tranquilWorks/gr86-cca-telemetry/docs/engineering/rvb22/current/EXECUTION_PLAN.md

# I32 procurement redline effectivity — 2026-09-15

The completed native procurement redline and affected numerical results are controlled by [../analyses/i32/procurement_redline/README.md](../analyses/i32/procurement_redline/README.md). Earlier source hashes, substitutions, power/thermal values and native-output pointers below are historical where superseded. Physical acceptance requirements remain in force; no historical criterion ledger is re-adjudicated by this update. The original text is preserved in `analyses/i32/procurement_redline/history/pre_redline/current/EXECUTION_PLAN.md`.

---

# I22 closure plan and current source

This iteration starts at I21 commit `550d87fea69147e131fd71603d02204a44c903f1` on PR #45. The user confirmed Adafruit 851 and 960 and requested another iteration. The complete I21 redline/criterion state was frozen before the checks. I22 corrects the accessory model, adds the omitted mechanical height allowance, completes independent package overlays and bounded via/RF reviews, and reevaluates all 290 original criteria. It closes six: LIB-02, LIB-08, VIA-06, SI-12, GPS-01 and MECH-03. Counts become 140 closed, 146 open and four not applicable. All 357 recorded redline identities remain visible; that history count is not the count of open criteria.

Confirmed inputs are Honeywell MIPAN2XX150PSAAX, the GR86 ASC harness per Timurrr, Adafruit 851/960, JLCPCB fabrication and dashboard use. Equivalent numerical power/RF/thermal models and circuit, firmware, mechanical and assembly corrections are authorized. The unchanged design case is 4.815 W, 65°C bulk air, 70°C landings and 70 kPa. No engine-bay environment or reduced dashboard requirement is introduced.

| Workstream | I22 result | Next closure action |
|---|---|---|
| Native CAD and target build | Verified I20 source remains current, with zero native findings and 153 resolved models. I22 does not change CAD or firmware. | Rerun the pinned native workflow after any CAD/firmware change and bind the resulting exports. |
| Package orientation and exposed pads | 12 manufacturer top/bottom overlays, 151 signal lands, all 20 GPS pad functions and 12 wrong-orientation negative controls pass. Exact exposed-pad net/mask/thermal construction reviewed. | Retain alternative-land and stencil conditions; obtain the original independent human drawing review under DRW-03. |
| Mechanical model and assembly | Full 1.71 mm height stack replaces 1.20 mm; 1,154 populated and 776 mated checks pass. Smallest separation is 0.120 mm at R408/T03. Cable uses 150 ±3 mm and a 2.0 mm OD receiving envelope. | Verify exact supplied plug dimensions, carrier/foil materials, retention and installed construction. Recheck every cooling revision against these bounds. |
| Via current and drilling | All 322 vias pass the conditional 2 A self-heating screen, maximum 5.103 K against 10 K. Nominal drills agree with native exports. | Resolve exact finished-hole/pin/hardware fit, drawing/DFM agreement and supplier minimum wall/fill/cap conditions. |
| Board RF and digital returns | Analysis-only SI-12 scope is justified by the existing 3,981,312-case board network, minimum 10.219 dB return loss and maximum 0.867 dB insertion loss. All 12 RF segments retain adjacent ground. | Keep actual stack/device allocations, antenna/bias and installed GPS criteria separate. Bound or reroute the 54 digital adjacent-plane interruptions; alternate ground presence alone is insufficient. |
| Accessory interface | User-confirmed 851/960 pair; typical 3.3 V current is 9.8 mA. Exact module detection and current-limit applicability reviewed. | Verify delivered bias voltage, hot/cold current, faults, miniature-plug dimensions and standard-SMA center contacts. |
| Thermal | Fine model remains 143.800°C maximum board region and mesh-sensitive. A 60°C-rated 851 cannot meet 65°C passive boundaries. | Resolve package/local-air data, mesh/topology bounds and a realizable cooling path. Settle accessory rating or verified installation environment; passive contact improvements cannot close that 5 K rating conflict. |
| Remaining original review | All criteria retain their original questions and evidence requirements. WCA-07 still lacks a guaranteed hot/low-current optical bound. | Advance the remaining design calculations, then supplier, independent-review and physical acceptance items according to their actual scope. |

For every subsequent iteration, freeze all open criteria and every newly observed redline. Record a disposition for each finding, including the correction, evidence or exact unmet condition. Select one coordinated revision only after reviewing its power, RF, thermal, populated clearance, materials and service effects together. Regenerate all affected native/model outputs, compare every original criterion with the exact candidate, preserve failed trials and repeat. A combined finding remains open when one of its constituent requirements remains unresolved.

The next board-changing iteration should address thermal paths and digital returns together. Preserve full load/environment bounds until an enforceable alternative is designed and verified. Evaluate candidate heat paths against the ESP32 antenna region, J401 cable, C206 tab, insulation and full 1.71 mm height stack before promoting the geometry. Reconcile current package boundaries before presenting board-region temperatures as device margins.

Physical unit, supplier-process, installed harness/ground, phone/vehicle, material lifetime and environmental requirements remain explicit in the register. PR #45 is the authorized forwarding destination. Fabrication, merge, flashing and live vehicle actions are outside this iteration.
