tranquilWorks/gr86-cca-telemetry/docs/engineering/rvb22/analyses/i32/QUALIFICATION_AND_SERVICE.md

# I32 procurement redline effectivity — 2026-09-15

The completed native procurement redline and affected numerical results are controlled by [procurement_redline/README.md](procurement_redline/README.md). Earlier source hashes, substitutions, power/thermal values and native-output pointers below are historical where superseded. Physical acceptance requirements remain in force; no historical criterion ledger is re-adjudicated by this update. The original text is preserved in `analyses/i32/procurement_redline/history/pre_redline/analyses/i32/QUALIFICATION_AND_SERVICE.md`.

---

# I32 qualification and service conditions

No hardware, vehicle connection, programming, supplier approval or physical test was performed. These are deterministic first-article acceptance instructions. Retained I26 oil, GPS, RF, CAN, installation and mechanical criteria continue to apply. The uncertainty rule is unchanged: a measured value plus its relevant uncertainty must stay inside an upper limit; subtract uncertainty for a lower limit. Model assumptions are not measurement tolerances.

| Gate | Setup and acceptance |
|---|---|
| Cold start and boot | At the defined normal input corners, including the retained4.75–5.25 V upstream interface, and component/temperature samples, record upstream5 V, isolated VIN, source3.3 V, main3.3 V at U201 ground, U152 PG, actual U151 EN, U153 CT/output, reset and both converter currents. Test no load,20 mA pre-reset,0.45 A boot/run and0.75 A from power-on. Exactly one reset release; no SNS retry or missing boot during normal startup. Confirm the pre-reset allocation independently; typical ESP32 EN-low current is not a hot maximum. |
| Load steps and release | Exercise0.45↔0.75 A and representative MCU/BLE loads with fast edges. After READY, main including ripple/uncertainty must remain above3.116050 V and at or below3.6 V, without unintended resets. Also record the source node separately. The derivative's16.51 mV lower and28.61 mV upper margins do not absorb unknown silicon dynamics automatically. |
| U151 reverse discharge | Test normal unplug, upstream UV/OV disconnect,10/100 ms reapplication, unequal auxiliary loads, and no externally imposed off-load. While source>0.3 V, isolated VIN minus source must remain≥−0.3 V, including differential-probe error. Correlate enabled bidirectional switch behavior, disabled reverse blocking, hot leakage and discharge transistor transfer behavior. Reset during an imposed supply fault is intentional; successful single recovery after a stable return is required. |
| Timing and startup dissipation | Verify C15933 nF at0.00876628–0.01461858 s/V and C16668 nF at0.01804688–0.03009768 s/V, the250 us allocated worst fault response, actual EN sequencing and reset delay180–420 ms. CT values extend TI's approximate formula beyond the10 nF table example; they are not guaranteed model constants. Confirm no U152/U153 thermal shutdown during worst storage charging or repeated recovery. |
| Input transient survival | Apply the exact source waveforms/R/L/repetition in `INPUT_PROTECTION.md`, including hot/cold clamp envelopes, on an isolated current-limited fixture. Simultaneously measure Q101 VDS/VGS/ID, controller VIN/UV/OV/SHDN/gate, D101 voltage/current, D102/D103/D105 clamp trajectories and downstream VIN5. Require Q101≤200 V and±20 V gate, D101≤600 V reverse, U101 per-pin limits, and the temperature-adjusted SOA/pulse bounds. No avalanche, latch-up, unintended fuse opening or permanent parameter drift is accepted. Functional UV/OV shutdown is expected; output-only measurements cannot prove component stress acceptance. |
| Short/fuse coordination | The LTC4367 voltage disconnect is not a current limiter. Confirm source fuse/wire protection, prospective fault current, ground-loss handling and clearing under the retained harness contract. Fuse nominal0.80 A²s is not a guaranteed clearing or pulse-survival limit. F101 local ambient≤105 C; apply its current-temperature/continuous derating. |
| Sustained power | Preserve160 MHz, BLE+3 dBm, Wi-Fi off,≤120 notifications/s, and sliding1 s/60 s main current≤0.45 A. Each converter must meet the retained≥80% condition or an approved partitioned measured-loss alternative. Additionally, actual total heat must remain within2.940859375 W. The worst leakage stack at exactly80% for both gives3.062582 W and is **not an accepted release state**. At U151 exactly80%, the same-budget calculation requires U121≥83.3396%; other efficiencies may be accepted only by a complete power-flow/heat calculation. Use simultaneous instantaneous V×I and avoid double-counting magnetic loss. |
| Hot soak and Rev A correlation | Use adopted C05/W02/T03, final enclosure/harness/orientation at65 C bulk cabin air. Immediate U201 air≤85 C; monitor shield, board hot region, U121/U151/U152/U153, both polymer capacitors, fuse, LED and cooling landings. Stabilize every monitored temperature at<0.1 C/min for30 consecutive minutes with zero unexpected resets/latch-ups. Continue the representative run long enough to cover the historical five-minute failure and final stabilization. A millisecond startup simulation does not prove that failure mechanism eliminated. |
| Thermal model correlation | The new actual-loss vector gives107.36427 C on0.25 mm mesh plus5.85646 C one-step allowance =113.22073 C board-region screen. The retained I25 heat vector on new copper gives113.39905 C similarly. Neither is mesh convergence, junction or immediate-air temperature. **The older112.88298 C physical correlation trigger remains in force**: exceeding it reopens correlation; I32 does not raise that acceptance trigger merely to pass. Actual loss/contact/air data must resolve the difference. C02 is not adopted. |
| Local component temperatures | TPS22953 conditional package calculations use51 K/W junction-to-board allocation (twice the typical metric), not a guaranteed maximum; confirm it or measure an adequate case/junction correlation. Both switches must remain below the130 C minimum thermal-shutdown onset during startup with margin. D102's allocated60 K/W junction-to-lead condition must be confirmed for the long dump. Keep polymer voltage≤60% rating at125 C, winding/package limits, the retained LED≤85 C local air /110 C junction limits, and all other source ratings. |
| Accessory and mechanics | Adafruit851 local environment≤60 C even during the65 C cabin test; relocation or an approved rated alternative is required if exceeded. Retain851+960 and PA1616D115200/10 Hz/PPS. Confirm C05/W02/T03 installed clearances,49 filled/capped vias and1.71 mm complete height stack. Native envelope minimum0.120 mm is not an installed fit measurement. |

The selected derivative can reasonably screen energy, tolerance and sequencing while its LM63615 equations remain approximate. The unmodified LM5164 isolated model ran; the older170-part closed vendor attempts aborted on both ngspice42 and47 before the requested end. They are retained failures, not177-part validation. The final first article must correlate these equations with silicon. Reopen component/copper/control choices on a failed gate; neither simulator convergence nor nominal parts justify waiving it.

## Power domains and safe service configuration

Normal source flow is R128→+5V→R151→U152→isolated3V3_VIN/C162→U151→3V3_SOURCE→R153→main+3V3. U153 connects the main to R158/C206 only when enabled. Q152/R165 drain the source on disable; R168 drains the isolated bulk capacitor. Selected TPS22953 has no QOD, so these discharge paths are intentional source components.

GPS has its own5 V-fed MIC5504 regulator. U402 is powered from main3V3 and buffers GPS TX/PPS toward the MCU; U404 is powered from GPS3V3 and buffers MCU TX/FIX toward GPS. Their SN74LVC2G125 Ioff behavior protects the opposite unpowered domain;220 ohm series parts and100 kohm pulls remain. The oil/excitation dividers use1 Mohm/4.02 kohm ahead of the main-powered OPA2333: ordinary5 V becomes about20 mV at the unpowered input, with limited current. Do not generalize this to arbitrary externally driven programmer or sensor fault voltages. [TI buffer power-off behavior](https://www.ti.com/lit/ds/symlink/sn74lvc2g125.pdf) supports the buffer-domain argument.

| Service configuration | Required isolation and verification |
|---|---|
| Normal12 V input | R128, R151 and R153 in the controlled fitted state. External programming voltage reference is sense-only; no second supply. |
| External5 V | Disconnect12 V and open R128 before applying the service5 V to the load side. R151 remains fitted and U152 sequences U151. Do not backfeed U121. |
| External3.3 V | Disconnect12 V/5 V and open R153 before applying service3.3 V to the main side. Do not power the U151 source from a programmer. U153/C206 may charge from this service supply. |
| UART/debug | Preserve EN, GPIO0, UART0 and all probe/Tag-Connect access. Do not drive UART pins into an unpowered module. Use an isolated, voltage-compatible adapter and source-defined references. No chassis-bonded programmer during vehicle operation. |

Never change isolation links while energized. Remove all sources, wait at least10 s, and measure upstream5 V, isolated VIN, source3V3, main3V3 and bulk capacitor below0.2 V before touching links. The delay covers more than five time constants of the maximum1.43208 mF reservoir with a1.06 kohm bleed; measurement remains controlling for faults or backpower. Probe ground clips must not short isolated sensor returns. Bottom probe access requires carrier removal as listed in the mechanical record.
