tranquilWorks/gr86-cca-telemetry/docs/engineering/rvb22/analyses/i32/WORKING_STATE.md

# Recovery addendum — 2026-09-14 UTC

**Digital closure update:** I32-RCV-FW-01 is closed by a genuine unchanged-source ESP32-S3 build at `CPUFreq=160`; the compiler log contains `-DF_CPU=160000000L` and all 28 preserved release checks pass. Evidence is under `recovery_20260914/firmware_160mhz/`. Historical 240 MHz images remain quarantined. Nothing was flashed or executed on hardware, and supplier, thermal-correlation, EMC, silicon, first-article, vehicle, and manufacturing-acceptance gates remain open.

---

# I32 delivery state

All four requested engineering areas have final source-bound digital dispositions. The 68 nF C166 repair resolves the real 4.75 V/cold 750 mA startup collapse under the declared bounded model, without changing controller gains, load limits or SNS thresholds. Final authored PCB45a2a679d9893d51fa641e539af45bc6ec1324169ea5f2226ecdea0ae2464da7; filled249d7b584af71605ee160c1ff425fda16a11b3ba93458bb243a722214c66ab30.

Completed: native KiCad9.0.9 zero ERC/DRC/unconnected/parity/exclusions,177STEP,135CADinputs,13postconditions; source audit preserves32firmwareinputs and49specialvias. Final34powercases and17inputcases are linked to exact full records in evidence/ACCEPTED_RECORDS.json. Power main3.13255965..3.57139192V; reverse−0.06700589V. Layout80paths/7views,23filled-groundpairs; ground11.28179/10.91904mohm within15/11mohm allocations. Mechanics1837checks/38probes,full1.71mm,nohits. Thermal finaltwo meshes/three vectors: same-budget board screen113.220731C; original112.8829809018675C physical trigger unchanged. Fixed2.940859375W; U12183.3396% required atU15180%/maxleakage. Physical/supplier gates are unperformed.

The 19 full-record ZIP containers retain622positive-size waveforms and one invalid zero-byte historical artifact from664experiment directories. All split parts and their original combined hashes were verified; the restore entry point reconstructed container16 and passed exact SHA/ZIP CRC. All42distribution files plus the distribution JSON have been saved. Exact compact records and source evidence are in Git. Older61-case I31 fullZIP and newer132-case summary-only remain distinct. Historical/narrow-voltage selected labels do not override current ACCEPTED_RECORDS.

Current product/manufacturing handoffs, findings, effectivity, replay commands and C166 bibliography are complete. The strict I32 package builder validates native_c166_68n_release and exact reuse of the prior firmware inputs/images. Its separate build report records the final package hash without self-reference. PR46 remains the existing draft branch; the Git commit containing this delivery and the final completion record identify the revision. No merge, order, hardware, firmware operation or messages are authorized. Intermediate execution details and rejected decisions are preserved in history/INTERMEDIATE_WORKING_STATE.md. Do not restart the completed analysis or promote historical selected labels to current evidence.
