tranquilWorks/gr86-cca-telemetry/docs/engineering/rvb22/analyses/i32/procurement_redline/CHANGED_PATHS.md

# Complete changed-path inventory

Compared with starting remote `1c934f9ddd7a1b823e5136484f525485472528f6`. Every changed path is enumerated below. SHA256, byte count and Git action are in [CHANGED_PATHS.json](CHANGED_PATHS.json). The index pair itself is also new. Raw waveform streams are preserved exactly as byte parts; see `spice/RAW_RECORD_MANIFEST.json` and `restore_waveforms.py`. Hosted verification follow-up changes are included; their scope is described in [CI_BINDINGS.md](CI_BINDINGS.md).

The catalog-only sourced successor is included; see [procurement completion](../procurement_completion/README.md). The qualified engineering baseline and its prior execution records are preserved.

## Authored native CAD, libraries and models (29)

- `docs/engineering/rvb22/candidate/cad/CANDIDATE_README.md`
- `docs/engineering/rvb22/candidate/cad/GR86_CCA_RevB.kicad_pcb`
- `docs/engineering/rvb22/candidate/cad/Input_Protection.kicad_sch`
- `docs/engineering/rvb22/candidate/cad/Power_3V3.kicad_sch`
- `docs/engineering/rvb22/candidate/cad/Power_5V.kicad_sch`
- `docs/engineering/rvb22/candidate/cad/libraries/RevB.kicad_sym`
- `docs/engineering/rvb22/candidate/cad/libraries/RevB.pretty/I32_FINISHED_R151.kicad_mod`
- `docs/engineering/rvb22/candidate/cad/libraries/RevB.pretty/I32_PROCUREMENT_C152.kicad_mod`
- `docs/engineering/rvb22/candidate/cad/libraries/RevB.pretty/I32_PROCUREMENT_C154.kicad_mod`
- `docs/engineering/rvb22/candidate/cad/libraries/RevB.pretty/I32_PROCUREMENT_C165.kicad_mod`
- `docs/engineering/rvb22/candidate/cad/libraries/RevB.pretty/I32_PROCUREMENT_L121.kicad_mod`
- `docs/engineering/rvb22/candidate/cad/libraries/RevB.pretty/I32_PROCUREMENT_R155.kicad_mod`
- `docs/engineering/rvb22/candidate/cad/libraries/RevB.pretty/I32_PROCUREMENT_R156.kicad_mod`
- `docs/engineering/rvb22/candidate/cad/libraries/RevB.pretty/I32_PROCUREMENT_R160.kicad_mod`
- `docs/engineering/rvb22/candidate/cad/libraries/RevB.pretty/I32_PROCUREMENT_R161.kicad_mod`
- `docs/engineering/rvb22/candidate/cad/libraries/RevB.pretty/I32_PROCUREMENT_R162.kicad_mod`
- `docs/engineering/rvb22/candidate/cad/libraries/RevB.pretty/I32_PROCUREMENT_R163.kicad_mod`
- `docs/engineering/rvb22/candidate/cad/libraries/RevB.pretty/I32_PROCUREMENT_R169.kicad_mod`
- `docs/engineering/rvb22/candidate/cad/libraries/RevB.pretty/I32_PROCUREMENT_R170.kicad_mod`
- `docs/engineering/rvb22/candidate/cad/libraries/RevB.pretty/I32_PROCUREMENT_U101.kicad_mod`
- `docs/engineering/rvb22/candidate/cad/models/ENVELOPE_I32_PROCUREMENT_L121.step`
- `docs/engineering/rvb22/candidate/cad/models/ENVELOPE_I32_PROCUREMENT_R155.step`
- `docs/engineering/rvb22/candidate/cad/models/ENVELOPE_I32_PROCUREMENT_R156.step`
- `docs/engineering/rvb22/candidate/cad/models/ENVELOPE_I32_PROCUREMENT_R160.step`
- `docs/engineering/rvb22/candidate/cad/models/ENVELOPE_I32_PROCUREMENT_R161.step`
- `docs/engineering/rvb22/candidate/cad/models/ENVELOPE_I32_PROCUREMENT_R162.step`
- `docs/engineering/rvb22/candidate/cad/models/ENVELOPE_I32_PROCUREMENT_R163.step`
- `docs/engineering/rvb22/candidate/cad/models/ENVELOPE_I32_PROCUREMENT_R169.step`
- `docs/engineering/rvb22/candidate/cad/models/ENVELOPE_I32_PROCUREMENT_R170.step`

## Current manufacturing and package (185)

- `docs/engineering/rvb22/current/i32_manufacturing/ASSEMBLY_AND_ACCEPTANCE.md`
- `docs/engineering/rvb22/current/i32_manufacturing/FIRMWARE_EFFECTIVITY.json`
- `docs/engineering/rvb22/current/i32_manufacturing/README.md`
- `docs/engineering/rvb22/current/i32_manufacturing/SOURCE_MANIFEST.json`
- `docs/engineering/rvb22/current/i32_manufacturing/assembly/COMPLETE_FITTED_BOM.csv`
- `docs/engineering/rvb22/current/i32_manufacturing/assembly/JLCPCB_BOM.csv`
- `docs/engineering/rvb22/current/i32_manufacturing/assembly/JLCPCB_CPL.csv`
- `docs/engineering/rvb22/current/i32_manufacturing/assembly/SOURCING_REQUIRED.csv`
- `docs/engineering/rvb22/current/i32_manufacturing/documentation/POPULATED_COMPONENTS.step`
- `docs/engineering/rvb22/current/i32_manufacturing/documentation/SCHEMATIC.pdf`
- `docs/engineering/rvb22/current/i32_manufacturing/documentation/SCHEMATIC_NETLIST.xml`
- `docs/engineering/rvb22/current/i32_manufacturing/editable_source/cad/CAN.kicad_sch`
- `docs/engineering/rvb22/current/i32_manufacturing/editable_source/cad/CANDIDATE_README.md`
- `docs/engineering/rvb22/current/i32_manufacturing/editable_source/cad/ESP32.kicad_sch`
- `docs/engineering/rvb22/current/i32_manufacturing/editable_source/cad/FITTED_REFERENCES.json`
- `docs/engineering/rvb22/current/i32_manufacturing/editable_source/cad/GPS.kicad_sch`
- `docs/engineering/rvb22/current/i32_manufacturing/editable_source/cad/GR86_CCA_RevB.kicad_dru`
- `docs/engineering/rvb22/current/i32_manufacturing/editable_source/cad/GR86_CCA_RevB.kicad_pcb`
- `docs/engineering/rvb22/current/i32_manufacturing/editable_source/cad/GR86_CCA_RevB.kicad_prl`
- `docs/engineering/rvb22/current/i32_manufacturing/editable_source/cad/GR86_CCA_RevB.kicad_pro`
- `docs/engineering/rvb22/current/i32_manufacturing/editable_source/cad/GR86_CCA_RevB.kicad_sch`
- `docs/engineering/rvb22/current/i32_manufacturing/editable_source/cad/Input_Protection.kicad_sch`
- `docs/engineering/rvb22/current/i32_manufacturing/editable_source/cad/LEDs_Status.kicad_sch`
- `docs/engineering/rvb22/current/i32_manufacturing/editable_source/cad/Oil_Pressure.kicad_sch`
- `docs/engineering/rvb22/current/i32_manufacturing/editable_source/cad/Power_3V3.kicad_sch`
- `docs/engineering/rvb22/current/i32_manufacturing/editable_source/cad/Power_5V.kicad_sch`
- `docs/engineering/rvb22/current/i32_manufacturing/editable_source/cad/Programming_Debug.kicad_sch`
- `docs/engineering/rvb22/current/i32_manufacturing/editable_source/cad/RVB22_POWER_CANDIDATE_ONLY.txt`
- `docs/engineering/rvb22/current/i32_manufacturing/editable_source/cad/Test_Points.kicad_sch`
- `docs/engineering/rvb22/current/i32_manufacturing/editable_source/cad/Vehicle_Interconnect.kicad_sch`
- `docs/engineering/rvb22/current/i32_manufacturing/editable_source/cad/fp-lib-table`
- `docs/engineering/rvb22/current/i32_manufacturing/editable_source/cad/libraries/RevB.kicad_sym`
- `docs/engineering/rvb22/current/i32_manufacturing/editable_source/cad/libraries/RevB.pretty/CDTop_PA1616D_20Pad_v06.kicad_mod`
- `docs/engineering/rvb22/current/i32_manufacturing/editable_source/cad/libraries/RevB.pretty/C_0402_1005Metric.kicad_mod`
- `docs/engineering/rvb22/current/i32_manufacturing/editable_source/cad/libraries/RevB.pretty/C_0603_1608Metric.kicad_mod`
- `docs/engineering/rvb22/current/i32_manufacturing/editable_source/cad/libraries/RevB.pretty/C_0603_1608Metric_RVB22_C154.kicad_mod`
- `docs/engineering/rvb22/current/i32_manufacturing/editable_source/cad/libraries/RevB.pretty/C_0603_1608Metric_RVB22_C205.kicad_mod`
- `docs/engineering/rvb22/current/i32_manufacturing/editable_source/cad/libraries/RevB.pretty/C_0805_2012Metric.kicad_mod`
- `docs/engineering/rvb22/current/i32_manufacturing/editable_source/cad/libraries/RevB.pretty/C_1210_3225Metric.kicad_mod`
- `docs/engineering/rvb22/current/i32_manufacturing/editable_source/cad/libraries/RevB.pretty/Coilcraft_MSS1246T_12x12.kicad_mod`
- `docs/engineering/rvb22/current/i32_manufacturing/editable_source/cad/libraries/RevB.pretty/Coilcraft_MSS1246T_12x12_RVB22_L121.kicad_mod`
- `docs/engineering/rvb22/current/i32_manufacturing/editable_source/cad/libraries/RevB.pretty/D_SMA.kicad_mod`
- `docs/engineering/rvb22/current/i32_manufacturing/editable_source/cad/libraries/RevB.pretty/D_SMB.kicad_mod`
- `docs/engineering/rvb22/current/i32_manufacturing/editable_source/cad/libraries/RevB.pretty/D_SMC.kicad_mod`
- `docs/engineering/rvb22/current/i32_manufacturing/editable_source/cad/libraries/RevB.pretty/D_SMC_RVB22_D103.kicad_mod`
- `docs/engineering/rvb22/current/i32_manufacturing/editable_source/cad/libraries/RevB.pretty/D_SOD-123F.kicad_mod`
- `docs/engineering/rvb22/current/i32_manufacturing/editable_source/cad/libraries/RevB.pretty/ESP32-S3-WROOM-1.kicad_mod`
- `docs/engineering/rvb22/current/i32_manufacturing/editable_source/cad/libraries/RevB.pretty/ESP32-S3-WROOM-1_RVB22_U201.kicad_mod`
- `docs/engineering/rvb22/current/i32_manufacturing/editable_source/cad/libraries/RevB.pretty/ESP32-S3-WROOM-1_RVB22_U201_TH48.kicad_mod`
- `docs/engineering/rvb22/current/i32_manufacturing/editable_source/cad/libraries/RevB.pretty/Fuse_Littelfuse-NANO2-885.kicad_mod`
- `docs/engineering/rvb22/current/i32_manufacturing/editable_source/cad/libraries/RevB.pretty/HTSSOP-16-1EP_4.4x5mm_P0.65mm_EP3.4x5mm_Mask2.46x2.31mm.kicad_mod`
- `docs/engineering/rvb22/current/i32_manufacturing/editable_source/cad/libraries/RevB.pretty/HTSSOP-16-1EP_4.4x5mm_P0.65mm_EP3.4x5mm_Mask2.46x2.31mm_RVB22_U151.kicad_mod`
- `docs/engineering/rvb22/current/i32_manufacturing/editable_source/cad/libraries/RevB.pretty/HTSSOP-16-1EP_4.4x5mm_P0.65mm_EP3x3mm.kicad_mod`
- `docs/engineering/rvb22/current/i32_manufacturing/editable_source/cad/libraries/RevB.pretty/Hirose_UFL_R_SMT_1_80_RevB.kicad_mod`
- `docs/engineering/rvb22/current/i32_manufacturing/editable_source/cad/libraries/RevB.pretty/I32_FINISHED_C159.kicad_mod`
- `docs/engineering/rvb22/current/i32_manufacturing/editable_source/cad/libraries/RevB.pretty/I32_FINISHED_C161.kicad_mod`
- `docs/engineering/rvb22/current/i32_manufacturing/editable_source/cad/libraries/RevB.pretty/I32_FINISHED_C162.kicad_mod`
- `docs/engineering/rvb22/current/i32_manufacturing/editable_source/cad/libraries/RevB.pretty/I32_FINISHED_C165.kicad_mod`
- `docs/engineering/rvb22/current/i32_manufacturing/editable_source/cad/libraries/RevB.pretty/I32_FINISHED_C166.kicad_mod`
- `docs/engineering/rvb22/current/i32_manufacturing/editable_source/cad/libraries/RevB.pretty/I32_FINISHED_C167.kicad_mod`
- `docs/engineering/rvb22/current/i32_manufacturing/editable_source/cad/libraries/RevB.pretty/I32_FINISHED_Q152.kicad_mod`
- `docs/engineering/rvb22/current/i32_manufacturing/editable_source/cad/libraries/RevB.pretty/I32_FINISHED_Q153.kicad_mod`
- `docs/engineering/rvb22/current/i32_manufacturing/editable_source/cad/libraries/RevB.pretty/I32_FINISHED_R151.kicad_mod`
- `docs/engineering/rvb22/current/i32_manufacturing/editable_source/cad/libraries/RevB.pretty/I32_FINISHED_R155.kicad_mod`
- `docs/engineering/rvb22/current/i32_manufacturing/editable_source/cad/libraries/RevB.pretty/I32_FINISHED_R156.kicad_mod`
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
- `docs/engineering/rvb22/current/i32_manufacturing/editable_source/cad/libraries/RevB.pretty/LED_0603_1608Metric.kicad_mod`
- `docs/engineering/rvb22/current/i32_manufacturing/editable_source/cad/libraries/RevB.pretty/L_Coilcraft_XAL5030-XXX.kicad_mod`
- `docs/engineering/rvb22/current/i32_manufacturing/editable_source/cad/libraries/RevB.pretty/MSOP-8_3x3mm_P0.65mm.kicad_mod`
- `docs/engineering/rvb22/current/i32_manufacturing/editable_source/cad/libraries/RevB.pretty/Molex_Micro-Fit_3.0_43045-1200_2x06_P3.00mm_Horizontal.kicad_mod`
- `docs/engineering/rvb22/current/i32_manufacturing/editable_source/cad/libraries/RevB.pretty/Molex_Micro-Fit_3.0_43045-1200_2x06_P3.00mm_Horizontal_RVB22_F1.kicad_mod`
- `docs/engineering/rvb22/current/i32_manufacturing/editable_source/cad/libraries/RevB.pretty/MountingHole_4.4mm_Outboard.kicad_mod`
- `docs/engineering/rvb22/current/i32_manufacturing/editable_source/cad/libraries/RevB.pretty/Murata_LQW18AS_1608.kicad_mod`
- `docs/engineering/rvb22/current/i32_manufacturing/editable_source/cad/libraries/RevB.pretty/Nexperia_SOD323_PMEG2010BEA.kicad_mod`
- `docs/engineering/rvb22/current/i32_manufacturing/editable_source/cad/libraries/RevB.pretty/PinHeader_1x02_P2.54mm_Vertical.kicad_mod`
- `docs/engineering/rvb22/current/i32_manufacturing/editable_source/cad/libraries/RevB.pretty/R_0603_1608Metric.kicad_mod`
- `docs/engineering/rvb22/current/i32_manufacturing/editable_source/cad/libraries/RevB.pretty/R_0603_1608Metric_RVB22_R155.kicad_mod`
- `docs/engineering/rvb22/current/i32_manufacturing/editable_source/cad/libraries/RevB.pretty/R_0603_1608Metric_RVB22_R156.kicad_mod`
- `docs/engineering/rvb22/current/i32_manufacturing/editable_source/cad/libraries/RevB.pretty/R_0603_1608Metric_RVB22_R157.kicad_mod`
- `docs/engineering/rvb22/current/i32_manufacturing/editable_source/cad/libraries/RevB.pretty/R_0603_1608Metric_RVB22_R203.kicad_mod`
- `docs/engineering/rvb22/current/i32_manufacturing/editable_source/cad/libraries/RevB.pretty/R_0805_2012Metric.kicad_mod`
- `docs/engineering/rvb22/current/i32_manufacturing/editable_source/cad/libraries/RevB.pretty/R_1206_3216Metric.kicad_mod`
- `docs/engineering/rvb22/current/i32_manufacturing/editable_source/cad/libraries/RevB.pretty/R_2512_6332Metric.kicad_mod`
- `docs/engineering/rvb22/current/i32_manufacturing/editable_source/cad/libraries/RevB.pretty/SOIC-8_3.9x4.9mm_P1.27mm.kicad_mod`
- `docs/engineering/rvb22/current/i32_manufacturing/editable_source/cad/libraries/RevB.pretty/SOT-23-5.kicad_mod`
- `docs/engineering/rvb22/current/i32_manufacturing/editable_source/cad/libraries/RevB.pretty/SOT-23.kicad_mod`
- `docs/engineering/rvb22/current/i32_manufacturing/editable_source/cad/libraries/RevB.pretty/SolderJumper-2_P1.3mm_Open_Pad1.0x1.5mm.kicad_mod`
- `docs/engineering/rvb22/current/i32_manufacturing/editable_source/cad/libraries/RevB.pretty/TDK_CGA4J1_33N_I32.kicad_mod`
- `docs/engineering/rvb22/current/i32_manufacturing/editable_source/cad/libraries/RevB.pretty/TI_DDA0008B_4214849B.kicad_mod`
- `docs/engineering/rvb22/current/i32_manufacturing/editable_source/cad/libraries/RevB.pretty/TI_DPY0002A_TPD1E05U06_SMDMask.kicad_mod`
- `docs/engineering/rvb22/current/i32_manufacturing/editable_source/cad/libraries/RevB.pretty/TI_DQC0010A_I32.kicad_mod`
- `docs/engineering/rvb22/current/i32_manufacturing/editable_source/cad/libraries/RevB.pretty/TI_DRB0008J_TCAN3403.kicad_mod`
- `docs/engineering/rvb22/current/i32_manufacturing/editable_source/cad/libraries/RevB.pretty/TI_PWP0016A_TPS2660.kicad_mod`
- `docs/engineering/rvb22/current/i32_manufacturing/editable_source/cad/libraries/RevB.pretty/TO-252-2.kicad_mod`
- `docs/engineering/rvb22/current/i32_manufacturing/editable_source/cad/libraries/RevB.pretty/TPS3808_DBV0006A.kicad_mod`
- `docs/engineering/rvb22/current/i32_manufacturing/editable_source/cad/libraries/RevB.pretty/Tag-Connect_TC2030-IDC-NL_2x03_P1.27mm_Vertical.kicad_mod`
- `docs/engineering/rvb22/current/i32_manufacturing/editable_source/cad/libraries/RevB.pretty/TestPoint_Pad_D1.5mm.kicad_mod`
- `docs/engineering/rvb22/current/i32_manufacturing/editable_source/cad/libraries/RevB.pretty/U.FL_Hirose_U.FL-R-SMT-1_Vertical.kicad_mod`
- `docs/engineering/rvb22/current/i32_manufacturing/editable_source/cad/libraries/RevB.pretty/VSSOP-8_2.3x2mm_P0.5mm.kicad_mod`
- `docs/engineering/rvb22/current/i32_manufacturing/editable_source/cad/libraries/RevB.pretty/WSLP0603_MANUFACTURER.kicad_mod`
- `docs/engineering/rvb22/current/i32_manufacturing/editable_source/cad/libraries/RevB.pretty/WSLP0603_MANUFACTURER_R153.kicad_mod`
- `docs/engineering/rvb22/current/i32_manufacturing/editable_source/cad/libraries/RevB.pretty/Wurth_61300211121_1x02.kicad_mod`
- `docs/engineering/rvb22/current/i32_manufacturing/editable_source/cad/models/ENVELOPE_CDTop_PA1616D_20Pad_v06.step`
- `docs/engineering/rvb22/current/i32_manufacturing/editable_source/cad/models/ENVELOPE_C_0603_1608Metric_RVB22_C205.step`
- `docs/engineering/rvb22/current/i32_manufacturing/editable_source/cad/models/ENVELOPE_Coilcraft_MSS1246T_12x12_RVB22_L121.step`
- `docs/engineering/rvb22/current/i32_manufacturing/editable_source/cad/models/ENVELOPE_Fuse_Littelfuse-NANO2-885.step`
- `docs/engineering/rvb22/current/i32_manufacturing/editable_source/cad/models/ENVELOPE_HTSSOP-16-1EP_4.4x5mm_P0.65mm_EP3.4x5mm_Mask2.46x2.31mm_RVB22_U151.step`
- `docs/engineering/rvb22/current/i32_manufacturing/editable_source/cad/models/ENVELOPE_I32_PROCUREMENT_L121.step`
- `docs/engineering/rvb22/current/i32_manufacturing/editable_source/cad/models/ENVELOPE_I32_PROCUREMENT_R155.step`
- `docs/engineering/rvb22/current/i32_manufacturing/editable_source/cad/models/ENVELOPE_I32_PROCUREMENT_R156.step`
- `docs/engineering/rvb22/current/i32_manufacturing/editable_source/cad/models/ENVELOPE_I32_PROCUREMENT_R160.step`
- `docs/engineering/rvb22/current/i32_manufacturing/editable_source/cad/models/ENVELOPE_I32_PROCUREMENT_R161.step`
- `docs/engineering/rvb22/current/i32_manufacturing/editable_source/cad/models/ENVELOPE_I32_PROCUREMENT_R162.step`
- `docs/engineering/rvb22/current/i32_manufacturing/editable_source/cad/models/ENVELOPE_I32_PROCUREMENT_R163.step`
- `docs/engineering/rvb22/current/i32_manufacturing/editable_source/cad/models/ENVELOPE_I32_PROCUREMENT_R169.step`
- `docs/engineering/rvb22/current/i32_manufacturing/editable_source/cad/models/ENVELOPE_I32_PROCUREMENT_R170.step`
- `docs/engineering/rvb22/current/i32_manufacturing/editable_source/cad/models/ENVELOPE_KEMET_C1210_10u50V.step`
- `docs/engineering/rvb22/current/i32_manufacturing/editable_source/cad/models/ENVELOPE_KEMET_T598_X_7343_Median_RVB22_C206.step`
- `docs/engineering/rvb22/current/i32_manufacturing/editable_source/cad/models/ENVELOPE_Molex_Micro-Fit_3.0_43045-1200_2x06_P3.00mm_Horizontal_RVB22_F1.step`
- `docs/engineering/rvb22/current/i32_manufacturing/editable_source/cad/models/ENVELOPE_Murata_LQW18AS_1608.step`
- `docs/engineering/rvb22/current/i32_manufacturing/editable_source/cad/models/ENVELOPE_R_0603_1608Metric_RVB22_R155.step`
- `docs/engineering/rvb22/current/i32_manufacturing/editable_source/cad/models/ENVELOPE_R_0603_1608Metric_RVB22_R156.step`
- `docs/engineering/rvb22/current/i32_manufacturing/editable_source/cad/models/ENVELOPE_R_0603_1608Metric_RVB22_R157.step`
- `docs/engineering/rvb22/current/i32_manufacturing/editable_source/cad/models/ENVELOPE_R_0603_1608Metric_RVB22_R203.step`
- `docs/engineering/rvb22/current/i32_manufacturing/editable_source/cad/models/ENVELOPE_TDK_CGA4J1_33N_I32.step`
- `docs/engineering/rvb22/current/i32_manufacturing/editable_source/cad/models/ENVELOPE_TDK_CGA5L1_68N_I32.step`
- `docs/engineering/rvb22/current/i32_manufacturing/editable_source/cad/models/ENVELOPE_TI_DDA0008B_4214849B.step`
- `docs/engineering/rvb22/current/i32_manufacturing/editable_source/cad/models/ENVELOPE_TI_DPY0002A_TPD1E05U06_SMDMask.step`
- `docs/engineering/rvb22/current/i32_manufacturing/editable_source/cad/models/ENVELOPE_TI_DQC0010A_I32.step`
- `docs/engineering/rvb22/current/i32_manufacturing/editable_source/cad/models/ENVELOPE_TI_DRB0008J_TCAN3403.step`
- `docs/engineering/rvb22/current/i32_manufacturing/editable_source/cad/models/ENVELOPE_TI_PWP0016A_TPS2660.step`
- `docs/engineering/rvb22/current/i32_manufacturing/editable_source/cad/models/ENVELOPE_TPS3808_DBV0006A.step`
- `docs/engineering/rvb22/current/i32_manufacturing/editable_source/cad/models/ENVELOPE_WSL2512_I32_R158.step`
- `docs/engineering/rvb22/current/i32_manufacturing/editable_source/cad/models/ENVELOPE_WSLP0603_MANUFACTURER.step`
- `docs/engineering/rvb22/current/i32_manufacturing/editable_source/cad/models/ENVELOPE_WSLP0603_MANUFACTURER_R153.step`
- `docs/engineering/rvb22/current/i32_manufacturing/editable_source/cad/sym-lib-table`
- `docs/engineering/rvb22/current/i32_manufacturing/fabrication/JLCPCB_GERBERS.zip`
- `docs/engineering/rvb22/current/i32_manufacturing/fabrication/PCB_NETLIST.d356`
- `docs/engineering/rvb22/current/i32_manufacturing/fabrication/gerbers/GR86_CCA_RevB-B_Cu.gbl`
- `docs/engineering/rvb22/current/i32_manufacturing/fabrication/gerbers/GR86_CCA_RevB-B_Mask.gbs`
- `docs/engineering/rvb22/current/i32_manufacturing/fabrication/gerbers/GR86_CCA_RevB-B_Paste.gbp`
- `docs/engineering/rvb22/current/i32_manufacturing/fabrication/gerbers/GR86_CCA_RevB-B_Silkscreen.gbo`
- `docs/engineering/rvb22/current/i32_manufacturing/fabrication/gerbers/GR86_CCA_RevB-Edge_Cuts.gm1`
- `docs/engineering/rvb22/current/i32_manufacturing/fabrication/gerbers/GR86_CCA_RevB-F_Cu.gtl`
- `docs/engineering/rvb22/current/i32_manufacturing/fabrication/gerbers/GR86_CCA_RevB-F_Mask.gts`
- `docs/engineering/rvb22/current/i32_manufacturing/fabrication/gerbers/GR86_CCA_RevB-F_Paste.gtp`
- `docs/engineering/rvb22/current/i32_manufacturing/fabrication/gerbers/GR86_CCA_RevB-F_Silkscreen.gto`
- `docs/engineering/rvb22/current/i32_manufacturing/fabrication/gerbers/GR86_CCA_RevB-In1_Cu.g1`
- `docs/engineering/rvb22/current/i32_manufacturing/fabrication/gerbers/GR86_CCA_RevB-In2_Cu.g2`
- `docs/engineering/rvb22/current/i32_manufacturing/fabrication/gerbers/GR86_CCA_RevB-NPTH.drl`
- `docs/engineering/rvb22/current/i32_manufacturing/fabrication/gerbers/GR86_CCA_RevB-PTH.drl`
- `docs/engineering/rvb22/current/i32_manufacturing/fabrication/gerbers/GR86_CCA_RevB-job.gbrjob`
- `docs/engineering/rvb22/product/GR86_I32_PROCUREMENT_REDLINE.zip`

## Final regenerated native evidence (210)

- `docs/engineering/rvb22/analyses/i32/procurement_redline/native_final/COPIED_SOURCE_INVENTORY.json`
- `docs/engineering/rvb22/analyses/i32/procurement_redline/native_final/DRC.json`
- `docs/engineering/rvb22/analyses/i32/procurement_redline/native_final/ERC.json`
- `docs/engineering/rvb22/analyses/i32/procurement_redline/native_final/MODEL_RESOLUTION.json`
- `docs/engineering/rvb22/analyses/i32/procurement_redline/native_final/OUTPUT_MANIFEST.json`
- `docs/engineering/rvb22/analyses/i32/procurement_redline/native_final/PCB_NETLIST.d356`
- `docs/engineering/rvb22/analyses/i32/procurement_redline/native_final/RESULT.json`
- `docs/engineering/rvb22/analyses/i32/procurement_redline/native_final/REVIEW_BOM.csv`
- `docs/engineering/rvb22/analyses/i32/procurement_redline/native_final/REVIEW_COMPONENTS.step`
- `docs/engineering/rvb22/analyses/i32/procurement_redline/native_final/REVIEW_POSITIONS.csv`
- `docs/engineering/rvb22/analyses/i32/procurement_redline/native_final/REVIEW_SCHEMATIC.pdf`
- `docs/engineering/rvb22/analyses/i32/procurement_redline/native_final/SCHEMATIC_NETLIST.xml`
- `docs/engineering/rvb22/analyses/i32/procurement_redline/native_final/candidate_kicad/CAN.kicad_sch`
- `docs/engineering/rvb22/analyses/i32/procurement_redline/native_final/candidate_kicad/CANDIDATE_README.md`
- `docs/engineering/rvb22/analyses/i32/procurement_redline/native_final/candidate_kicad/ESP32.kicad_sch`
- `docs/engineering/rvb22/analyses/i32/procurement_redline/native_final/candidate_kicad/FITTED_REFERENCES.json`
- `docs/engineering/rvb22/analyses/i32/procurement_redline/native_final/candidate_kicad/GPS.kicad_sch`
- `docs/engineering/rvb22/analyses/i32/procurement_redline/native_final/candidate_kicad/GR86_CCA_RevB.kicad_dru`
- `docs/engineering/rvb22/analyses/i32/procurement_redline/native_final/candidate_kicad/GR86_CCA_RevB.kicad_pcb`
- `docs/engineering/rvb22/analyses/i32/procurement_redline/native_final/candidate_kicad/GR86_CCA_RevB.kicad_prl`
- `docs/engineering/rvb22/analyses/i32/procurement_redline/native_final/candidate_kicad/GR86_CCA_RevB.kicad_pro`
- `docs/engineering/rvb22/analyses/i32/procurement_redline/native_final/candidate_kicad/GR86_CCA_RevB.kicad_sch`
- `docs/engineering/rvb22/analyses/i32/procurement_redline/native_final/candidate_kicad/Input_Protection.kicad_sch`
- `docs/engineering/rvb22/analyses/i32/procurement_redline/native_final/candidate_kicad/LEDs_Status.kicad_sch`
- `docs/engineering/rvb22/analyses/i32/procurement_redline/native_final/candidate_kicad/Oil_Pressure.kicad_sch`
- `docs/engineering/rvb22/analyses/i32/procurement_redline/native_final/candidate_kicad/Power_3V3.kicad_sch`
- `docs/engineering/rvb22/analyses/i32/procurement_redline/native_final/candidate_kicad/Power_5V.kicad_sch`
- `docs/engineering/rvb22/analyses/i32/procurement_redline/native_final/candidate_kicad/Programming_Debug.kicad_sch`
- `docs/engineering/rvb22/analyses/i32/procurement_redline/native_final/candidate_kicad/RVB22_POWER_CANDIDATE_ONLY.txt`
- `docs/engineering/rvb22/analyses/i32/procurement_redline/native_final/candidate_kicad/Test_Points.kicad_sch`
- `docs/engineering/rvb22/analyses/i32/procurement_redline/native_final/candidate_kicad/Vehicle_Interconnect.kicad_sch`
- `docs/engineering/rvb22/analyses/i32/procurement_redline/native_final/candidate_kicad/fp-lib-table`
- `docs/engineering/rvb22/analyses/i32/procurement_redline/native_final/candidate_kicad/libraries/RevB.kicad_sym`
- `docs/engineering/rvb22/analyses/i32/procurement_redline/native_final/candidate_kicad/libraries/RevB.pretty/CDTop_PA1616D_20Pad_v06.kicad_mod`
- `docs/engineering/rvb22/analyses/i32/procurement_redline/native_final/candidate_kicad/libraries/RevB.pretty/C_0402_1005Metric.kicad_mod`
- `docs/engineering/rvb22/analyses/i32/procurement_redline/native_final/candidate_kicad/libraries/RevB.pretty/C_0603_1608Metric.kicad_mod`
- `docs/engineering/rvb22/analyses/i32/procurement_redline/native_final/candidate_kicad/libraries/RevB.pretty/C_0603_1608Metric_RVB22_C154.kicad_mod`
- `docs/engineering/rvb22/analyses/i32/procurement_redline/native_final/candidate_kicad/libraries/RevB.pretty/C_0603_1608Metric_RVB22_C205.kicad_mod`
- `docs/engineering/rvb22/analyses/i32/procurement_redline/native_final/candidate_kicad/libraries/RevB.pretty/C_0805_2012Metric.kicad_mod`
- `docs/engineering/rvb22/analyses/i32/procurement_redline/native_final/candidate_kicad/libraries/RevB.pretty/C_1210_3225Metric.kicad_mod`
- `docs/engineering/rvb22/analyses/i32/procurement_redline/native_final/candidate_kicad/libraries/RevB.pretty/Coilcraft_MSS1246T_12x12.kicad_mod`
- `docs/engineering/rvb22/analyses/i32/procurement_redline/native_final/candidate_kicad/libraries/RevB.pretty/Coilcraft_MSS1246T_12x12_RVB22_L121.kicad_mod`
- `docs/engineering/rvb22/analyses/i32/procurement_redline/native_final/candidate_kicad/libraries/RevB.pretty/D_SMA.kicad_mod`
- `docs/engineering/rvb22/analyses/i32/procurement_redline/native_final/candidate_kicad/libraries/RevB.pretty/D_SMB.kicad_mod`
- `docs/engineering/rvb22/analyses/i32/procurement_redline/native_final/candidate_kicad/libraries/RevB.pretty/D_SMC.kicad_mod`
- `docs/engineering/rvb22/analyses/i32/procurement_redline/native_final/candidate_kicad/libraries/RevB.pretty/D_SMC_RVB22_D103.kicad_mod`
- `docs/engineering/rvb22/analyses/i32/procurement_redline/native_final/candidate_kicad/libraries/RevB.pretty/D_SOD-123F.kicad_mod`
- `docs/engineering/rvb22/analyses/i32/procurement_redline/native_final/candidate_kicad/libraries/RevB.pretty/ESP32-S3-WROOM-1.kicad_mod`
- `docs/engineering/rvb22/analyses/i32/procurement_redline/native_final/candidate_kicad/libraries/RevB.pretty/ESP32-S3-WROOM-1_RVB22_U201.kicad_mod`
- `docs/engineering/rvb22/analyses/i32/procurement_redline/native_final/candidate_kicad/libraries/RevB.pretty/ESP32-S3-WROOM-1_RVB22_U201_TH48.kicad_mod`
- `docs/engineering/rvb22/analyses/i32/procurement_redline/native_final/candidate_kicad/libraries/RevB.pretty/Fuse_Littelfuse-NANO2-885.kicad_mod`
- `docs/engineering/rvb22/analyses/i32/procurement_redline/native_final/candidate_kicad/libraries/RevB.pretty/HTSSOP-16-1EP_4.4x5mm_P0.65mm_EP3.4x5mm_Mask2.46x2.31mm.kicad_mod`
- `docs/engineering/rvb22/analyses/i32/procurement_redline/native_final/candidate_kicad/libraries/RevB.pretty/HTSSOP-16-1EP_4.4x5mm_P0.65mm_EP3.4x5mm_Mask2.46x2.31mm_RVB22_U151.kicad_mod`
- `docs/engineering/rvb22/analyses/i32/procurement_redline/native_final/candidate_kicad/libraries/RevB.pretty/HTSSOP-16-1EP_4.4x5mm_P0.65mm_EP3x3mm.kicad_mod`
- `docs/engineering/rvb22/analyses/i32/procurement_redline/native_final/candidate_kicad/libraries/RevB.pretty/Hirose_UFL_R_SMT_1_80_RevB.kicad_mod`
- `docs/engineering/rvb22/analyses/i32/procurement_redline/native_final/candidate_kicad/libraries/RevB.pretty/I32_FINISHED_C159.kicad_mod`
- `docs/engineering/rvb22/analyses/i32/procurement_redline/native_final/candidate_kicad/libraries/RevB.pretty/I32_FINISHED_C161.kicad_mod`
- `docs/engineering/rvb22/analyses/i32/procurement_redline/native_final/candidate_kicad/libraries/RevB.pretty/I32_FINISHED_C162.kicad_mod`
- `docs/engineering/rvb22/analyses/i32/procurement_redline/native_final/candidate_kicad/libraries/RevB.pretty/I32_FINISHED_C165.kicad_mod`
- `docs/engineering/rvb22/analyses/i32/procurement_redline/native_final/candidate_kicad/libraries/RevB.pretty/I32_FINISHED_C166.kicad_mod`
- `docs/engineering/rvb22/analyses/i32/procurement_redline/native_final/candidate_kicad/libraries/RevB.pretty/I32_FINISHED_C167.kicad_mod`
- `docs/engineering/rvb22/analyses/i32/procurement_redline/native_final/candidate_kicad/libraries/RevB.pretty/I32_FINISHED_Q152.kicad_mod`
- `docs/engineering/rvb22/analyses/i32/procurement_redline/native_final/candidate_kicad/libraries/RevB.pretty/I32_FINISHED_Q153.kicad_mod`
- `docs/engineering/rvb22/analyses/i32/procurement_redline/native_final/candidate_kicad/libraries/RevB.pretty/I32_FINISHED_R151.kicad_mod`
- `docs/engineering/rvb22/analyses/i32/procurement_redline/native_final/candidate_kicad/libraries/RevB.pretty/I32_FINISHED_R155.kicad_mod`
- `docs/engineering/rvb22/analyses/i32/procurement_redline/native_final/candidate_kicad/libraries/RevB.pretty/I32_FINISHED_R156.kicad_mod`
- `docs/engineering/rvb22/analyses/i32/procurement_redline/native_final/candidate_kicad/libraries/RevB.pretty/I32_FINISHED_R158.kicad_mod`
- `docs/engineering/rvb22/analyses/i32/procurement_redline/native_final/candidate_kicad/libraries/RevB.pretty/I32_FINISHED_R159.kicad_mod`
- `docs/engineering/rvb22/analyses/i32/procurement_redline/native_final/candidate_kicad/libraries/RevB.pretty/I32_FINISHED_R160.kicad_mod`
- `docs/engineering/rvb22/analyses/i32/procurement_redline/native_final/candidate_kicad/libraries/RevB.pretty/I32_FINISHED_R161.kicad_mod`
- `docs/engineering/rvb22/analyses/i32/procurement_redline/native_final/candidate_kicad/libraries/RevB.pretty/I32_FINISHED_R162.kicad_mod`
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
- `docs/engineering/rvb22/analyses/i32/procurement_redline/native_final/candidate_kicad/libraries/RevB.pretty/L_Coilcraft_XAL5030-XXX.kicad_mod`
- `docs/engineering/rvb22/analyses/i32/procurement_redline/native_final/candidate_kicad/libraries/RevB.pretty/MSOP-8_3x3mm_P0.65mm.kicad_mod`
- `docs/engineering/rvb22/analyses/i32/procurement_redline/native_final/candidate_kicad/libraries/RevB.pretty/Molex_Micro-Fit_3.0_43045-1200_2x06_P3.00mm_Horizontal.kicad_mod`
- `docs/engineering/rvb22/analyses/i32/procurement_redline/native_final/candidate_kicad/libraries/RevB.pretty/Molex_Micro-Fit_3.0_43045-1200_2x06_P3.00mm_Horizontal_RVB22_F1.kicad_mod`
- `docs/engineering/rvb22/analyses/i32/procurement_redline/native_final/candidate_kicad/libraries/RevB.pretty/MountingHole_4.4mm_Outboard.kicad_mod`
- `docs/engineering/rvb22/analyses/i32/procurement_redline/native_final/candidate_kicad/libraries/RevB.pretty/Murata_LQW18AS_1608.kicad_mod`
- `docs/engineering/rvb22/analyses/i32/procurement_redline/native_final/candidate_kicad/libraries/RevB.pretty/Nexperia_SOD323_PMEG2010BEA.kicad_mod`
- `docs/engineering/rvb22/analyses/i32/procurement_redline/native_final/candidate_kicad/libraries/RevB.pretty/PinHeader_1x02_P2.54mm_Vertical.kicad_mod`
- `docs/engineering/rvb22/analyses/i32/procurement_redline/native_final/candidate_kicad/libraries/RevB.pretty/R_0603_1608Metric.kicad_mod`
- `docs/engineering/rvb22/analyses/i32/procurement_redline/native_final/candidate_kicad/libraries/RevB.pretty/R_0603_1608Metric_RVB22_R155.kicad_mod`
- `docs/engineering/rvb22/analyses/i32/procurement_redline/native_final/candidate_kicad/libraries/RevB.pretty/R_0603_1608Metric_RVB22_R156.kicad_mod`
- `docs/engineering/rvb22/analyses/i32/procurement_redline/native_final/candidate_kicad/libraries/RevB.pretty/R_0603_1608Metric_RVB22_R157.kicad_mod`
- `docs/engineering/rvb22/analyses/i32/procurement_redline/native_final/candidate_kicad/libraries/RevB.pretty/R_0603_1608Metric_RVB22_R203.kicad_mod`
- `docs/engineering/rvb22/analyses/i32/procurement_redline/native_final/candidate_kicad/libraries/RevB.pretty/R_0805_2012Metric.kicad_mod`
- `docs/engineering/rvb22/analyses/i32/procurement_redline/native_final/candidate_kicad/libraries/RevB.pretty/R_1206_3216Metric.kicad_mod`
- `docs/engineering/rvb22/analyses/i32/procurement_redline/native_final/candidate_kicad/libraries/RevB.pretty/R_2512_6332Metric.kicad_mod`
- `docs/engineering/rvb22/analyses/i32/procurement_redline/native_final/candidate_kicad/libraries/RevB.pretty/SOIC-8_3.9x4.9mm_P1.27mm.kicad_mod`
- `docs/engineering/rvb22/analyses/i32/procurement_redline/native_final/candidate_kicad/libraries/RevB.pretty/SOT-23-5.kicad_mod`
- `docs/engineering/rvb22/analyses/i32/procurement_redline/native_final/candidate_kicad/libraries/RevB.pretty/SOT-23.kicad_mod`
- `docs/engineering/rvb22/analyses/i32/procurement_redline/native_final/candidate_kicad/libraries/RevB.pretty/SolderJumper-2_P1.3mm_Open_Pad1.0x1.5mm.kicad_mod`
- `docs/engineering/rvb22/analyses/i32/procurement_redline/native_final/candidate_kicad/libraries/RevB.pretty/TDK_CGA4J1_33N_I32.kicad_mod`
- `docs/engineering/rvb22/analyses/i32/procurement_redline/native_final/candidate_kicad/libraries/RevB.pretty/TI_DDA0008B_4214849B.kicad_mod`
- `docs/engineering/rvb22/analyses/i32/procurement_redline/native_final/candidate_kicad/libraries/RevB.pretty/TI_DPY0002A_TPD1E05U06_SMDMask.kicad_mod`
- `docs/engineering/rvb22/analyses/i32/procurement_redline/native_final/candidate_kicad/libraries/RevB.pretty/TI_DQC0010A_I32.kicad_mod`
- `docs/engineering/rvb22/analyses/i32/procurement_redline/native_final/candidate_kicad/libraries/RevB.pretty/TI_DRB0008J_TCAN3403.kicad_mod`
- `docs/engineering/rvb22/analyses/i32/procurement_redline/native_final/candidate_kicad/libraries/RevB.pretty/TI_PWP0016A_TPS2660.kicad_mod`
- `docs/engineering/rvb22/analyses/i32/procurement_redline/native_final/candidate_kicad/libraries/RevB.pretty/TO-252-2.kicad_mod`
- `docs/engineering/rvb22/analyses/i32/procurement_redline/native_final/candidate_kicad/libraries/RevB.pretty/TPS3808_DBV0006A.kicad_mod`
- `docs/engineering/rvb22/analyses/i32/procurement_redline/native_final/candidate_kicad/libraries/RevB.pretty/Tag-Connect_TC2030-IDC-NL_2x03_P1.27mm_Vertical.kicad_mod`
- `docs/engineering/rvb22/analyses/i32/procurement_redline/native_final/candidate_kicad/libraries/RevB.pretty/TestPoint_Pad_D1.5mm.kicad_mod`
- `docs/engineering/rvb22/analyses/i32/procurement_redline/native_final/candidate_kicad/libraries/RevB.pretty/U.FL_Hirose_U.FL-R-SMT-1_Vertical.kicad_mod`
- `docs/engineering/rvb22/analyses/i32/procurement_redline/native_final/candidate_kicad/libraries/RevB.pretty/VSSOP-8_2.3x2mm_P0.5mm.kicad_mod`
- `docs/engineering/rvb22/analyses/i32/procurement_redline/native_final/candidate_kicad/libraries/RevB.pretty/WSLP0603_MANUFACTURER.kicad_mod`
- `docs/engineering/rvb22/analyses/i32/procurement_redline/native_final/candidate_kicad/libraries/RevB.pretty/WSLP0603_MANUFACTURER_R153.kicad_mod`
- `docs/engineering/rvb22/analyses/i32/procurement_redline/native_final/candidate_kicad/libraries/RevB.pretty/Wurth_61300211121_1x02.kicad_mod`
- `docs/engineering/rvb22/analyses/i32/procurement_redline/native_final/candidate_kicad/models/ENVELOPE_CDTop_PA1616D_20Pad_v06.step`
- `docs/engineering/rvb22/analyses/i32/procurement_redline/native_final/candidate_kicad/models/ENVELOPE_C_0603_1608Metric_RVB22_C205.step`
- `docs/engineering/rvb22/analyses/i32/procurement_redline/native_final/candidate_kicad/models/ENVELOPE_Coilcraft_MSS1246T_12x12_RVB22_L121.step`
- `docs/engineering/rvb22/analyses/i32/procurement_redline/native_final/candidate_kicad/models/ENVELOPE_Fuse_Littelfuse-NANO2-885.step`
- `docs/engineering/rvb22/analyses/i32/procurement_redline/native_final/candidate_kicad/models/ENVELOPE_HTSSOP-16-1EP_4.4x5mm_P0.65mm_EP3.4x5mm_Mask2.46x2.31mm_RVB22_U151.step`
- `docs/engineering/rvb22/analyses/i32/procurement_redline/native_final/candidate_kicad/models/ENVELOPE_I32_PROCUREMENT_L121.step`
- `docs/engineering/rvb22/analyses/i32/procurement_redline/native_final/candidate_kicad/models/ENVELOPE_I32_PROCUREMENT_R155.step`
- `docs/engineering/rvb22/analyses/i32/procurement_redline/native_final/candidate_kicad/models/ENVELOPE_I32_PROCUREMENT_R156.step`
- `docs/engineering/rvb22/analyses/i32/procurement_redline/native_final/candidate_kicad/models/ENVELOPE_I32_PROCUREMENT_R160.step`
- `docs/engineering/rvb22/analyses/i32/procurement_redline/native_final/candidate_kicad/models/ENVELOPE_I32_PROCUREMENT_R161.step`
- `docs/engineering/rvb22/analyses/i32/procurement_redline/native_final/candidate_kicad/models/ENVELOPE_I32_PROCUREMENT_R162.step`
- `docs/engineering/rvb22/analyses/i32/procurement_redline/native_final/candidate_kicad/models/ENVELOPE_I32_PROCUREMENT_R163.step`
- `docs/engineering/rvb22/analyses/i32/procurement_redline/native_final/candidate_kicad/models/ENVELOPE_I32_PROCUREMENT_R169.step`
- `docs/engineering/rvb22/analyses/i32/procurement_redline/native_final/candidate_kicad/models/ENVELOPE_I32_PROCUREMENT_R170.step`
- `docs/engineering/rvb22/analyses/i32/procurement_redline/native_final/candidate_kicad/models/ENVELOPE_KEMET_C1210_10u50V.step`
- `docs/engineering/rvb22/analyses/i32/procurement_redline/native_final/candidate_kicad/models/ENVELOPE_KEMET_T598_X_7343_Median_RVB22_C206.step`
- `docs/engineering/rvb22/analyses/i32/procurement_redline/native_final/candidate_kicad/models/ENVELOPE_Molex_Micro-Fit_3.0_43045-1200_2x06_P3.00mm_Horizontal_RVB22_F1.step`
- `docs/engineering/rvb22/analyses/i32/procurement_redline/native_final/candidate_kicad/models/ENVELOPE_Murata_LQW18AS_1608.step`
- `docs/engineering/rvb22/analyses/i32/procurement_redline/native_final/candidate_kicad/models/ENVELOPE_R_0603_1608Metric_RVB22_R155.step`
- `docs/engineering/rvb22/analyses/i32/procurement_redline/native_final/candidate_kicad/models/ENVELOPE_R_0603_1608Metric_RVB22_R156.step`
- `docs/engineering/rvb22/analyses/i32/procurement_redline/native_final/candidate_kicad/models/ENVELOPE_R_0603_1608Metric_RVB22_R157.step`
- `docs/engineering/rvb22/analyses/i32/procurement_redline/native_final/candidate_kicad/models/ENVELOPE_R_0603_1608Metric_RVB22_R203.step`
- `docs/engineering/rvb22/analyses/i32/procurement_redline/native_final/candidate_kicad/models/ENVELOPE_TDK_CGA4J1_33N_I32.step`
- `docs/engineering/rvb22/analyses/i32/procurement_redline/native_final/candidate_kicad/models/ENVELOPE_TDK_CGA5L1_68N_I32.step`
- `docs/engineering/rvb22/analyses/i32/procurement_redline/native_final/candidate_kicad/models/ENVELOPE_TI_DDA0008B_4214849B.step`
- `docs/engineering/rvb22/analyses/i32/procurement_redline/native_final/candidate_kicad/models/ENVELOPE_TI_DPY0002A_TPD1E05U06_SMDMask.step`
- `docs/engineering/rvb22/analyses/i32/procurement_redline/native_final/candidate_kicad/models/ENVELOPE_TI_DQC0010A_I32.step`
- `docs/engineering/rvb22/analyses/i32/procurement_redline/native_final/candidate_kicad/models/ENVELOPE_TI_DRB0008J_TCAN3403.step`
- `docs/engineering/rvb22/analyses/i32/procurement_redline/native_final/candidate_kicad/models/ENVELOPE_TI_PWP0016A_TPS2660.step`
- `docs/engineering/rvb22/analyses/i32/procurement_redline/native_final/candidate_kicad/models/ENVELOPE_TPS3808_DBV0006A.step`
- `docs/engineering/rvb22/analyses/i32/procurement_redline/native_final/candidate_kicad/models/ENVELOPE_WSL2512_I32_R158.step`
- `docs/engineering/rvb22/analyses/i32/procurement_redline/native_final/candidate_kicad/models/ENVELOPE_WSLP0603_MANUFACTURER.step`
- `docs/engineering/rvb22/analyses/i32/procurement_redline/native_final/candidate_kicad/models/ENVELOPE_WSLP0603_MANUFACTURER_R153.step`
- `docs/engineering/rvb22/analyses/i32/procurement_redline/native_final/candidate_kicad/sym-lib-table`
- `docs/engineering/rvb22/analyses/i32/procurement_redline/native_final/logs/component_positions.stderr`
- `docs/engineering/rvb22/analyses/i32/procurement_redline/native_final/logs/component_positions.stdout`
- `docs/engineering/rvb22/analyses/i32/procurement_redline/native_final/logs/component_step.stderr`
- `docs/engineering/rvb22/analyses/i32/procurement_redline/native_final/logs/component_step.stdout`
- `docs/engineering/rvb22/analyses/i32/procurement_redline/native_final/logs/drc.stderr`
- `docs/engineering/rvb22/analyses/i32/procurement_redline/native_final/logs/drc.stdout`
- `docs/engineering/rvb22/analyses/i32/procurement_redline/native_final/logs/drills.stderr`
- `docs/engineering/rvb22/analyses/i32/procurement_redline/native_final/logs/drills.stdout`
- `docs/engineering/rvb22/analyses/i32/procurement_redline/native_final/logs/erc.stderr`
- `docs/engineering/rvb22/analyses/i32/procurement_redline/native_final/logs/erc.stdout`
- `docs/engineering/rvb22/analyses/i32/procurement_redline/native_final/logs/gerbers.stderr`
- `docs/engineering/rvb22/analyses/i32/procurement_redline/native_final/logs/gerbers.stdout`
- `docs/engineering/rvb22/analyses/i32/procurement_redline/native_final/logs/kicad_version.stderr`
- `docs/engineering/rvb22/analyses/i32/procurement_redline/native_final/logs/kicad_version.stdout`
- `docs/engineering/rvb22/analyses/i32/procurement_redline/native_final/logs/pcb_netlist.stderr`
- `docs/engineering/rvb22/analyses/i32/procurement_redline/native_final/logs/pcb_netlist.stdout`
- `docs/engineering/rvb22/analyses/i32/procurement_redline/native_final/logs/pcbnew_version.stderr`
- `docs/engineering/rvb22/analyses/i32/procurement_redline/native_final/logs/pcbnew_version.stdout`
- `docs/engineering/rvb22/analyses/i32/procurement_redline/native_final/logs/schematic_bom.stderr`
- `docs/engineering/rvb22/analyses/i32/procurement_redline/native_final/logs/schematic_bom.stdout`
- `docs/engineering/rvb22/analyses/i32/procurement_redline/native_final/logs/schematic_netlist.stderr`
- `docs/engineering/rvb22/analyses/i32/procurement_redline/native_final/logs/schematic_netlist.stdout`
- `docs/engineering/rvb22/analyses/i32/procurement_redline/native_final/logs/schematic_pdf.stderr`
- `docs/engineering/rvb22/analyses/i32/procurement_redline/native_final/logs/schematic_pdf.stdout`
- `docs/engineering/rvb22/analyses/i32/procurement_redline/native_final/logs/zone_refill.stderr`
- `docs/engineering/rvb22/analyses/i32/procurement_redline/native_final/logs/zone_refill.stdout`
- `docs/engineering/rvb22/analyses/i32/procurement_redline/native_final/model_export/GR86_CCA_RevB.kicad_pcb`
- `docs/engineering/rvb22/analyses/i32/procurement_redline/native_final/review_gerbers/GR86_CCA_RevB-B_Cu.gbl`
- `docs/engineering/rvb22/analyses/i32/procurement_redline/native_final/review_gerbers/GR86_CCA_RevB-B_Mask.gbs`
- `docs/engineering/rvb22/analyses/i32/procurement_redline/native_final/review_gerbers/GR86_CCA_RevB-B_Paste.gbp`
- `docs/engineering/rvb22/analyses/i32/procurement_redline/native_final/review_gerbers/GR86_CCA_RevB-B_Silkscreen.gbo`
- `docs/engineering/rvb22/analyses/i32/procurement_redline/native_final/review_gerbers/GR86_CCA_RevB-Edge_Cuts.gm1`
- `docs/engineering/rvb22/analyses/i32/procurement_redline/native_final/review_gerbers/GR86_CCA_RevB-F_Cu.gtl`
- `docs/engineering/rvb22/analyses/i32/procurement_redline/native_final/review_gerbers/GR86_CCA_RevB-F_Mask.gts`
- `docs/engineering/rvb22/analyses/i32/procurement_redline/native_final/review_gerbers/GR86_CCA_RevB-F_Paste.gtp`
- `docs/engineering/rvb22/analyses/i32/procurement_redline/native_final/review_gerbers/GR86_CCA_RevB-F_Silkscreen.gto`
- `docs/engineering/rvb22/analyses/i32/procurement_redline/native_final/review_gerbers/GR86_CCA_RevB-In1_Cu.g1`
- `docs/engineering/rvb22/analyses/i32/procurement_redline/native_final/review_gerbers/GR86_CCA_RevB-In2_Cu.g2`
- `docs/engineering/rvb22/analyses/i32/procurement_redline/native_final/review_gerbers/GR86_CCA_RevB-NPTH.drl`
- `docs/engineering/rvb22/analyses/i32/procurement_redline/native_final/review_gerbers/GR86_CCA_RevB-PTH.drl`
- `docs/engineering/rvb22/analyses/i32/procurement_redline/native_final/review_gerbers/GR86_CCA_RevB-job.gbrjob`

## Other evidence/review and verification code (1582)

- `.github/workflows/convergence02-thermal.yml`
- `.github/workflows/convergence04-release-thermal.yml`
- `.github/workflows/desktop-due-diligence.yml`
- `.github/workflows/desktop-feedback-native.yml`
- `.github/workflows/i27-final-clearance.yml`
- `.github/workflows/rvb22-native.yml`
- `docs/engineering/rvb22/EXECUTION_PLAN_CURRENT.md`
- `docs/engineering/rvb22/FINAL_GATES.json`
- `docs/engineering/rvb22/FINAL_REVIEW_REGISTER.json`
- `docs/engineering/rvb22/GR86_CCA_RevB_Board_Vetting_Summary.md`
- `docs/engineering/rvb22/README.md`
- `docs/engineering/rvb22/analyses/convergence_01/native_binding.py`
- `docs/engineering/rvb22/analyses/convergence_01/native_exports.py`
- `docs/engineering/rvb22/analyses/convergence_01/run_review.py`
- `docs/engineering/rvb22/analyses/convergence_01/tests/test_review.py`
- `docs/engineering/rvb22/analyses/convergence_01/thermal_native.py`
- `docs/engineering/rvb22/analyses/i32/ADOPTED_ROUTE_INVENTORY.json`
- `docs/engineering/rvb22/analyses/i32/AUTHORED_CHANGES.json`
- `docs/engineering/rvb22/analyses/i32/DESIGN_AND_MODEL_BASIS.md`
- `docs/engineering/rvb22/analyses/i32/FINAL_EVIDENCE.json`
- `docs/engineering/rvb22/analyses/i32/FINDINGS_REGISTER.json`
- `docs/engineering/rvb22/analyses/i32/INPUT_RESULTS.json`
- `docs/engineering/rvb22/analyses/i32/LAYOUT_ASSESSMENT.md`
- `docs/engineering/rvb22/analyses/i32/POWER_RESULTS.json`
- `docs/engineering/rvb22/analyses/i32/QUALIFICATION_AND_SERVICE.md`
- `docs/engineering/rvb22/analyses/i32/README.md`
- `docs/engineering/rvb22/analyses/i32/SOURCE_AUDIT.json`
- `docs/engineering/rvb22/analyses/i32/SOURCE_BINDING.json`
- `docs/engineering/rvb22/analyses/i32/THERMAL_RESULTS.json`
- `docs/engineering/rvb22/analyses/i32/final_procurement_spice_qual.py`
- `docs/engineering/rvb22/analyses/i32/mechanical_check.py`
- `docs/engineering/rvb22/analyses/i32/procurement_redline/.gitignore`
- `docs/engineering/rvb22/analyses/i32/procurement_redline/ADOPTED_ROUTE_INVENTORY.json`
- `docs/engineering/rvb22/analyses/i32/procurement_redline/AUTHORED_CHANGES.json`
- `docs/engineering/rvb22/analyses/i32/procurement_redline/AUTHORED_REDLINE.json`
- `docs/engineering/rvb22/analyses/i32/procurement_redline/CI_BINDINGS.md`
- `docs/engineering/rvb22/analyses/i32/procurement_redline/EXPLICIT_COPPER.json`
- `docs/engineering/rvb22/analyses/i32/procurement_redline/EXPLICIT_COPPER_FINAL.json`
- `docs/engineering/rvb22/analyses/i32/procurement_redline/FINAL_REDLINE_VERIFICATION.json`
- `docs/engineering/rvb22/analyses/i32/procurement_redline/LIVE_JLC_SOURCEABILITY.json`
- `docs/engineering/rvb22/analyses/i32/procurement_redline/MANUFACTURING_RECONCILIATION.json`
- `docs/engineering/rvb22/analyses/i32/procurement_redline/METADATA_ONLY_REBIND.json`
- `docs/engineering/rvb22/analyses/i32/procurement_redline/NATIVE_BINDING_TESTS.log`
- `docs/engineering/rvb22/analyses/i32/procurement_redline/PACKAGE_QUALIFICATION.json`
- `docs/engineering/rvb22/analyses/i32/procurement_redline/RAW_PART_VERIFICATION.log`
- `docs/engineering/rvb22/analyses/i32/procurement_redline/README.md`
- `docs/engineering/rvb22/analyses/i32/procurement_redline/REVIEW_EFFECTIVITY.json`
- `docs/engineering/rvb22/analyses/i32/procurement_redline/REVIEW_REGISTER_UPDATE.json`
- `docs/engineering/rvb22/analyses/i32/procurement_redline/ROUTING_REDLINE.json`
- `docs/engineering/rvb22/analyses/i32/procurement_redline/SOURCE_AUDIT.json`
- `docs/engineering/rvb22/analyses/i32/procurement_redline/SOURCE_BINDING.json`
- `docs/engineering/rvb22/analyses/i32/procurement_redline/THERMAL_RESULTS.json`
- `docs/engineering/rvb22/analyses/i32/procurement_redline/VISUAL_REVIEW.json`
- `docs/engineering/rvb22/analyses/i32/procurement_redline/apply_redline.py`
- `docs/engineering/rvb22/analyses/i32/procurement_redline/ci_verify.py`
- `docs/engineering/rvb22/analyses/i32/procurement_redline/filled_returns/FILLED_GROUND_CONNECTIVITY.json`
- `docs/engineering/rvb22/analyses/i32/procurement_redline/filled_returns/Ground_returns.png`
- `docs/engineering/rvb22/analyses/i32/procurement_redline/filled_returns_final/FILLED_GROUND_CONNECTIVITY.json`
- `docs/engineering/rvb22/analyses/i32/procurement_redline/filled_returns_final/Ground_returns.png`
- `docs/engineering/rvb22/analyses/i32/procurement_redline/finalize_redline.py`
- `docs/engineering/rvb22/analyses/i32/procurement_redline/generate_manufacturing.py`
- `docs/engineering/rvb22/analyses/i32/procurement_redline/ground.log`
- `docs/engineering/rvb22/analyses/i32/procurement_redline/ground/GROUND_PLANE_REFINED.json`
- `docs/engineering/rvb22/analyses/i32/procurement_redline/ground/GROUND_RETURN_CONTRACT.json`
- `docs/engineering/rvb22/analyses/i32/procurement_redline/ground_final.log`
- `docs/engineering/rvb22/analyses/i32/procurement_redline/ground_final/GROUND_PLANE_REFINED.json`
- `docs/engineering/rvb22/analyses/i32/procurement_redline/ground_final/GROUND_RETURN_CONTRACT.json`
- `docs/engineering/rvb22/analyses/i32/procurement_redline/history/01_larger_pads_findings.json`
- `docs/engineering/rvb22/analyses/i32/procurement_redline/history/02_routes_findings.json`
- `docs/engineering/rvb22/analyses/i32/procurement_redline/history/native_01/COPIED_SOURCE_INVENTORY.json`
- `docs/engineering/rvb22/analyses/i32/procurement_redline/history/native_01/OUTPUT_MANIFEST.json`
- `docs/engineering/rvb22/analyses/i32/procurement_redline/history/native_01/RESULT.json`
- `docs/engineering/rvb22/analyses/i32/procurement_redline/history/native_01/logs/kicad_version.stderr`
- `docs/engineering/rvb22/analyses/i32/procurement_redline/history/native_01/logs/kicad_version.stdout`
- `docs/engineering/rvb22/analyses/i32/procurement_redline/history/native_01/logs/pcbnew_version.stderr`
- `docs/engineering/rvb22/analyses/i32/procurement_redline/history/native_01/logs/pcbnew_version.stdout`
- `docs/engineering/rvb22/analyses/i32/procurement_redline/history/native_02/COPIED_SOURCE_INVENTORY.json`
- `docs/engineering/rvb22/analyses/i32/procurement_redline/history/native_02/ERC.json`
- `docs/engineering/rvb22/analyses/i32/procurement_redline/history/native_02/MODEL_RESOLUTION.json`
- `docs/engineering/rvb22/analyses/i32/procurement_redline/history/native_02/OUTPUT_MANIFEST.json`
- `docs/engineering/rvb22/analyses/i32/procurement_redline/history/native_02/RESULT.json`
- `docs/engineering/rvb22/analyses/i32/procurement_redline/history/native_02/SCHEMATIC_NETLIST.xml`
- `docs/engineering/rvb22/analyses/i32/procurement_redline/history/native_02/candidate_kicad/CAN.kicad_sch`
- `docs/engineering/rvb22/analyses/i32/procurement_redline/history/native_02/candidate_kicad/CANDIDATE_README.md`
- `docs/engineering/rvb22/analyses/i32/procurement_redline/history/native_02/candidate_kicad/ESP32.kicad_sch`
- `docs/engineering/rvb22/analyses/i32/procurement_redline/history/native_02/candidate_kicad/FITTED_REFERENCES.json`
- `docs/engineering/rvb22/analyses/i32/procurement_redline/history/native_02/candidate_kicad/GPS.kicad_sch`
- `docs/engineering/rvb22/analyses/i32/procurement_redline/history/native_02/candidate_kicad/GR86_CCA_RevB.kicad_dru`
- `docs/engineering/rvb22/analyses/i32/procurement_redline/history/native_02/candidate_kicad/GR86_CCA_RevB.kicad_pcb`
- `docs/engineering/rvb22/analyses/i32/procurement_redline/history/native_02/candidate_kicad/GR86_CCA_RevB.kicad_prl`
- `docs/engineering/rvb22/analyses/i32/procurement_redline/history/native_02/candidate_kicad/GR86_CCA_RevB.kicad_pro`
- `docs/engineering/rvb22/analyses/i32/procurement_redline/history/native_02/candidate_kicad/GR86_CCA_RevB.kicad_sch`
- `docs/engineering/rvb22/analyses/i32/procurement_redline/history/native_02/candidate_kicad/Input_Protection.kicad_sch`
- `docs/engineering/rvb22/analyses/i32/procurement_redline/history/native_02/candidate_kicad/LEDs_Status.kicad_sch`
- `docs/engineering/rvb22/analyses/i32/procurement_redline/history/native_02/candidate_kicad/Oil_Pressure.kicad_sch`
- `docs/engineering/rvb22/analyses/i32/procurement_redline/history/native_02/candidate_kicad/Power_3V3.kicad_sch`
- `docs/engineering/rvb22/analyses/i32/procurement_redline/history/native_02/candidate_kicad/Power_5V.kicad_sch`
- `docs/engineering/rvb22/analyses/i32/procurement_redline/history/native_02/candidate_kicad/Programming_Debug.kicad_sch`
- `docs/engineering/rvb22/analyses/i32/procurement_redline/history/native_02/candidate_kicad/RVB22_POWER_CANDIDATE_ONLY.txt`
- `docs/engineering/rvb22/analyses/i32/procurement_redline/history/native_02/candidate_kicad/Test_Points.kicad_sch`
- `docs/engineering/rvb22/analyses/i32/procurement_redline/history/native_02/candidate_kicad/Vehicle_Interconnect.kicad_sch`
- `docs/engineering/rvb22/analyses/i32/procurement_redline/history/native_02/candidate_kicad/fp-lib-table`
- `docs/engineering/rvb22/analyses/i32/procurement_redline/history/native_02/candidate_kicad/libraries/RevB.kicad_sym`
- `docs/engineering/rvb22/analyses/i32/procurement_redline/history/native_02/candidate_kicad/libraries/RevB.pretty/CDTop_PA1616D_20Pad_v06.kicad_mod`
- `docs/engineering/rvb22/analyses/i32/procurement_redline/history/native_02/candidate_kicad/libraries/RevB.pretty/C_0402_1005Metric.kicad_mod`
- `docs/engineering/rvb22/analyses/i32/procurement_redline/history/native_02/candidate_kicad/libraries/RevB.pretty/C_0603_1608Metric.kicad_mod`
- `docs/engineering/rvb22/analyses/i32/procurement_redline/history/native_02/candidate_kicad/libraries/RevB.pretty/C_0603_1608Metric_RVB22_C154.kicad_mod`
- `docs/engineering/rvb22/analyses/i32/procurement_redline/history/native_02/candidate_kicad/libraries/RevB.pretty/C_0603_1608Metric_RVB22_C205.kicad_mod`
- `docs/engineering/rvb22/analyses/i32/procurement_redline/history/native_02/candidate_kicad/libraries/RevB.pretty/C_0805_2012Metric.kicad_mod`
- `docs/engineering/rvb22/analyses/i32/procurement_redline/history/native_02/candidate_kicad/libraries/RevB.pretty/C_1210_3225Metric.kicad_mod`
- `docs/engineering/rvb22/analyses/i32/procurement_redline/history/native_02/candidate_kicad/libraries/RevB.pretty/Coilcraft_MSS1246T_12x12.kicad_mod`
- `docs/engineering/rvb22/analyses/i32/procurement_redline/history/native_02/candidate_kicad/libraries/RevB.pretty/Coilcraft_MSS1246T_12x12_RVB22_L121.kicad_mod`
- `docs/engineering/rvb22/analyses/i32/procurement_redline/history/native_02/candidate_kicad/libraries/RevB.pretty/D_SMA.kicad_mod`
- `docs/engineering/rvb22/analyses/i32/procurement_redline/history/native_02/candidate_kicad/libraries/RevB.pretty/D_SMB.kicad_mod`
- `docs/engineering/rvb22/analyses/i32/procurement_redline/history/native_02/candidate_kicad/libraries/RevB.pretty/D_SMC.kicad_mod`
- `docs/engineering/rvb22/analyses/i32/procurement_redline/history/native_02/candidate_kicad/libraries/RevB.pretty/D_SMC_RVB22_D103.kicad_mod`
- `docs/engineering/rvb22/analyses/i32/procurement_redline/history/native_02/candidate_kicad/libraries/RevB.pretty/D_SOD-123F.kicad_mod`
- `docs/engineering/rvb22/analyses/i32/procurement_redline/history/native_02/candidate_kicad/libraries/RevB.pretty/ESP32-S3-WROOM-1.kicad_mod`
- `docs/engineering/rvb22/analyses/i32/procurement_redline/history/native_02/candidate_kicad/libraries/RevB.pretty/ESP32-S3-WROOM-1_RVB22_U201.kicad_mod`
- `docs/engineering/rvb22/analyses/i32/procurement_redline/history/native_02/candidate_kicad/libraries/RevB.pretty/ESP32-S3-WROOM-1_RVB22_U201_TH48.kicad_mod`
- `docs/engineering/rvb22/analyses/i32/procurement_redline/history/native_02/candidate_kicad/libraries/RevB.pretty/Fuse_Littelfuse-NANO2-885.kicad_mod`
- `docs/engineering/rvb22/analyses/i32/procurement_redline/history/native_02/candidate_kicad/libraries/RevB.pretty/HTSSOP-16-1EP_4.4x5mm_P0.65mm_EP3.4x5mm_Mask2.46x2.31mm.kicad_mod`
- `docs/engineering/rvb22/analyses/i32/procurement_redline/history/native_02/candidate_kicad/libraries/RevB.pretty/HTSSOP-16-1EP_4.4x5mm_P0.65mm_EP3.4x5mm_Mask2.46x2.31mm_RVB22_U151.kicad_mod`
- `docs/engineering/rvb22/analyses/i32/procurement_redline/history/native_02/candidate_kicad/libraries/RevB.pretty/HTSSOP-16-1EP_4.4x5mm_P0.65mm_EP3x3mm.kicad_mod`
- `docs/engineering/rvb22/analyses/i32/procurement_redline/history/native_02/candidate_kicad/libraries/RevB.pretty/Hirose_UFL_R_SMT_1_80_RevB.kicad_mod`
- `docs/engineering/rvb22/analyses/i32/procurement_redline/history/native_02/candidate_kicad/libraries/RevB.pretty/I32_FINISHED_C159.kicad_mod`
- `docs/engineering/rvb22/analyses/i32/procurement_redline/history/native_02/candidate_kicad/libraries/RevB.pretty/I32_FINISHED_C161.kicad_mod`
- `docs/engineering/rvb22/analyses/i32/procurement_redline/history/native_02/candidate_kicad/libraries/RevB.pretty/I32_FINISHED_C162.kicad_mod`
- `docs/engineering/rvb22/analyses/i32/procurement_redline/history/native_02/candidate_kicad/libraries/RevB.pretty/I32_FINISHED_C165.kicad_mod`
- `docs/engineering/rvb22/analyses/i32/procurement_redline/history/native_02/candidate_kicad/libraries/RevB.pretty/I32_FINISHED_C166.kicad_mod`
- `docs/engineering/rvb22/analyses/i32/procurement_redline/history/native_02/candidate_kicad/libraries/RevB.pretty/I32_FINISHED_C167.kicad_mod`
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
- `docs/engineering/rvb22/analyses/i32/procurement_redline/history/native_02/candidate_kicad/libraries/RevB.pretty/I32_PROCUREMENT_R161.kicad_mod`
- `docs/engineering/rvb22/analyses/i32/procurement_redline/history/native_02/candidate_kicad/libraries/RevB.pretty/I32_PROCUREMENT_R162.kicad_mod`
- `docs/engineering/rvb22/analyses/i32/procurement_redline/history/native_02/candidate_kicad/libraries/RevB.pretty/I32_PROCUREMENT_R163.kicad_mod`
- `docs/engineering/rvb22/analyses/i32/procurement_redline/history/native_02/candidate_kicad/libraries/RevB.pretty/I32_PROCUREMENT_R169.kicad_mod`
- `docs/engineering/rvb22/analyses/i32/procurement_redline/history/native_02/candidate_kicad/libraries/RevB.pretty/I32_PROCUREMENT_R170.kicad_mod`
- `docs/engineering/rvb22/analyses/i32/procurement_redline/history/native_02/candidate_kicad/libraries/RevB.pretty/I32_PROCUREMENT_U101.kicad_mod`
- `docs/engineering/rvb22/analyses/i32/procurement_redline/history/native_02/candidate_kicad/libraries/RevB.pretty/KEMET_C1210_10u50V.kicad_mod`
- `docs/engineering/rvb22/analyses/i32/procurement_redline/history/native_02/candidate_kicad/libraries/RevB.pretty/KEMET_T598_X_7343_Median.kicad_mod`
- `docs/engineering/rvb22/analyses/i32/procurement_redline/history/native_02/candidate_kicad/libraries/RevB.pretty/KEMET_T598_X_7343_Median_RVB22_C206.kicad_mod`
- `docs/engineering/rvb22/analyses/i32/procurement_redline/history/native_02/candidate_kicad/libraries/RevB.pretty/LED_0603_1608Metric.kicad_mod`
- `docs/engineering/rvb22/analyses/i32/procurement_redline/history/native_02/candidate_kicad/libraries/RevB.pretty/L_Coilcraft_XAL5030-XXX.kicad_mod`
- `docs/engineering/rvb22/analyses/i32/procurement_redline/history/native_02/candidate_kicad/libraries/RevB.pretty/MSOP-8_3x3mm_P0.65mm.kicad_mod`
- `docs/engineering/rvb22/analyses/i32/procurement_redline/history/native_02/candidate_kicad/libraries/RevB.pretty/Molex_Micro-Fit_3.0_43045-1200_2x06_P3.00mm_Horizontal.kicad_mod`
- `docs/engineering/rvb22/analyses/i32/procurement_redline/history/native_02/candidate_kicad/libraries/RevB.pretty/Molex_Micro-Fit_3.0_43045-1200_2x06_P3.00mm_Horizontal_RVB22_F1.kicad_mod`
- `docs/engineering/rvb22/analyses/i32/procurement_redline/history/native_02/candidate_kicad/libraries/RevB.pretty/MountingHole_4.4mm_Outboard.kicad_mod`
- `docs/engineering/rvb22/analyses/i32/procurement_redline/history/native_02/candidate_kicad/libraries/RevB.pretty/Murata_LQW18AS_1608.kicad_mod`
- `docs/engineering/rvb22/analyses/i32/procurement_redline/history/native_02/candidate_kicad/libraries/RevB.pretty/Nexperia_SOD323_PMEG2010BEA.kicad_mod`
- `docs/engineering/rvb22/analyses/i32/procurement_redline/history/native_02/candidate_kicad/libraries/RevB.pretty/PinHeader_1x02_P2.54mm_Vertical.kicad_mod`
- `docs/engineering/rvb22/analyses/i32/procurement_redline/history/native_02/candidate_kicad/libraries/RevB.pretty/R_0603_1608Metric.kicad_mod`
- `docs/engineering/rvb22/analyses/i32/procurement_redline/history/native_02/candidate_kicad/libraries/RevB.pretty/R_0603_1608Metric_RVB22_R155.kicad_mod`
- `docs/engineering/rvb22/analyses/i32/procurement_redline/history/native_02/candidate_kicad/libraries/RevB.pretty/R_0603_1608Metric_RVB22_R156.kicad_mod`
- `docs/engineering/rvb22/analyses/i32/procurement_redline/history/native_02/candidate_kicad/libraries/RevB.pretty/R_0603_1608Metric_RVB22_R157.kicad_mod`
- `docs/engineering/rvb22/analyses/i32/procurement_redline/history/native_02/candidate_kicad/libraries/RevB.pretty/R_0603_1608Metric_RVB22_R203.kicad_mod`
- `docs/engineering/rvb22/analyses/i32/procurement_redline/history/native_02/candidate_kicad/libraries/RevB.pretty/R_0805_2012Metric.kicad_mod`
- `docs/engineering/rvb22/analyses/i32/procurement_redline/history/native_02/candidate_kicad/libraries/RevB.pretty/R_1206_3216Metric.kicad_mod`
- `docs/engineering/rvb22/analyses/i32/procurement_redline/history/native_02/candidate_kicad/libraries/RevB.pretty/R_2512_6332Metric.kicad_mod`
- `docs/engineering/rvb22/analyses/i32/procurement_redline/history/native_02/candidate_kicad/libraries/RevB.pretty/SOIC-8_3.9x4.9mm_P1.27mm.kicad_mod`
- `docs/engineering/rvb22/analyses/i32/procurement_redline/history/native_02/candidate_kicad/libraries/RevB.pretty/SOT-23-5.kicad_mod`
- `docs/engineering/rvb22/analyses/i32/procurement_redline/history/native_02/candidate_kicad/libraries/RevB.pretty/SOT-23.kicad_mod`
- `docs/engineering/rvb22/analyses/i32/procurement_redline/history/native_02/candidate_kicad/libraries/RevB.pretty/SolderJumper-2_P1.3mm_Open_Pad1.0x1.5mm.kicad_mod`
- `docs/engineering/rvb22/analyses/i32/procurement_redline/history/native_02/candidate_kicad/libraries/RevB.pretty/TDK_CGA4J1_33N_I32.kicad_mod`
- `docs/engineering/rvb22/analyses/i32/procurement_redline/history/native_02/candidate_kicad/libraries/RevB.pretty/TI_DDA0008B_4214849B.kicad_mod`
- `docs/engineering/rvb22/analyses/i32/procurement_redline/history/native_02/candidate_kicad/libraries/RevB.pretty/TI_DPY0002A_TPD1E05U06_SMDMask.kicad_mod`
- `docs/engineering/rvb22/analyses/i32/procurement_redline/history/native_02/candidate_kicad/libraries/RevB.pretty/TI_DQC0010A_I32.kicad_mod`
- `docs/engineering/rvb22/analyses/i32/procurement_redline/history/native_02/candidate_kicad/libraries/RevB.pretty/TI_DRB0008J_TCAN3403.kicad_mod`
- `docs/engineering/rvb22/analyses/i32/procurement_redline/history/native_02/candidate_kicad/libraries/RevB.pretty/TI_PWP0016A_TPS2660.kicad_mod`
- `docs/engineering/rvb22/analyses/i32/procurement_redline/history/native_02/candidate_kicad/libraries/RevB.pretty/TO-252-2.kicad_mod`
- `docs/engineering/rvb22/analyses/i32/procurement_redline/history/native_02/candidate_kicad/libraries/RevB.pretty/TPS3808_DBV0006A.kicad_mod`
- `docs/engineering/rvb22/analyses/i32/procurement_redline/history/native_02/candidate_kicad/libraries/RevB.pretty/Tag-Connect_TC2030-IDC-NL_2x03_P1.27mm_Vertical.kicad_mod`
- `docs/engineering/rvb22/analyses/i32/procurement_redline/history/native_02/candidate_kicad/libraries/RevB.pretty/TestPoint_Pad_D1.5mm.kicad_mod`
- `docs/engineering/rvb22/analyses/i32/procurement_redline/history/native_02/candidate_kicad/libraries/RevB.pretty/U.FL_Hirose_U.FL-R-SMT-1_Vertical.kicad_mod`
- `docs/engineering/rvb22/analyses/i32/procurement_redline/history/native_02/candidate_kicad/libraries/RevB.pretty/VSSOP-8_2.3x2mm_P0.5mm.kicad_mod`
- `docs/engineering/rvb22/analyses/i32/procurement_redline/history/native_02/candidate_kicad/libraries/RevB.pretty/WSLP0603_MANUFACTURER.kicad_mod`
- `docs/engineering/rvb22/analyses/i32/procurement_redline/history/native_02/candidate_kicad/libraries/RevB.pretty/WSLP0603_MANUFACTURER_R153.kicad_mod`
- `docs/engineering/rvb22/analyses/i32/procurement_redline/history/native_02/candidate_kicad/libraries/RevB.pretty/Wurth_61300211121_1x02.kicad_mod`
- `docs/engineering/rvb22/analyses/i32/procurement_redline/history/native_02/candidate_kicad/models/ENVELOPE_CDTop_PA1616D_20Pad_v06.step`
- `docs/engineering/rvb22/analyses/i32/procurement_redline/history/native_02/candidate_kicad/models/ENVELOPE_C_0603_1608Metric_RVB22_C205.step`
- `docs/engineering/rvb22/analyses/i32/procurement_redline/history/native_02/candidate_kicad/models/ENVELOPE_Coilcraft_MSS1246T_12x12_RVB22_L121.step`
- `docs/engineering/rvb22/analyses/i32/procurement_redline/history/native_02/candidate_kicad/models/ENVELOPE_Fuse_Littelfuse-NANO2-885.step`
- `docs/engineering/rvb22/analyses/i32/procurement_redline/history/native_02/candidate_kicad/models/ENVELOPE_HTSSOP-16-1EP_4.4x5mm_P0.65mm_EP3.4x5mm_Mask2.46x2.31mm_RVB22_U151.step`
- `docs/engineering/rvb22/analyses/i32/procurement_redline/history/native_02/candidate_kicad/models/ENVELOPE_I32_PROCUREMENT_L121.step`
- `docs/engineering/rvb22/analyses/i32/procurement_redline/history/native_02/candidate_kicad/models/ENVELOPE_I32_PROCUREMENT_R155.step`
- `docs/engineering/rvb22/analyses/i32/procurement_redline/history/native_02/candidate_kicad/models/ENVELOPE_I32_PROCUREMENT_R156.step`
- `docs/engineering/rvb22/analyses/i32/procurement_redline/history/native_02/candidate_kicad/models/ENVELOPE_I32_PROCUREMENT_R160.step`
- `docs/engineering/rvb22/analyses/i32/procurement_redline/history/native_02/candidate_kicad/models/ENVELOPE_I32_PROCUREMENT_R161.step`
- `docs/engineering/rvb22/analyses/i32/procurement_redline/history/native_02/candidate_kicad/models/ENVELOPE_I32_PROCUREMENT_R162.step`
- `docs/engineering/rvb22/analyses/i32/procurement_redline/history/native_02/candidate_kicad/models/ENVELOPE_I32_PROCUREMENT_R163.step`
- `docs/engineering/rvb22/analyses/i32/procurement_redline/history/native_02/candidate_kicad/models/ENVELOPE_I32_PROCUREMENT_R169.step`
- `docs/engineering/rvb22/analyses/i32/procurement_redline/history/native_02/candidate_kicad/models/ENVELOPE_I32_PROCUREMENT_R170.step`
- `docs/engineering/rvb22/analyses/i32/procurement_redline/history/native_02/candidate_kicad/models/ENVELOPE_KEMET_C1210_10u50V.step`
- `docs/engineering/rvb22/analyses/i32/procurement_redline/history/native_02/candidate_kicad/models/ENVELOPE_KEMET_T598_X_7343_Median_RVB22_C206.step`
- `docs/engineering/rvb22/analyses/i32/procurement_redline/history/native_02/candidate_kicad/models/ENVELOPE_Molex_Micro-Fit_3.0_43045-1200_2x06_P3.00mm_Horizontal_RVB22_F1.step`
- `docs/engineering/rvb22/analyses/i32/procurement_redline/history/native_02/candidate_kicad/models/ENVELOPE_Murata_LQW18AS_1608.step`
- `docs/engineering/rvb22/analyses/i32/procurement_redline/history/native_02/candidate_kicad/models/ENVELOPE_R_0603_1608Metric_RVB22_R155.step`
- `docs/engineering/rvb22/analyses/i32/procurement_redline/history/native_02/candidate_kicad/models/ENVELOPE_R_0603_1608Metric_RVB22_R156.step`
- `docs/engineering/rvb22/analyses/i32/procurement_redline/history/native_02/candidate_kicad/models/ENVELOPE_R_0603_1608Metric_RVB22_R157.step`
- `docs/engineering/rvb22/analyses/i32/procurement_redline/history/native_02/candidate_kicad/models/ENVELOPE_R_0603_1608Metric_RVB22_R203.step`
- `docs/engineering/rvb22/analyses/i32/procurement_redline/history/native_02/candidate_kicad/models/ENVELOPE_TDK_CGA4J1_33N_I32.step`
- `docs/engineering/rvb22/analyses/i32/procurement_redline/history/native_02/candidate_kicad/models/ENVELOPE_TDK_CGA5L1_68N_I32.step`
- `docs/engineering/rvb22/analyses/i32/procurement_redline/history/native_02/candidate_kicad/models/ENVELOPE_TI_DDA0008B_4214849B.step`
- `docs/engineering/rvb22/analyses/i32/procurement_redline/history/native_02/candidate_kicad/models/ENVELOPE_TI_DPY0002A_TPD1E05U06_SMDMask.step`
- `docs/engineering/rvb22/analyses/i32/procurement_redline/history/native_02/candidate_kicad/models/ENVELOPE_TI_DQC0010A_I32.step`
- `docs/engineering/rvb22/analyses/i32/procurement_redline/history/native_02/candidate_kicad/models/ENVELOPE_TI_DRB0008J_TCAN3403.step`
- `docs/engineering/rvb22/analyses/i32/procurement_redline/history/native_02/candidate_kicad/models/ENVELOPE_TI_PWP0016A_TPS2660.step`
- `docs/engineering/rvb22/analyses/i32/procurement_redline/history/native_02/candidate_kicad/models/ENVELOPE_TPS3808_DBV0006A.step`
- `docs/engineering/rvb22/analyses/i32/procurement_redline/history/native_02/candidate_kicad/models/ENVELOPE_WSL2512_I32_R158.step`
- `docs/engineering/rvb22/analyses/i32/procurement_redline/history/native_02/candidate_kicad/models/ENVELOPE_WSLP0603_MANUFACTURER.step`
- `docs/engineering/rvb22/analyses/i32/procurement_redline/history/native_02/candidate_kicad/models/ENVELOPE_WSLP0603_MANUFACTURER_R153.step`
- `docs/engineering/rvb22/analyses/i32/procurement_redline/history/native_02/candidate_kicad/sym-lib-table`
- `docs/engineering/rvb22/analyses/i32/procurement_redline/history/native_02/logs/component_positions.stderr`
- `docs/engineering/rvb22/analyses/i32/procurement_redline/history/native_02/logs/component_positions.stdout`
- `docs/engineering/rvb22/analyses/i32/procurement_redline/history/native_02/logs/component_step.stderr`
- `docs/engineering/rvb22/analyses/i32/procurement_redline/history/native_02/logs/component_step.stdout`
- `docs/engineering/rvb22/analyses/i32/procurement_redline/history/native_02/logs/drc.stderr`
- `docs/engineering/rvb22/analyses/i32/procurement_redline/history/native_02/logs/drc.stdout`
- `docs/engineering/rvb22/analyses/i32/procurement_redline/history/native_02/logs/drills.stderr`
- `docs/engineering/rvb22/analyses/i32/procurement_redline/history/native_02/logs/drills.stdout`
- `docs/engineering/rvb22/analyses/i32/procurement_redline/history/native_02/logs/erc.stderr`
- `docs/engineering/rvb22/analyses/i32/procurement_redline/history/native_02/logs/erc.stdout`
- `docs/engineering/rvb22/analyses/i32/procurement_redline/history/native_02/logs/gerbers.stderr`
- `docs/engineering/rvb22/analyses/i32/procurement_redline/history/native_02/logs/gerbers.stdout`
- `docs/engineering/rvb22/analyses/i32/procurement_redline/history/native_02/logs/kicad_version.stderr`
- `docs/engineering/rvb22/analyses/i32/procurement_redline/history/native_02/logs/kicad_version.stdout`
- `docs/engineering/rvb22/analyses/i32/procurement_redline/history/native_02/logs/pcb_netlist.stderr`
- `docs/engineering/rvb22/analyses/i32/procurement_redline/history/native_02/logs/pcb_netlist.stdout`
- `docs/engineering/rvb22/analyses/i32/procurement_redline/history/native_02/logs/pcbnew_version.stderr`
- `docs/engineering/rvb22/analyses/i32/procurement_redline/history/native_02/logs/pcbnew_version.stdout`
- `docs/engineering/rvb22/analyses/i32/procurement_redline/history/native_02/logs/schematic_bom.stderr`
- `docs/engineering/rvb22/analyses/i32/procurement_redline/history/native_02/logs/schematic_bom.stdout`
- `docs/engineering/rvb22/analyses/i32/procurement_redline/history/native_02/logs/schematic_netlist.stderr`
- `docs/engineering/rvb22/analyses/i32/procurement_redline/history/native_02/logs/schematic_netlist.stdout`
- `docs/engineering/rvb22/analyses/i32/procurement_redline/history/native_02/logs/schematic_pdf.stderr`
- `docs/engineering/rvb22/analyses/i32/procurement_redline/history/native_02/logs/schematic_pdf.stdout`
- `docs/engineering/rvb22/analyses/i32/procurement_redline/history/native_02/logs/zone_refill.stderr`
- `docs/engineering/rvb22/analyses/i32/procurement_redline/history/native_02/logs/zone_refill.stdout`
- `docs/engineering/rvb22/analyses/i32/procurement_redline/history/native_02/model_export/GR86_CCA_RevB.kicad_pcb`
- `docs/engineering/rvb22/analyses/i32/procurement_redline/history/native_03/COPIED_SOURCE_INVENTORY.json`
- `docs/engineering/rvb22/analyses/i32/procurement_redline/history/native_03/DRC.json`
- `docs/engineering/rvb22/analyses/i32/procurement_redline/history/native_03/ERC.json`
- `docs/engineering/rvb22/analyses/i32/procurement_redline/history/native_03/MODEL_RESOLUTION.json`
- `docs/engineering/rvb22/analyses/i32/procurement_redline/history/native_03/OUTPUT_MANIFEST.json`
- `docs/engineering/rvb22/analyses/i32/procurement_redline/history/native_03/PCB_NETLIST.d356`
- `docs/engineering/rvb22/analyses/i32/procurement_redline/history/native_03/RESULT.json`
- `docs/engineering/rvb22/analyses/i32/procurement_redline/history/native_03/REVIEW_BOM.csv`
- `docs/engineering/rvb22/analyses/i32/procurement_redline/history/native_03/REVIEW_COMPONENTS.step`
- `docs/engineering/rvb22/analyses/i32/procurement_redline/history/native_03/REVIEW_POSITIONS.csv`
- `docs/engineering/rvb22/analyses/i32/procurement_redline/history/native_03/REVIEW_SCHEMATIC.pdf`
- `docs/engineering/rvb22/analyses/i32/procurement_redline/history/native_03/SCHEMATIC_NETLIST.xml`
- `docs/engineering/rvb22/analyses/i32/procurement_redline/history/native_03/candidate_kicad/CAN.kicad_sch`
- `docs/engineering/rvb22/analyses/i32/procurement_redline/history/native_03/candidate_kicad/CANDIDATE_README.md`
- `docs/engineering/rvb22/analyses/i32/procurement_redline/history/native_03/candidate_kicad/ESP32.kicad_sch`
- `docs/engineering/rvb22/analyses/i32/procurement_redline/history/native_03/candidate_kicad/FITTED_REFERENCES.json`
- `docs/engineering/rvb22/analyses/i32/procurement_redline/history/native_03/candidate_kicad/GPS.kicad_sch`
- `docs/engineering/rvb22/analyses/i32/procurement_redline/history/native_03/candidate_kicad/GR86_CCA_RevB.kicad_dru`
- `docs/engineering/rvb22/analyses/i32/procurement_redline/history/native_03/candidate_kicad/GR86_CCA_RevB.kicad_pcb`
- `docs/engineering/rvb22/analyses/i32/procurement_redline/history/native_03/candidate_kicad/GR86_CCA_RevB.kicad_prl`
- `docs/engineering/rvb22/analyses/i32/procurement_redline/history/native_03/candidate_kicad/GR86_CCA_RevB.kicad_pro`
- `docs/engineering/rvb22/analyses/i32/procurement_redline/history/native_03/candidate_kicad/GR86_CCA_RevB.kicad_sch`
- `docs/engineering/rvb22/analyses/i32/procurement_redline/history/native_03/candidate_kicad/Input_Protection.kicad_sch`
- `docs/engineering/rvb22/analyses/i32/procurement_redline/history/native_03/candidate_kicad/LEDs_Status.kicad_sch`
- `docs/engineering/rvb22/analyses/i32/procurement_redline/history/native_03/candidate_kicad/Oil_Pressure.kicad_sch`
- `docs/engineering/rvb22/analyses/i32/procurement_redline/history/native_03/candidate_kicad/Power_3V3.kicad_sch`
- `docs/engineering/rvb22/analyses/i32/procurement_redline/history/native_03/candidate_kicad/Power_5V.kicad_sch`
- `docs/engineering/rvb22/analyses/i32/procurement_redline/history/native_03/candidate_kicad/Programming_Debug.kicad_sch`
- `docs/engineering/rvb22/analyses/i32/procurement_redline/history/native_03/candidate_kicad/RVB22_POWER_CANDIDATE_ONLY.txt`
- `docs/engineering/rvb22/analyses/i32/procurement_redline/history/native_03/candidate_kicad/Test_Points.kicad_sch`
- `docs/engineering/rvb22/analyses/i32/procurement_redline/history/native_03/candidate_kicad/Vehicle_Interconnect.kicad_sch`
- `docs/engineering/rvb22/analyses/i32/procurement_redline/history/native_03/candidate_kicad/fp-lib-table`
- `docs/engineering/rvb22/analyses/i32/procurement_redline/history/native_03/candidate_kicad/libraries/RevB.kicad_sym`
- `docs/engineering/rvb22/analyses/i32/procurement_redline/history/native_03/candidate_kicad/libraries/RevB.pretty/CDTop_PA1616D_20Pad_v06.kicad_mod`
- `docs/engineering/rvb22/analyses/i32/procurement_redline/history/native_03/candidate_kicad/libraries/RevB.pretty/C_0402_1005Metric.kicad_mod`
- `docs/engineering/rvb22/analyses/i32/procurement_redline/history/native_03/candidate_kicad/libraries/RevB.pretty/C_0603_1608Metric.kicad_mod`
- `docs/engineering/rvb22/analyses/i32/procurement_redline/history/native_03/candidate_kicad/libraries/RevB.pretty/C_0603_1608Metric_RVB22_C154.kicad_mod`
- `docs/engineering/rvb22/analyses/i32/procurement_redline/history/native_03/candidate_kicad/libraries/RevB.pretty/C_0603_1608Metric_RVB22_C205.kicad_mod`
- `docs/engineering/rvb22/analyses/i32/procurement_redline/history/native_03/candidate_kicad/libraries/RevB.pretty/C_0805_2012Metric.kicad_mod`
- `docs/engineering/rvb22/analyses/i32/procurement_redline/history/native_03/candidate_kicad/libraries/RevB.pretty/C_1210_3225Metric.kicad_mod`
- `docs/engineering/rvb22/analyses/i32/procurement_redline/history/native_03/candidate_kicad/libraries/RevB.pretty/Coilcraft_MSS1246T_12x12.kicad_mod`
- `docs/engineering/rvb22/analyses/i32/procurement_redline/history/native_03/candidate_kicad/libraries/RevB.pretty/Coilcraft_MSS1246T_12x12_RVB22_L121.kicad_mod`
- `docs/engineering/rvb22/analyses/i32/procurement_redline/history/native_03/candidate_kicad/libraries/RevB.pretty/D_SMA.kicad_mod`
- `docs/engineering/rvb22/analyses/i32/procurement_redline/history/native_03/candidate_kicad/libraries/RevB.pretty/D_SMB.kicad_mod`
- `docs/engineering/rvb22/analyses/i32/procurement_redline/history/native_03/candidate_kicad/libraries/RevB.pretty/D_SMC.kicad_mod`
- `docs/engineering/rvb22/analyses/i32/procurement_redline/history/native_03/candidate_kicad/libraries/RevB.pretty/D_SMC_RVB22_D103.kicad_mod`
- `docs/engineering/rvb22/analyses/i32/procurement_redline/history/native_03/candidate_kicad/libraries/RevB.pretty/D_SOD-123F.kicad_mod`
- `docs/engineering/rvb22/analyses/i32/procurement_redline/history/native_03/candidate_kicad/libraries/RevB.pretty/ESP32-S3-WROOM-1.kicad_mod`
- `docs/engineering/rvb22/analyses/i32/procurement_redline/history/native_03/candidate_kicad/libraries/RevB.pretty/ESP32-S3-WROOM-1_RVB22_U201.kicad_mod`
- `docs/engineering/rvb22/analyses/i32/procurement_redline/history/native_03/candidate_kicad/libraries/RevB.pretty/ESP32-S3-WROOM-1_RVB22_U201_TH48.kicad_mod`
- `docs/engineering/rvb22/analyses/i32/procurement_redline/history/native_03/candidate_kicad/libraries/RevB.pretty/Fuse_Littelfuse-NANO2-885.kicad_mod`
- `docs/engineering/rvb22/analyses/i32/procurement_redline/history/native_03/candidate_kicad/libraries/RevB.pretty/HTSSOP-16-1EP_4.4x5mm_P0.65mm_EP3.4x5mm_Mask2.46x2.31mm.kicad_mod`
- `docs/engineering/rvb22/analyses/i32/procurement_redline/history/native_03/candidate_kicad/libraries/RevB.pretty/HTSSOP-16-1EP_4.4x5mm_P0.65mm_EP3.4x5mm_Mask2.46x2.31mm_RVB22_U151.kicad_mod`
- `docs/engineering/rvb22/analyses/i32/procurement_redline/history/native_03/candidate_kicad/libraries/RevB.pretty/HTSSOP-16-1EP_4.4x5mm_P0.65mm_EP3x3mm.kicad_mod`
- `docs/engineering/rvb22/analyses/i32/procurement_redline/history/native_03/candidate_kicad/libraries/RevB.pretty/Hirose_UFL_R_SMT_1_80_RevB.kicad_mod`
- `docs/engineering/rvb22/analyses/i32/procurement_redline/history/native_03/candidate_kicad/libraries/RevB.pretty/I32_FINISHED_C159.kicad_mod`
- `docs/engineering/rvb22/analyses/i32/procurement_redline/history/native_03/candidate_kicad/libraries/RevB.pretty/I32_FINISHED_C161.kicad_mod`
- `docs/engineering/rvb22/analyses/i32/procurement_redline/history/native_03/candidate_kicad/libraries/RevB.pretty/I32_FINISHED_C162.kicad_mod`
- `docs/engineering/rvb22/analyses/i32/procurement_redline/history/native_03/candidate_kicad/libraries/RevB.pretty/I32_FINISHED_C165.kicad_mod`
- `docs/engineering/rvb22/analyses/i32/procurement_redline/history/native_03/candidate_kicad/libraries/RevB.pretty/I32_FINISHED_C166.kicad_mod`
- `docs/engineering/rvb22/analyses/i32/procurement_redline/history/native_03/candidate_kicad/libraries/RevB.pretty/I32_FINISHED_C167.kicad_mod`
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
- `docs/engineering/rvb22/analyses/i32/procurement_redline/history/native_03/candidate_kicad/libraries/RevB.pretty/I32_PROCUREMENT_R161.kicad_mod`
- `docs/engineering/rvb22/analyses/i32/procurement_redline/history/native_03/candidate_kicad/libraries/RevB.pretty/I32_PROCUREMENT_R162.kicad_mod`
- `docs/engineering/rvb22/analyses/i32/procurement_redline/history/native_03/candidate_kicad/libraries/RevB.pretty/I32_PROCUREMENT_R163.kicad_mod`
- `docs/engineering/rvb22/analyses/i32/procurement_redline/history/native_03/candidate_kicad/libraries/RevB.pretty/I32_PROCUREMENT_R169.kicad_mod`
- `docs/engineering/rvb22/analyses/i32/procurement_redline/history/native_03/candidate_kicad/libraries/RevB.pretty/I32_PROCUREMENT_R170.kicad_mod`
- `docs/engineering/rvb22/analyses/i32/procurement_redline/history/native_03/candidate_kicad/libraries/RevB.pretty/I32_PROCUREMENT_U101.kicad_mod`
- `docs/engineering/rvb22/analyses/i32/procurement_redline/history/native_03/candidate_kicad/libraries/RevB.pretty/KEMET_C1210_10u50V.kicad_mod`
- `docs/engineering/rvb22/analyses/i32/procurement_redline/history/native_03/candidate_kicad/libraries/RevB.pretty/KEMET_T598_X_7343_Median.kicad_mod`
- `docs/engineering/rvb22/analyses/i32/procurement_redline/history/native_03/candidate_kicad/libraries/RevB.pretty/KEMET_T598_X_7343_Median_RVB22_C206.kicad_mod`
- `docs/engineering/rvb22/analyses/i32/procurement_redline/history/native_03/candidate_kicad/libraries/RevB.pretty/LED_0603_1608Metric.kicad_mod`
- `docs/engineering/rvb22/analyses/i32/procurement_redline/history/native_03/candidate_kicad/libraries/RevB.pretty/L_Coilcraft_XAL5030-XXX.kicad_mod`
- `docs/engineering/rvb22/analyses/i32/procurement_redline/history/native_03/candidate_kicad/libraries/RevB.pretty/MSOP-8_3x3mm_P0.65mm.kicad_mod`
- `docs/engineering/rvb22/analyses/i32/procurement_redline/history/native_03/candidate_kicad/libraries/RevB.pretty/Molex_Micro-Fit_3.0_43045-1200_2x06_P3.00mm_Horizontal.kicad_mod`
- `docs/engineering/rvb22/analyses/i32/procurement_redline/history/native_03/candidate_kicad/libraries/RevB.pretty/Molex_Micro-Fit_3.0_43045-1200_2x06_P3.00mm_Horizontal_RVB22_F1.kicad_mod`
- `docs/engineering/rvb22/analyses/i32/procurement_redline/history/native_03/candidate_kicad/libraries/RevB.pretty/MountingHole_4.4mm_Outboard.kicad_mod`
- `docs/engineering/rvb22/analyses/i32/procurement_redline/history/native_03/candidate_kicad/libraries/RevB.pretty/Murata_LQW18AS_1608.kicad_mod`
- `docs/engineering/rvb22/analyses/i32/procurement_redline/history/native_03/candidate_kicad/libraries/RevB.pretty/Nexperia_SOD323_PMEG2010BEA.kicad_mod`
- `docs/engineering/rvb22/analyses/i32/procurement_redline/history/native_03/candidate_kicad/libraries/RevB.pretty/PinHeader_1x02_P2.54mm_Vertical.kicad_mod`
- `docs/engineering/rvb22/analyses/i32/procurement_redline/history/native_03/candidate_kicad/libraries/RevB.pretty/R_0603_1608Metric.kicad_mod`
- `docs/engineering/rvb22/analyses/i32/procurement_redline/history/native_03/candidate_kicad/libraries/RevB.pretty/R_0603_1608Metric_RVB22_R155.kicad_mod`
- `docs/engineering/rvb22/analyses/i32/procurement_redline/history/native_03/candidate_kicad/libraries/RevB.pretty/R_0603_1608Metric_RVB22_R156.kicad_mod`
- `docs/engineering/rvb22/analyses/i32/procurement_redline/history/native_03/candidate_kicad/libraries/RevB.pretty/R_0603_1608Metric_RVB22_R157.kicad_mod`
- `docs/engineering/rvb22/analyses/i32/procurement_redline/history/native_03/candidate_kicad/libraries/RevB.pretty/R_0603_1608Metric_RVB22_R203.kicad_mod`
- `docs/engineering/rvb22/analyses/i32/procurement_redline/history/native_03/candidate_kicad/libraries/RevB.pretty/R_0805_2012Metric.kicad_mod`
- `docs/engineering/rvb22/analyses/i32/procurement_redline/history/native_03/candidate_kicad/libraries/RevB.pretty/R_1206_3216Metric.kicad_mod`
- `docs/engineering/rvb22/analyses/i32/procurement_redline/history/native_03/candidate_kicad/libraries/RevB.pretty/R_2512_6332Metric.kicad_mod`
- `docs/engineering/rvb22/analyses/i32/procurement_redline/history/native_03/candidate_kicad/libraries/RevB.pretty/SOIC-8_3.9x4.9mm_P1.27mm.kicad_mod`
- `docs/engineering/rvb22/analyses/i32/procurement_redline/history/native_03/candidate_kicad/libraries/RevB.pretty/SOT-23-5.kicad_mod`
- `docs/engineering/rvb22/analyses/i32/procurement_redline/history/native_03/candidate_kicad/libraries/RevB.pretty/SOT-23.kicad_mod`
- `docs/engineering/rvb22/analyses/i32/procurement_redline/history/native_03/candidate_kicad/libraries/RevB.pretty/SolderJumper-2_P1.3mm_Open_Pad1.0x1.5mm.kicad_mod`
- `docs/engineering/rvb22/analyses/i32/procurement_redline/history/native_03/candidate_kicad/libraries/RevB.pretty/TDK_CGA4J1_33N_I32.kicad_mod`
- `docs/engineering/rvb22/analyses/i32/procurement_redline/history/native_03/candidate_kicad/libraries/RevB.pretty/TI_DDA0008B_4214849B.kicad_mod`
- `docs/engineering/rvb22/analyses/i32/procurement_redline/history/native_03/candidate_kicad/libraries/RevB.pretty/TI_DPY0002A_TPD1E05U06_SMDMask.kicad_mod`
- `docs/engineering/rvb22/analyses/i32/procurement_redline/history/native_03/candidate_kicad/libraries/RevB.pretty/TI_DQC0010A_I32.kicad_mod`
- `docs/engineering/rvb22/analyses/i32/procurement_redline/history/native_03/candidate_kicad/libraries/RevB.pretty/TI_DRB0008J_TCAN3403.kicad_mod`
- `docs/engineering/rvb22/analyses/i32/procurement_redline/history/native_03/candidate_kicad/libraries/RevB.pretty/TI_PWP0016A_TPS2660.kicad_mod`
- `docs/engineering/rvb22/analyses/i32/procurement_redline/history/native_03/candidate_kicad/libraries/RevB.pretty/TO-252-2.kicad_mod`
- `docs/engineering/rvb22/analyses/i32/procurement_redline/history/native_03/candidate_kicad/libraries/RevB.pretty/TPS3808_DBV0006A.kicad_mod`
- `docs/engineering/rvb22/analyses/i32/procurement_redline/history/native_03/candidate_kicad/libraries/RevB.pretty/Tag-Connect_TC2030-IDC-NL_2x03_P1.27mm_Vertical.kicad_mod`
- `docs/engineering/rvb22/analyses/i32/procurement_redline/history/native_03/candidate_kicad/libraries/RevB.pretty/TestPoint_Pad_D1.5mm.kicad_mod`
- `docs/engineering/rvb22/analyses/i32/procurement_redline/history/native_03/candidate_kicad/libraries/RevB.pretty/U.FL_Hirose_U.FL-R-SMT-1_Vertical.kicad_mod`
- `docs/engineering/rvb22/analyses/i32/procurement_redline/history/native_03/candidate_kicad/libraries/RevB.pretty/VSSOP-8_2.3x2mm_P0.5mm.kicad_mod`
- `docs/engineering/rvb22/analyses/i32/procurement_redline/history/native_03/candidate_kicad/libraries/RevB.pretty/WSLP0603_MANUFACTURER.kicad_mod`
- `docs/engineering/rvb22/analyses/i32/procurement_redline/history/native_03/candidate_kicad/libraries/RevB.pretty/WSLP0603_MANUFACTURER_R153.kicad_mod`
- `docs/engineering/rvb22/analyses/i32/procurement_redline/history/native_03/candidate_kicad/libraries/RevB.pretty/Wurth_61300211121_1x02.kicad_mod`
- `docs/engineering/rvb22/analyses/i32/procurement_redline/history/native_03/candidate_kicad/models/ENVELOPE_CDTop_PA1616D_20Pad_v06.step`
- `docs/engineering/rvb22/analyses/i32/procurement_redline/history/native_03/candidate_kicad/models/ENVELOPE_C_0603_1608Metric_RVB22_C205.step`
- `docs/engineering/rvb22/analyses/i32/procurement_redline/history/native_03/candidate_kicad/models/ENVELOPE_Coilcraft_MSS1246T_12x12_RVB22_L121.step`
- `docs/engineering/rvb22/analyses/i32/procurement_redline/history/native_03/candidate_kicad/models/ENVELOPE_Fuse_Littelfuse-NANO2-885.step`
- `docs/engineering/rvb22/analyses/i32/procurement_redline/history/native_03/candidate_kicad/models/ENVELOPE_HTSSOP-16-1EP_4.4x5mm_P0.65mm_EP3.4x5mm_Mask2.46x2.31mm_RVB22_U151.step`
- `docs/engineering/rvb22/analyses/i32/procurement_redline/history/native_03/candidate_kicad/models/ENVELOPE_I32_PROCUREMENT_L121.step`
- `docs/engineering/rvb22/analyses/i32/procurement_redline/history/native_03/candidate_kicad/models/ENVELOPE_I32_PROCUREMENT_R155.step`
- `docs/engineering/rvb22/analyses/i32/procurement_redline/history/native_03/candidate_kicad/models/ENVELOPE_I32_PROCUREMENT_R156.step`
- `docs/engineering/rvb22/analyses/i32/procurement_redline/history/native_03/candidate_kicad/models/ENVELOPE_I32_PROCUREMENT_R160.step`
- `docs/engineering/rvb22/analyses/i32/procurement_redline/history/native_03/candidate_kicad/models/ENVELOPE_I32_PROCUREMENT_R161.step`
- `docs/engineering/rvb22/analyses/i32/procurement_redline/history/native_03/candidate_kicad/models/ENVELOPE_I32_PROCUREMENT_R162.step`
- `docs/engineering/rvb22/analyses/i32/procurement_redline/history/native_03/candidate_kicad/models/ENVELOPE_I32_PROCUREMENT_R163.step`
- `docs/engineering/rvb22/analyses/i32/procurement_redline/history/native_03/candidate_kicad/models/ENVELOPE_I32_PROCUREMENT_R169.step`
- `docs/engineering/rvb22/analyses/i32/procurement_redline/history/native_03/candidate_kicad/models/ENVELOPE_I32_PROCUREMENT_R170.step`
- `docs/engineering/rvb22/analyses/i32/procurement_redline/history/native_03/candidate_kicad/models/ENVELOPE_KEMET_C1210_10u50V.step`
- `docs/engineering/rvb22/analyses/i32/procurement_redline/history/native_03/candidate_kicad/models/ENVELOPE_KEMET_T598_X_7343_Median_RVB22_C206.step`
- `docs/engineering/rvb22/analyses/i32/procurement_redline/history/native_03/candidate_kicad/models/ENVELOPE_Molex_Micro-Fit_3.0_43045-1200_2x06_P3.00mm_Horizontal_RVB22_F1.step`
- `docs/engineering/rvb22/analyses/i32/procurement_redline/history/native_03/candidate_kicad/models/ENVELOPE_Murata_LQW18AS_1608.step`
- `docs/engineering/rvb22/analyses/i32/procurement_redline/history/native_03/candidate_kicad/models/ENVELOPE_R_0603_1608Metric_RVB22_R155.step`
- `docs/engineering/rvb22/analyses/i32/procurement_redline/history/native_03/candidate_kicad/models/ENVELOPE_R_0603_1608Metric_RVB22_R156.step`
- `docs/engineering/rvb22/analyses/i32/procurement_redline/history/native_03/candidate_kicad/models/ENVELOPE_R_0603_1608Metric_RVB22_R157.step`
- `docs/engineering/rvb22/analyses/i32/procurement_redline/history/native_03/candidate_kicad/models/ENVELOPE_R_0603_1608Metric_RVB22_R203.step`
- `docs/engineering/rvb22/analyses/i32/procurement_redline/history/native_03/candidate_kicad/models/ENVELOPE_TDK_CGA4J1_33N_I32.step`
- `docs/engineering/rvb22/analyses/i32/procurement_redline/history/native_03/candidate_kicad/models/ENVELOPE_TDK_CGA5L1_68N_I32.step`
- `docs/engineering/rvb22/analyses/i32/procurement_redline/history/native_03/candidate_kicad/models/ENVELOPE_TI_DDA0008B_4214849B.step`
- `docs/engineering/rvb22/analyses/i32/procurement_redline/history/native_03/candidate_kicad/models/ENVELOPE_TI_DPY0002A_TPD1E05U06_SMDMask.step`
- `docs/engineering/rvb22/analyses/i32/procurement_redline/history/native_03/candidate_kicad/models/ENVELOPE_TI_DQC0010A_I32.step`
- `docs/engineering/rvb22/analyses/i32/procurement_redline/history/native_03/candidate_kicad/models/ENVELOPE_TI_DRB0008J_TCAN3403.step`
- `docs/engineering/rvb22/analyses/i32/procurement_redline/history/native_03/candidate_kicad/models/ENVELOPE_TI_PWP0016A_TPS2660.step`
- `docs/engineering/rvb22/analyses/i32/procurement_redline/history/native_03/candidate_kicad/models/ENVELOPE_TPS3808_DBV0006A.step`
- `docs/engineering/rvb22/analyses/i32/procurement_redline/history/native_03/candidate_kicad/models/ENVELOPE_WSL2512_I32_R158.step`
- `docs/engineering/rvb22/analyses/i32/procurement_redline/history/native_03/candidate_kicad/models/ENVELOPE_WSLP0603_MANUFACTURER.step`
- `docs/engineering/rvb22/analyses/i32/procurement_redline/history/native_03/candidate_kicad/models/ENVELOPE_WSLP0603_MANUFACTURER_R153.step`
- `docs/engineering/rvb22/analyses/i32/procurement_redline/history/native_03/candidate_kicad/sym-lib-table`
- `docs/engineering/rvb22/analyses/i32/procurement_redline/history/native_03/logs/component_positions.stderr`
- `docs/engineering/rvb22/analyses/i32/procurement_redline/history/native_03/logs/component_positions.stdout`
- `docs/engineering/rvb22/analyses/i32/procurement_redline/history/native_03/logs/component_step.stderr`
- `docs/engineering/rvb22/analyses/i32/procurement_redline/history/native_03/logs/component_step.stdout`
- `docs/engineering/rvb22/analyses/i32/procurement_redline/history/native_03/logs/drc.stderr`
- `docs/engineering/rvb22/analyses/i32/procurement_redline/history/native_03/logs/drc.stdout`
- `docs/engineering/rvb22/analyses/i32/procurement_redline/history/native_03/logs/drills.stderr`
- `docs/engineering/rvb22/analyses/i32/procurement_redline/history/native_03/logs/drills.stdout`
- `docs/engineering/rvb22/analyses/i32/procurement_redline/history/native_03/logs/erc.stderr`
- `docs/engineering/rvb22/analyses/i32/procurement_redline/history/native_03/logs/erc.stdout`
- `docs/engineering/rvb22/analyses/i32/procurement_redline/history/native_03/logs/gerbers.stderr`
- `docs/engineering/rvb22/analyses/i32/procurement_redline/history/native_03/logs/gerbers.stdout`
- `docs/engineering/rvb22/analyses/i32/procurement_redline/history/native_03/logs/kicad_version.stderr`
- `docs/engineering/rvb22/analyses/i32/procurement_redline/history/native_03/logs/kicad_version.stdout`
- `docs/engineering/rvb22/analyses/i32/procurement_redline/history/native_03/logs/pcb_netlist.stderr`
- `docs/engineering/rvb22/analyses/i32/procurement_redline/history/native_03/logs/pcb_netlist.stdout`
- `docs/engineering/rvb22/analyses/i32/procurement_redline/history/native_03/logs/pcbnew_version.stderr`
- `docs/engineering/rvb22/analyses/i32/procurement_redline/history/native_03/logs/pcbnew_version.stdout`
- `docs/engineering/rvb22/analyses/i32/procurement_redline/history/native_03/logs/schematic_bom.stderr`
- `docs/engineering/rvb22/analyses/i32/procurement_redline/history/native_03/logs/schematic_bom.stdout`
- `docs/engineering/rvb22/analyses/i32/procurement_redline/history/native_03/logs/schematic_netlist.stderr`
- `docs/engineering/rvb22/analyses/i32/procurement_redline/history/native_03/logs/schematic_netlist.stdout`
- `docs/engineering/rvb22/analyses/i32/procurement_redline/history/native_03/logs/schematic_pdf.stderr`
- `docs/engineering/rvb22/analyses/i32/procurement_redline/history/native_03/logs/schematic_pdf.stdout`
- `docs/engineering/rvb22/analyses/i32/procurement_redline/history/native_03/logs/zone_refill.stderr`
- `docs/engineering/rvb22/analyses/i32/procurement_redline/history/native_03/logs/zone_refill.stdout`
- `docs/engineering/rvb22/analyses/i32/procurement_redline/history/native_03/model_export/GR86_CCA_RevB.kicad_pcb`
- `docs/engineering/rvb22/analyses/i32/procurement_redline/history/native_03/review_gerbers/GR86_CCA_RevB-B_Cu.gbl`
- `docs/engineering/rvb22/analyses/i32/procurement_redline/history/native_03/review_gerbers/GR86_CCA_RevB-B_Mask.gbs`
- `docs/engineering/rvb22/analyses/i32/procurement_redline/history/native_03/review_gerbers/GR86_CCA_RevB-B_Paste.gbp`
- `docs/engineering/rvb22/analyses/i32/procurement_redline/history/native_03/review_gerbers/GR86_CCA_RevB-B_Silkscreen.gbo`
- `docs/engineering/rvb22/analyses/i32/procurement_redline/history/native_03/review_gerbers/GR86_CCA_RevB-Edge_Cuts.gm1`
- `docs/engineering/rvb22/analyses/i32/procurement_redline/history/native_03/review_gerbers/GR86_CCA_RevB-F_Cu.gtl`
- `docs/engineering/rvb22/analyses/i32/procurement_redline/history/native_03/review_gerbers/GR86_CCA_RevB-F_Mask.gts`
- `docs/engineering/rvb22/analyses/i32/procurement_redline/history/native_03/review_gerbers/GR86_CCA_RevB-F_Paste.gtp`
- `docs/engineering/rvb22/analyses/i32/procurement_redline/history/native_03/review_gerbers/GR86_CCA_RevB-F_Silkscreen.gto`
- `docs/engineering/rvb22/analyses/i32/procurement_redline/history/native_03/review_gerbers/GR86_CCA_RevB-In1_Cu.g1`
- `docs/engineering/rvb22/analyses/i32/procurement_redline/history/native_03/review_gerbers/GR86_CCA_RevB-In2_Cu.g2`
- `docs/engineering/rvb22/analyses/i32/procurement_redline/history/native_03/review_gerbers/GR86_CCA_RevB-NPTH.drl`
- `docs/engineering/rvb22/analyses/i32/procurement_redline/history/native_03/review_gerbers/GR86_CCA_RevB-PTH.drl`
- `docs/engineering/rvb22/analyses/i32/procurement_redline/history/native_03/review_gerbers/GR86_CCA_RevB-job.gbrjob`
- `docs/engineering/rvb22/analyses/i32/procurement_redline/history/native_04/COPIED_SOURCE_INVENTORY.json`
- `docs/engineering/rvb22/analyses/i32/procurement_redline/history/native_04/DRC.json`
- `docs/engineering/rvb22/analyses/i32/procurement_redline/history/native_04/ERC.json`
- `docs/engineering/rvb22/analyses/i32/procurement_redline/history/native_04/MODEL_RESOLUTION.json`
- `docs/engineering/rvb22/analyses/i32/procurement_redline/history/native_04/OUTPUT_MANIFEST.json`
- `docs/engineering/rvb22/analyses/i32/procurement_redline/history/native_04/PCB_NETLIST.d356`
- `docs/engineering/rvb22/analyses/i32/procurement_redline/history/native_04/RESULT.json`
- `docs/engineering/rvb22/analyses/i32/procurement_redline/history/native_04/REVIEW_BOM.csv`
- `docs/engineering/rvb22/analyses/i32/procurement_redline/history/native_04/REVIEW_COMPONENTS.step`
- `docs/engineering/rvb22/analyses/i32/procurement_redline/history/native_04/REVIEW_POSITIONS.csv`
- `docs/engineering/rvb22/analyses/i32/procurement_redline/history/native_04/REVIEW_SCHEMATIC.pdf`
- `docs/engineering/rvb22/analyses/i32/procurement_redline/history/native_04/SCHEMATIC_NETLIST.xml`
- `docs/engineering/rvb22/analyses/i32/procurement_redline/history/native_04/candidate_kicad/CAN.kicad_sch`
- `docs/engineering/rvb22/analyses/i32/procurement_redline/history/native_04/candidate_kicad/CANDIDATE_README.md`
- `docs/engineering/rvb22/analyses/i32/procurement_redline/history/native_04/candidate_kicad/ESP32.kicad_sch`
- `docs/engineering/rvb22/analyses/i32/procurement_redline/history/native_04/candidate_kicad/FITTED_REFERENCES.json`
- `docs/engineering/rvb22/analyses/i32/procurement_redline/history/native_04/candidate_kicad/GPS.kicad_sch`
- `docs/engineering/rvb22/analyses/i32/procurement_redline/history/native_04/candidate_kicad/GR86_CCA_RevB.kicad_dru`
- `docs/engineering/rvb22/analyses/i32/procurement_redline/history/native_04/candidate_kicad/GR86_CCA_RevB.kicad_pcb`
- `docs/engineering/rvb22/analyses/i32/procurement_redline/history/native_04/candidate_kicad/GR86_CCA_RevB.kicad_prl`
- `docs/engineering/rvb22/analyses/i32/procurement_redline/history/native_04/candidate_kicad/GR86_CCA_RevB.kicad_pro`
- `docs/engineering/rvb22/analyses/i32/procurement_redline/history/native_04/candidate_kicad/GR86_CCA_RevB.kicad_sch`
- `docs/engineering/rvb22/analyses/i32/procurement_redline/history/native_04/candidate_kicad/Input_Protection.kicad_sch`
- `docs/engineering/rvb22/analyses/i32/procurement_redline/history/native_04/candidate_kicad/LEDs_Status.kicad_sch`
- `docs/engineering/rvb22/analyses/i32/procurement_redline/history/native_04/candidate_kicad/Oil_Pressure.kicad_sch`
- `docs/engineering/rvb22/analyses/i32/procurement_redline/history/native_04/candidate_kicad/Power_3V3.kicad_sch`
- `docs/engineering/rvb22/analyses/i32/procurement_redline/history/native_04/candidate_kicad/Power_5V.kicad_sch`
- `docs/engineering/rvb22/analyses/i32/procurement_redline/history/native_04/candidate_kicad/Programming_Debug.kicad_sch`
- `docs/engineering/rvb22/analyses/i32/procurement_redline/history/native_04/candidate_kicad/RVB22_POWER_CANDIDATE_ONLY.txt`
- `docs/engineering/rvb22/analyses/i32/procurement_redline/history/native_04/candidate_kicad/Test_Points.kicad_sch`
- `docs/engineering/rvb22/analyses/i32/procurement_redline/history/native_04/candidate_kicad/Vehicle_Interconnect.kicad_sch`
- `docs/engineering/rvb22/analyses/i32/procurement_redline/history/native_04/candidate_kicad/fp-lib-table`
- `docs/engineering/rvb22/analyses/i32/procurement_redline/history/native_04/candidate_kicad/libraries/RevB.kicad_sym`
- `docs/engineering/rvb22/analyses/i32/procurement_redline/history/native_04/candidate_kicad/libraries/RevB.pretty/CDTop_PA1616D_20Pad_v06.kicad_mod`
- `docs/engineering/rvb22/analyses/i32/procurement_redline/history/native_04/candidate_kicad/libraries/RevB.pretty/C_0402_1005Metric.kicad_mod`
- `docs/engineering/rvb22/analyses/i32/procurement_redline/history/native_04/candidate_kicad/libraries/RevB.pretty/C_0603_1608Metric.kicad_mod`
- `docs/engineering/rvb22/analyses/i32/procurement_redline/history/native_04/candidate_kicad/libraries/RevB.pretty/C_0603_1608Metric_RVB22_C154.kicad_mod`
- `docs/engineering/rvb22/analyses/i32/procurement_redline/history/native_04/candidate_kicad/libraries/RevB.pretty/C_0603_1608Metric_RVB22_C205.kicad_mod`
- `docs/engineering/rvb22/analyses/i32/procurement_redline/history/native_04/candidate_kicad/libraries/RevB.pretty/C_0805_2012Metric.kicad_mod`
- `docs/engineering/rvb22/analyses/i32/procurement_redline/history/native_04/candidate_kicad/libraries/RevB.pretty/C_1210_3225Metric.kicad_mod`
- `docs/engineering/rvb22/analyses/i32/procurement_redline/history/native_04/candidate_kicad/libraries/RevB.pretty/Coilcraft_MSS1246T_12x12.kicad_mod`
- `docs/engineering/rvb22/analyses/i32/procurement_redline/history/native_04/candidate_kicad/libraries/RevB.pretty/Coilcraft_MSS1246T_12x12_RVB22_L121.kicad_mod`
- `docs/engineering/rvb22/analyses/i32/procurement_redline/history/native_04/candidate_kicad/libraries/RevB.pretty/D_SMA.kicad_mod`
- `docs/engineering/rvb22/analyses/i32/procurement_redline/history/native_04/candidate_kicad/libraries/RevB.pretty/D_SMB.kicad_mod`
- `docs/engineering/rvb22/analyses/i32/procurement_redline/history/native_04/candidate_kicad/libraries/RevB.pretty/D_SMC.kicad_mod`
- `docs/engineering/rvb22/analyses/i32/procurement_redline/history/native_04/candidate_kicad/libraries/RevB.pretty/D_SMC_RVB22_D103.kicad_mod`
- `docs/engineering/rvb22/analyses/i32/procurement_redline/history/native_04/candidate_kicad/libraries/RevB.pretty/D_SOD-123F.kicad_mod`
- `docs/engineering/rvb22/analyses/i32/procurement_redline/history/native_04/candidate_kicad/libraries/RevB.pretty/ESP32-S3-WROOM-1.kicad_mod`
- `docs/engineering/rvb22/analyses/i32/procurement_redline/history/native_04/candidate_kicad/libraries/RevB.pretty/ESP32-S3-WROOM-1_RVB22_U201.kicad_mod`
- `docs/engineering/rvb22/analyses/i32/procurement_redline/history/native_04/candidate_kicad/libraries/RevB.pretty/ESP32-S3-WROOM-1_RVB22_U201_TH48.kicad_mod`
- `docs/engineering/rvb22/analyses/i32/procurement_redline/history/native_04/candidate_kicad/libraries/RevB.pretty/Fuse_Littelfuse-NANO2-885.kicad_mod`
- `docs/engineering/rvb22/analyses/i32/procurement_redline/history/native_04/candidate_kicad/libraries/RevB.pretty/HTSSOP-16-1EP_4.4x5mm_P0.65mm_EP3.4x5mm_Mask2.46x2.31mm.kicad_mod`
- `docs/engineering/rvb22/analyses/i32/procurement_redline/history/native_04/candidate_kicad/libraries/RevB.pretty/HTSSOP-16-1EP_4.4x5mm_P0.65mm_EP3.4x5mm_Mask2.46x2.31mm_RVB22_U151.kicad_mod`
- `docs/engineering/rvb22/analyses/i32/procurement_redline/history/native_04/candidate_kicad/libraries/RevB.pretty/HTSSOP-16-1EP_4.4x5mm_P0.65mm_EP3x3mm.kicad_mod`
- `docs/engineering/rvb22/analyses/i32/procurement_redline/history/native_04/candidate_kicad/libraries/RevB.pretty/Hirose_UFL_R_SMT_1_80_RevB.kicad_mod`
- `docs/engineering/rvb22/analyses/i32/procurement_redline/history/native_04/candidate_kicad/libraries/RevB.pretty/I32_FINISHED_C159.kicad_mod`
- `docs/engineering/rvb22/analyses/i32/procurement_redline/history/native_04/candidate_kicad/libraries/RevB.pretty/I32_FINISHED_C161.kicad_mod`
- `docs/engineering/rvb22/analyses/i32/procurement_redline/history/native_04/candidate_kicad/libraries/RevB.pretty/I32_FINISHED_C162.kicad_mod`
- `docs/engineering/rvb22/analyses/i32/procurement_redline/history/native_04/candidate_kicad/libraries/RevB.pretty/I32_FINISHED_C165.kicad_mod`
- `docs/engineering/rvb22/analyses/i32/procurement_redline/history/native_04/candidate_kicad/libraries/RevB.pretty/I32_FINISHED_C166.kicad_mod`
- `docs/engineering/rvb22/analyses/i32/procurement_redline/history/native_04/candidate_kicad/libraries/RevB.pretty/I32_FINISHED_C167.kicad_mod`
- `docs/engineering/rvb22/analyses/i32/procurement_redline/history/native_04/candidate_kicad/libraries/RevB.pretty/I32_FINISHED_Q152.kicad_mod`
- `docs/engineering/rvb22/analyses/i32/procurement_redline/history/native_04/candidate_kicad/libraries/RevB.pretty/I32_FINISHED_Q153.kicad_mod`
- `docs/engineering/rvb22/analyses/i32/procurement_redline/history/native_04/candidate_kicad/libraries/RevB.pretty/I32_FINISHED_R151.kicad_mod`
- `docs/engineering/rvb22/analyses/i32/procurement_redline/history/native_04/candidate_kicad/libraries/RevB.pretty/I32_FINISHED_R155.kicad_mod`
- `docs/engineering/rvb22/analyses/i32/procurement_redline/history/native_04/candidate_kicad/libraries/RevB.pretty/I32_FINISHED_R156.kicad_mod`
- `docs/engineering/rvb22/analyses/i32/procurement_redline/history/native_04/candidate_kicad/libraries/RevB.pretty/I32_FINISHED_R158.kicad_mod`
- `docs/engineering/rvb22/analyses/i32/procurement_redline/history/native_04/candidate_kicad/libraries/RevB.pretty/I32_FINISHED_R159.kicad_mod`
- `docs/engineering/rvb22/analyses/i32/procurement_redline/history/native_04/candidate_kicad/libraries/RevB.pretty/I32_FINISHED_R160.kicad_mod`
- `docs/engineering/rvb22/analyses/i32/procurement_redline/history/native_04/candidate_kicad/libraries/RevB.pretty/I32_FINISHED_R161.kicad_mod`
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
- `docs/engineering/rvb22/analyses/i32/procurement_redline/history/native_04/candidate_kicad/libraries/RevB.pretty/LED_0603_1608Metric.kicad_mod`
- `docs/engineering/rvb22/analyses/i32/procurement_redline/history/native_04/candidate_kicad/libraries/RevB.pretty/L_Coilcraft_XAL5030-XXX.kicad_mod`
- `docs/engineering/rvb22/analyses/i32/procurement_redline/history/native_04/candidate_kicad/libraries/RevB.pretty/MSOP-8_3x3mm_P0.65mm.kicad_mod`
- `docs/engineering/rvb22/analyses/i32/procurement_redline/history/native_04/candidate_kicad/libraries/RevB.pretty/Molex_Micro-Fit_3.0_43045-1200_2x06_P3.00mm_Horizontal.kicad_mod`
- `docs/engineering/rvb22/analyses/i32/procurement_redline/history/native_04/candidate_kicad/libraries/RevB.pretty/Molex_Micro-Fit_3.0_43045-1200_2x06_P3.00mm_Horizontal_RVB22_F1.kicad_mod`
- `docs/engineering/rvb22/analyses/i32/procurement_redline/history/native_04/candidate_kicad/libraries/RevB.pretty/MountingHole_4.4mm_Outboard.kicad_mod`
- `docs/engineering/rvb22/analyses/i32/procurement_redline/history/native_04/candidate_kicad/libraries/RevB.pretty/Murata_LQW18AS_1608.kicad_mod`
- `docs/engineering/rvb22/analyses/i32/procurement_redline/history/native_04/candidate_kicad/libraries/RevB.pretty/Nexperia_SOD323_PMEG2010BEA.kicad_mod`
- `docs/engineering/rvb22/analyses/i32/procurement_redline/history/native_04/candidate_kicad/libraries/RevB.pretty/PinHeader_1x02_P2.54mm_Vertical.kicad_mod`
- `docs/engineering/rvb22/analyses/i32/procurement_redline/history/native_04/candidate_kicad/libraries/RevB.pretty/R_0603_1608Metric.kicad_mod`
- `docs/engineering/rvb22/analyses/i32/procurement_redline/history/native_04/candidate_kicad/libraries/RevB.pretty/R_0603_1608Metric_RVB22_R155.kicad_mod`
- `docs/engineering/rvb22/analyses/i32/procurement_redline/history/native_04/candidate_kicad/libraries/RevB.pretty/R_0603_1608Metric_RVB22_R156.kicad_mod`
- `docs/engineering/rvb22/analyses/i32/procurement_redline/history/native_04/candidate_kicad/libraries/RevB.pretty/R_0603_1608Metric_RVB22_R157.kicad_mod`
- `docs/engineering/rvb22/analyses/i32/procurement_redline/history/native_04/candidate_kicad/libraries/RevB.pretty/R_0603_1608Metric_RVB22_R203.kicad_mod`
- `docs/engineering/rvb22/analyses/i32/procurement_redline/history/native_04/candidate_kicad/libraries/RevB.pretty/R_0805_2012Metric.kicad_mod`
- `docs/engineering/rvb22/analyses/i32/procurement_redline/history/native_04/candidate_kicad/libraries/RevB.pretty/R_1206_3216Metric.kicad_mod`
- `docs/engineering/rvb22/analyses/i32/procurement_redline/history/native_04/candidate_kicad/libraries/RevB.pretty/R_2512_6332Metric.kicad_mod`
- `docs/engineering/rvb22/analyses/i32/procurement_redline/history/native_04/candidate_kicad/libraries/RevB.pretty/SOIC-8_3.9x4.9mm_P1.27mm.kicad_mod`
- `docs/engineering/rvb22/analyses/i32/procurement_redline/history/native_04/candidate_kicad/libraries/RevB.pretty/SOT-23-5.kicad_mod`
- `docs/engineering/rvb22/analyses/i32/procurement_redline/history/native_04/candidate_kicad/libraries/RevB.pretty/SOT-23.kicad_mod`
- `docs/engineering/rvb22/analyses/i32/procurement_redline/history/native_04/candidate_kicad/libraries/RevB.pretty/SolderJumper-2_P1.3mm_Open_Pad1.0x1.5mm.kicad_mod`
- `docs/engineering/rvb22/analyses/i32/procurement_redline/history/native_04/candidate_kicad/libraries/RevB.pretty/TDK_CGA4J1_33N_I32.kicad_mod`
- `docs/engineering/rvb22/analyses/i32/procurement_redline/history/native_04/candidate_kicad/libraries/RevB.pretty/TI_DDA0008B_4214849B.kicad_mod`
- `docs/engineering/rvb22/analyses/i32/procurement_redline/history/native_04/candidate_kicad/libraries/RevB.pretty/TI_DPY0002A_TPD1E05U06_SMDMask.kicad_mod`
- `docs/engineering/rvb22/analyses/i32/procurement_redline/history/native_04/candidate_kicad/libraries/RevB.pretty/TI_DQC0010A_I32.kicad_mod`
- `docs/engineering/rvb22/analyses/i32/procurement_redline/history/native_04/candidate_kicad/libraries/RevB.pretty/TI_DRB0008J_TCAN3403.kicad_mod`
- `docs/engineering/rvb22/analyses/i32/procurement_redline/history/native_04/candidate_kicad/libraries/RevB.pretty/TI_PWP0016A_TPS2660.kicad_mod`
- `docs/engineering/rvb22/analyses/i32/procurement_redline/history/native_04/candidate_kicad/libraries/RevB.pretty/TO-252-2.kicad_mod`
- `docs/engineering/rvb22/analyses/i32/procurement_redline/history/native_04/candidate_kicad/libraries/RevB.pretty/TPS3808_DBV0006A.kicad_mod`
- `docs/engineering/rvb22/analyses/i32/procurement_redline/history/native_04/candidate_kicad/libraries/RevB.pretty/Tag-Connect_TC2030-IDC-NL_2x03_P1.27mm_Vertical.kicad_mod`
- `docs/engineering/rvb22/analyses/i32/procurement_redline/history/native_04/candidate_kicad/libraries/RevB.pretty/TestPoint_Pad_D1.5mm.kicad_mod`
- `docs/engineering/rvb22/analyses/i32/procurement_redline/history/native_04/candidate_kicad/libraries/RevB.pretty/U.FL_Hirose_U.FL-R-SMT-1_Vertical.kicad_mod`
- `docs/engineering/rvb22/analyses/i32/procurement_redline/history/native_04/candidate_kicad/libraries/RevB.pretty/VSSOP-8_2.3x2mm_P0.5mm.kicad_mod`
- `docs/engineering/rvb22/analyses/i32/procurement_redline/history/native_04/candidate_kicad/libraries/RevB.pretty/WSLP0603_MANUFACTURER.kicad_mod`
- `docs/engineering/rvb22/analyses/i32/procurement_redline/history/native_04/candidate_kicad/libraries/RevB.pretty/WSLP0603_MANUFACTURER_R153.kicad_mod`
- `docs/engineering/rvb22/analyses/i32/procurement_redline/history/native_04/candidate_kicad/libraries/RevB.pretty/Wurth_61300211121_1x02.kicad_mod`
- `docs/engineering/rvb22/analyses/i32/procurement_redline/history/native_04/candidate_kicad/models/ENVELOPE_CDTop_PA1616D_20Pad_v06.step`
- `docs/engineering/rvb22/analyses/i32/procurement_redline/history/native_04/candidate_kicad/models/ENVELOPE_C_0603_1608Metric_RVB22_C205.step`
- `docs/engineering/rvb22/analyses/i32/procurement_redline/history/native_04/candidate_kicad/models/ENVELOPE_Coilcraft_MSS1246T_12x12_RVB22_L121.step`
- `docs/engineering/rvb22/analyses/i32/procurement_redline/history/native_04/candidate_kicad/models/ENVELOPE_Fuse_Littelfuse-NANO2-885.step`
- `docs/engineering/rvb22/analyses/i32/procurement_redline/history/native_04/candidate_kicad/models/ENVELOPE_HTSSOP-16-1EP_4.4x5mm_P0.65mm_EP3.4x5mm_Mask2.46x2.31mm_RVB22_U151.step`
- `docs/engineering/rvb22/analyses/i32/procurement_redline/history/native_04/candidate_kicad/models/ENVELOPE_I32_PROCUREMENT_L121.step`
- `docs/engineering/rvb22/analyses/i32/procurement_redline/history/native_04/candidate_kicad/models/ENVELOPE_I32_PROCUREMENT_R155.step`
- `docs/engineering/rvb22/analyses/i32/procurement_redline/history/native_04/candidate_kicad/models/ENVELOPE_I32_PROCUREMENT_R156.step`
- `docs/engineering/rvb22/analyses/i32/procurement_redline/history/native_04/candidate_kicad/models/ENVELOPE_I32_PROCUREMENT_R160.step`
- `docs/engineering/rvb22/analyses/i32/procurement_redline/history/native_04/candidate_kicad/models/ENVELOPE_I32_PROCUREMENT_R161.step`
- `docs/engineering/rvb22/analyses/i32/procurement_redline/history/native_04/candidate_kicad/models/ENVELOPE_I32_PROCUREMENT_R162.step`
- `docs/engineering/rvb22/analyses/i32/procurement_redline/history/native_04/candidate_kicad/models/ENVELOPE_I32_PROCUREMENT_R163.step`
- `docs/engineering/rvb22/analyses/i32/procurement_redline/history/native_04/candidate_kicad/models/ENVELOPE_I32_PROCUREMENT_R169.step`
- `docs/engineering/rvb22/analyses/i32/procurement_redline/history/native_04/candidate_kicad/models/ENVELOPE_I32_PROCUREMENT_R170.step`
- `docs/engineering/rvb22/analyses/i32/procurement_redline/history/native_04/candidate_kicad/models/ENVELOPE_KEMET_C1210_10u50V.step`
- `docs/engineering/rvb22/analyses/i32/procurement_redline/history/native_04/candidate_kicad/models/ENVELOPE_KEMET_T598_X_7343_Median_RVB22_C206.step`
- `docs/engineering/rvb22/analyses/i32/procurement_redline/history/native_04/candidate_kicad/models/ENVELOPE_Molex_Micro-Fit_3.0_43045-1200_2x06_P3.00mm_Horizontal_RVB22_F1.step`
- `docs/engineering/rvb22/analyses/i32/procurement_redline/history/native_04/candidate_kicad/models/ENVELOPE_Murata_LQW18AS_1608.step`
- `docs/engineering/rvb22/analyses/i32/procurement_redline/history/native_04/candidate_kicad/models/ENVELOPE_R_0603_1608Metric_RVB22_R155.step`
- `docs/engineering/rvb22/analyses/i32/procurement_redline/history/native_04/candidate_kicad/models/ENVELOPE_R_0603_1608Metric_RVB22_R156.step`
- `docs/engineering/rvb22/analyses/i32/procurement_redline/history/native_04/candidate_kicad/models/ENVELOPE_R_0603_1608Metric_RVB22_R157.step`
- `docs/engineering/rvb22/analyses/i32/procurement_redline/history/native_04/candidate_kicad/models/ENVELOPE_R_0603_1608Metric_RVB22_R203.step`
- `docs/engineering/rvb22/analyses/i32/procurement_redline/history/native_04/candidate_kicad/models/ENVELOPE_TDK_CGA4J1_33N_I32.step`
- `docs/engineering/rvb22/analyses/i32/procurement_redline/history/native_04/candidate_kicad/models/ENVELOPE_TDK_CGA5L1_68N_I32.step`
- `docs/engineering/rvb22/analyses/i32/procurement_redline/history/native_04/candidate_kicad/models/ENVELOPE_TI_DDA0008B_4214849B.step`
- `docs/engineering/rvb22/analyses/i32/procurement_redline/history/native_04/candidate_kicad/models/ENVELOPE_TI_DPY0002A_TPD1E05U06_SMDMask.step`
- `docs/engineering/rvb22/analyses/i32/procurement_redline/history/native_04/candidate_kicad/models/ENVELOPE_TI_DQC0010A_I32.step`
- `docs/engineering/rvb22/analyses/i32/procurement_redline/history/native_04/candidate_kicad/models/ENVELOPE_TI_DRB0008J_TCAN3403.step`
- `docs/engineering/rvb22/analyses/i32/procurement_redline/history/native_04/candidate_kicad/models/ENVELOPE_TI_PWP0016A_TPS2660.step`
- `docs/engineering/rvb22/analyses/i32/procurement_redline/history/native_04/candidate_kicad/models/ENVELOPE_TPS3808_DBV0006A.step`
- `docs/engineering/rvb22/analyses/i32/procurement_redline/history/native_04/candidate_kicad/models/ENVELOPE_WSL2512_I32_R158.step`
- `docs/engineering/rvb22/analyses/i32/procurement_redline/history/native_04/candidate_kicad/models/ENVELOPE_WSLP0603_MANUFACTURER.step`
- `docs/engineering/rvb22/analyses/i32/procurement_redline/history/native_04/candidate_kicad/models/ENVELOPE_WSLP0603_MANUFACTURER_R153.step`
- `docs/engineering/rvb22/analyses/i32/procurement_redline/history/native_04/candidate_kicad/sym-lib-table`
- `docs/engineering/rvb22/analyses/i32/procurement_redline/history/native_04/logs/component_positions.stderr`
- `docs/engineering/rvb22/analyses/i32/procurement_redline/history/native_04/logs/component_positions.stdout`
- `docs/engineering/rvb22/analyses/i32/procurement_redline/history/native_04/logs/component_step.stderr`
- `docs/engineering/rvb22/analyses/i32/procurement_redline/history/native_04/logs/component_step.stdout`
- `docs/engineering/rvb22/analyses/i32/procurement_redline/history/native_04/logs/drc.stderr`
- `docs/engineering/rvb22/analyses/i32/procurement_redline/history/native_04/logs/drc.stdout`
- `docs/engineering/rvb22/analyses/i32/procurement_redline/history/native_04/logs/drills.stderr`
- `docs/engineering/rvb22/analyses/i32/procurement_redline/history/native_04/logs/drills.stdout`
- `docs/engineering/rvb22/analyses/i32/procurement_redline/history/native_04/logs/erc.stderr`
- `docs/engineering/rvb22/analyses/i32/procurement_redline/history/native_04/logs/erc.stdout`
- `docs/engineering/rvb22/analyses/i32/procurement_redline/history/native_04/logs/gerbers.stderr`
- `docs/engineering/rvb22/analyses/i32/procurement_redline/history/native_04/logs/gerbers.stdout`
- `docs/engineering/rvb22/analyses/i32/procurement_redline/history/native_04/logs/kicad_version.stderr`
- `docs/engineering/rvb22/analyses/i32/procurement_redline/history/native_04/logs/kicad_version.stdout`
- `docs/engineering/rvb22/analyses/i32/procurement_redline/history/native_04/logs/pcb_netlist.stderr`
- `docs/engineering/rvb22/analyses/i32/procurement_redline/history/native_04/logs/pcb_netlist.stdout`
- `docs/engineering/rvb22/analyses/i32/procurement_redline/history/native_04/logs/pcbnew_version.stderr`
- `docs/engineering/rvb22/analyses/i32/procurement_redline/history/native_04/logs/pcbnew_version.stdout`
- `docs/engineering/rvb22/analyses/i32/procurement_redline/history/native_04/logs/schematic_bom.stderr`
- `docs/engineering/rvb22/analyses/i32/procurement_redline/history/native_04/logs/schematic_bom.stdout`
- `docs/engineering/rvb22/analyses/i32/procurement_redline/history/native_04/logs/schematic_netlist.stderr`
- `docs/engineering/rvb22/analyses/i32/procurement_redline/history/native_04/logs/schematic_netlist.stdout`
- `docs/engineering/rvb22/analyses/i32/procurement_redline/history/native_04/logs/schematic_pdf.stderr`
- `docs/engineering/rvb22/analyses/i32/procurement_redline/history/native_04/logs/schematic_pdf.stdout`
- `docs/engineering/rvb22/analyses/i32/procurement_redline/history/native_04/logs/zone_refill.stderr`
- `docs/engineering/rvb22/analyses/i32/procurement_redline/history/native_04/logs/zone_refill.stdout`
- `docs/engineering/rvb22/analyses/i32/procurement_redline/history/native_04/model_export/GR86_CCA_RevB.kicad_pcb`
- `docs/engineering/rvb22/analyses/i32/procurement_redline/history/native_04/review_gerbers/GR86_CCA_RevB-B_Cu.gbl`
- `docs/engineering/rvb22/analyses/i32/procurement_redline/history/native_04/review_gerbers/GR86_CCA_RevB-B_Mask.gbs`
- `docs/engineering/rvb22/analyses/i32/procurement_redline/history/native_04/review_gerbers/GR86_CCA_RevB-B_Paste.gbp`
- `docs/engineering/rvb22/analyses/i32/procurement_redline/history/native_04/review_gerbers/GR86_CCA_RevB-B_Silkscreen.gbo`
- `docs/engineering/rvb22/analyses/i32/procurement_redline/history/native_04/review_gerbers/GR86_CCA_RevB-Edge_Cuts.gm1`
- `docs/engineering/rvb22/analyses/i32/procurement_redline/history/native_04/review_gerbers/GR86_CCA_RevB-F_Cu.gtl`
- `docs/engineering/rvb22/analyses/i32/procurement_redline/history/native_04/review_gerbers/GR86_CCA_RevB-F_Mask.gts`
- `docs/engineering/rvb22/analyses/i32/procurement_redline/history/native_04/review_gerbers/GR86_CCA_RevB-F_Paste.gtp`
- `docs/engineering/rvb22/analyses/i32/procurement_redline/history/native_04/review_gerbers/GR86_CCA_RevB-F_Silkscreen.gto`
- `docs/engineering/rvb22/analyses/i32/procurement_redline/history/native_04/review_gerbers/GR86_CCA_RevB-In1_Cu.g1`
- `docs/engineering/rvb22/analyses/i32/procurement_redline/history/native_04/review_gerbers/GR86_CCA_RevB-In2_Cu.g2`
- `docs/engineering/rvb22/analyses/i32/procurement_redline/history/native_04/review_gerbers/GR86_CCA_RevB-NPTH.drl`
- `docs/engineering/rvb22/analyses/i32/procurement_redline/history/native_04/review_gerbers/GR86_CCA_RevB-PTH.drl`
- `docs/engineering/rvb22/analyses/i32/procurement_redline/history/native_04/review_gerbers/GR86_CCA_RevB-job.gbrjob`
- `docs/engineering/rvb22/analyses/i32/procurement_redline/history/native_05/COPIED_SOURCE_INVENTORY.json`
- `docs/engineering/rvb22/analyses/i32/procurement_redline/history/native_05/DRC.json`
- `docs/engineering/rvb22/analyses/i32/procurement_redline/history/native_05/ERC.json`
- `docs/engineering/rvb22/analyses/i32/procurement_redline/history/native_05/MODEL_RESOLUTION.json`
- `docs/engineering/rvb22/analyses/i32/procurement_redline/history/native_05/OUTPUT_MANIFEST.json`
- `docs/engineering/rvb22/analyses/i32/procurement_redline/history/native_05/PCB_NETLIST.d356`
- `docs/engineering/rvb22/analyses/i32/procurement_redline/history/native_05/RESULT.json`
- `docs/engineering/rvb22/analyses/i32/procurement_redline/history/native_05/REVIEW_BOM.csv`
- `docs/engineering/rvb22/analyses/i32/procurement_redline/history/native_05/REVIEW_COMPONENTS.step`
- `docs/engineering/rvb22/analyses/i32/procurement_redline/history/native_05/REVIEW_POSITIONS.csv`
- `docs/engineering/rvb22/analyses/i32/procurement_redline/history/native_05/REVIEW_SCHEMATIC.pdf`
- `docs/engineering/rvb22/analyses/i32/procurement_redline/history/native_05/SCHEMATIC_NETLIST.xml`
- `docs/engineering/rvb22/analyses/i32/procurement_redline/history/native_05/candidate_kicad/CAN.kicad_sch`
- `docs/engineering/rvb22/analyses/i32/procurement_redline/history/native_05/candidate_kicad/CANDIDATE_README.md`
- `docs/engineering/rvb22/analyses/i32/procurement_redline/history/native_05/candidate_kicad/ESP32.kicad_sch`
- `docs/engineering/rvb22/analyses/i32/procurement_redline/history/native_05/candidate_kicad/FITTED_REFERENCES.json`
- `docs/engineering/rvb22/analyses/i32/procurement_redline/history/native_05/candidate_kicad/GPS.kicad_sch`
- `docs/engineering/rvb22/analyses/i32/procurement_redline/history/native_05/candidate_kicad/GR86_CCA_RevB.kicad_dru`
- `docs/engineering/rvb22/analyses/i32/procurement_redline/history/native_05/candidate_kicad/GR86_CCA_RevB.kicad_pcb`
- `docs/engineering/rvb22/analyses/i32/procurement_redline/history/native_05/candidate_kicad/GR86_CCA_RevB.kicad_prl`
- `docs/engineering/rvb22/analyses/i32/procurement_redline/history/native_05/candidate_kicad/GR86_CCA_RevB.kicad_pro`
- `docs/engineering/rvb22/analyses/i32/procurement_redline/history/native_05/candidate_kicad/GR86_CCA_RevB.kicad_sch`
- `docs/engineering/rvb22/analyses/i32/procurement_redline/history/native_05/candidate_kicad/Input_Protection.kicad_sch`
- `docs/engineering/rvb22/analyses/i32/procurement_redline/history/native_05/candidate_kicad/LEDs_Status.kicad_sch`
- `docs/engineering/rvb22/analyses/i32/procurement_redline/history/native_05/candidate_kicad/Oil_Pressure.kicad_sch`
- `docs/engineering/rvb22/analyses/i32/procurement_redline/history/native_05/candidate_kicad/Power_3V3.kicad_sch`
- `docs/engineering/rvb22/analyses/i32/procurement_redline/history/native_05/candidate_kicad/Power_5V.kicad_sch`
- `docs/engineering/rvb22/analyses/i32/procurement_redline/history/native_05/candidate_kicad/Programming_Debug.kicad_sch`
- `docs/engineering/rvb22/analyses/i32/procurement_redline/history/native_05/candidate_kicad/RVB22_POWER_CANDIDATE_ONLY.txt`
- `docs/engineering/rvb22/analyses/i32/procurement_redline/history/native_05/candidate_kicad/Test_Points.kicad_sch`
- `docs/engineering/rvb22/analyses/i32/procurement_redline/history/native_05/candidate_kicad/Vehicle_Interconnect.kicad_sch`
- `docs/engineering/rvb22/analyses/i32/procurement_redline/history/native_05/candidate_kicad/fp-lib-table`
- `docs/engineering/rvb22/analyses/i32/procurement_redline/history/native_05/candidate_kicad/libraries/RevB.kicad_sym`
- `docs/engineering/rvb22/analyses/i32/procurement_redline/history/native_05/candidate_kicad/libraries/RevB.pretty/CDTop_PA1616D_20Pad_v06.kicad_mod`
- `docs/engineering/rvb22/analyses/i32/procurement_redline/history/native_05/candidate_kicad/libraries/RevB.pretty/C_0402_1005Metric.kicad_mod`
- `docs/engineering/rvb22/analyses/i32/procurement_redline/history/native_05/candidate_kicad/libraries/RevB.pretty/C_0603_1608Metric.kicad_mod`
- `docs/engineering/rvb22/analyses/i32/procurement_redline/history/native_05/candidate_kicad/libraries/RevB.pretty/C_0603_1608Metric_RVB22_C154.kicad_mod`
- `docs/engineering/rvb22/analyses/i32/procurement_redline/history/native_05/candidate_kicad/libraries/RevB.pretty/C_0603_1608Metric_RVB22_C205.kicad_mod`
- `docs/engineering/rvb22/analyses/i32/procurement_redline/history/native_05/candidate_kicad/libraries/RevB.pretty/C_0805_2012Metric.kicad_mod`
- `docs/engineering/rvb22/analyses/i32/procurement_redline/history/native_05/candidate_kicad/libraries/RevB.pretty/C_1210_3225Metric.kicad_mod`
- `docs/engineering/rvb22/analyses/i32/procurement_redline/history/native_05/candidate_kicad/libraries/RevB.pretty/Coilcraft_MSS1246T_12x12.kicad_mod`
- `docs/engineering/rvb22/analyses/i32/procurement_redline/history/native_05/candidate_kicad/libraries/RevB.pretty/Coilcraft_MSS1246T_12x12_RVB22_L121.kicad_mod`
- `docs/engineering/rvb22/analyses/i32/procurement_redline/history/native_05/candidate_kicad/libraries/RevB.pretty/D_SMA.kicad_mod`
- `docs/engineering/rvb22/analyses/i32/procurement_redline/history/native_05/candidate_kicad/libraries/RevB.pretty/D_SMB.kicad_mod`
- `docs/engineering/rvb22/analyses/i32/procurement_redline/history/native_05/candidate_kicad/libraries/RevB.pretty/D_SMC.kicad_mod`
- `docs/engineering/rvb22/analyses/i32/procurement_redline/history/native_05/candidate_kicad/libraries/RevB.pretty/D_SMC_RVB22_D103.kicad_mod`
- `docs/engineering/rvb22/analyses/i32/procurement_redline/history/native_05/candidate_kicad/libraries/RevB.pretty/D_SOD-123F.kicad_mod`
- `docs/engineering/rvb22/analyses/i32/procurement_redline/history/native_05/candidate_kicad/libraries/RevB.pretty/ESP32-S3-WROOM-1.kicad_mod`
- `docs/engineering/rvb22/analyses/i32/procurement_redline/history/native_05/candidate_kicad/libraries/RevB.pretty/ESP32-S3-WROOM-1_RVB22_U201.kicad_mod`
- `docs/engineering/rvb22/analyses/i32/procurement_redline/history/native_05/candidate_kicad/libraries/RevB.pretty/ESP32-S3-WROOM-1_RVB22_U201_TH48.kicad_mod`
- `docs/engineering/rvb22/analyses/i32/procurement_redline/history/native_05/candidate_kicad/libraries/RevB.pretty/Fuse_Littelfuse-NANO2-885.kicad_mod`
- `docs/engineering/rvb22/analyses/i32/procurement_redline/history/native_05/candidate_kicad/libraries/RevB.pretty/HTSSOP-16-1EP_4.4x5mm_P0.65mm_EP3.4x5mm_Mask2.46x2.31mm.kicad_mod`
- `docs/engineering/rvb22/analyses/i32/procurement_redline/history/native_05/candidate_kicad/libraries/RevB.pretty/HTSSOP-16-1EP_4.4x5mm_P0.65mm_EP3.4x5mm_Mask2.46x2.31mm_RVB22_U151.kicad_mod`
- `docs/engineering/rvb22/analyses/i32/procurement_redline/history/native_05/candidate_kicad/libraries/RevB.pretty/HTSSOP-16-1EP_4.4x5mm_P0.65mm_EP3x3mm.kicad_mod`
- `docs/engineering/rvb22/analyses/i32/procurement_redline/history/native_05/candidate_kicad/libraries/RevB.pretty/Hirose_UFL_R_SMT_1_80_RevB.kicad_mod`
- `docs/engineering/rvb22/analyses/i32/procurement_redline/history/native_05/candidate_kicad/libraries/RevB.pretty/I32_FINISHED_C159.kicad_mod`
- `docs/engineering/rvb22/analyses/i32/procurement_redline/history/native_05/candidate_kicad/libraries/RevB.pretty/I32_FINISHED_C161.kicad_mod`
- `docs/engineering/rvb22/analyses/i32/procurement_redline/history/native_05/candidate_kicad/libraries/RevB.pretty/I32_FINISHED_C162.kicad_mod`
- `docs/engineering/rvb22/analyses/i32/procurement_redline/history/native_05/candidate_kicad/libraries/RevB.pretty/I32_FINISHED_C165.kicad_mod`
- `docs/engineering/rvb22/analyses/i32/procurement_redline/history/native_05/candidate_kicad/libraries/RevB.pretty/I32_FINISHED_C166.kicad_mod`
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
- `docs/engineering/rvb22/analyses/i32/procurement_redline/history/native_05/candidate_kicad/libraries/RevB.pretty/I32_PROCUREMENT_R160.kicad_mod`
- `docs/engineering/rvb22/analyses/i32/procurement_redline/history/native_05/candidate_kicad/libraries/RevB.pretty/I32_PROCUREMENT_R161.kicad_mod`
- `docs/engineering/rvb22/analyses/i32/procurement_redline/history/native_05/candidate_kicad/libraries/RevB.pretty/I32_PROCUREMENT_R162.kicad_mod`
- `docs/engineering/rvb22/analyses/i32/procurement_redline/history/native_05/candidate_kicad/libraries/RevB.pretty/I32_PROCUREMENT_R163.kicad_mod`
- `docs/engineering/rvb22/analyses/i32/procurement_redline/history/native_05/candidate_kicad/libraries/RevB.pretty/I32_PROCUREMENT_R169.kicad_mod`
- `docs/engineering/rvb22/analyses/i32/procurement_redline/history/native_05/candidate_kicad/libraries/RevB.pretty/I32_PROCUREMENT_R170.kicad_mod`
- `docs/engineering/rvb22/analyses/i32/procurement_redline/history/native_05/candidate_kicad/libraries/RevB.pretty/I32_PROCUREMENT_U101.kicad_mod`
- `docs/engineering/rvb22/analyses/i32/procurement_redline/history/native_05/candidate_kicad/libraries/RevB.pretty/KEMET_C1210_10u50V.kicad_mod`
- `docs/engineering/rvb22/analyses/i32/procurement_redline/history/native_05/candidate_kicad/libraries/RevB.pretty/KEMET_T598_X_7343_Median.kicad_mod`
- `docs/engineering/rvb22/analyses/i32/procurement_redline/history/native_05/candidate_kicad/libraries/RevB.pretty/KEMET_T598_X_7343_Median_RVB22_C206.kicad_mod`
- `docs/engineering/rvb22/analyses/i32/procurement_redline/history/native_05/candidate_kicad/libraries/RevB.pretty/LED_0603_1608Metric.kicad_mod`
- `docs/engineering/rvb22/analyses/i32/procurement_redline/history/native_05/candidate_kicad/libraries/RevB.pretty/L_Coilcraft_XAL5030-XXX.kicad_mod`
- `docs/engineering/rvb22/analyses/i32/procurement_redline/history/native_05/candidate_kicad/libraries/RevB.pretty/MSOP-8_3x3mm_P0.65mm.kicad_mod`
- `docs/engineering/rvb22/analyses/i32/procurement_redline/history/native_05/candidate_kicad/libraries/RevB.pretty/Molex_Micro-Fit_3.0_43045-1200_2x06_P3.00mm_Horizontal.kicad_mod`
- `docs/engineering/rvb22/analyses/i32/procurement_redline/history/native_05/candidate_kicad/libraries/RevB.pretty/Molex_Micro-Fit_3.0_43045-1200_2x06_P3.00mm_Horizontal_RVB22_F1.kicad_mod`
- `docs/engineering/rvb22/analyses/i32/procurement_redline/history/native_05/candidate_kicad/libraries/RevB.pretty/MountingHole_4.4mm_Outboard.kicad_mod`
- `docs/engineering/rvb22/analyses/i32/procurement_redline/history/native_05/candidate_kicad/libraries/RevB.pretty/Murata_LQW18AS_1608.kicad_mod`
- `docs/engineering/rvb22/analyses/i32/procurement_redline/history/native_05/candidate_kicad/libraries/RevB.pretty/Nexperia_SOD323_PMEG2010BEA.kicad_mod`
- `docs/engineering/rvb22/analyses/i32/procurement_redline/history/native_05/candidate_kicad/libraries/RevB.pretty/PinHeader_1x02_P2.54mm_Vertical.kicad_mod`
- `docs/engineering/rvb22/analyses/i32/procurement_redline/history/native_05/candidate_kicad/libraries/RevB.pretty/R_0603_1608Metric.kicad_mod`
- `docs/engineering/rvb22/analyses/i32/procurement_redline/history/native_05/candidate_kicad/libraries/RevB.pretty/R_0603_1608Metric_RVB22_R155.kicad_mod`
- `docs/engineering/rvb22/analyses/i32/procurement_redline/history/native_05/candidate_kicad/libraries/RevB.pretty/R_0603_1608Metric_RVB22_R156.kicad_mod`
- `docs/engineering/rvb22/analyses/i32/procurement_redline/history/native_05/candidate_kicad/libraries/RevB.pretty/R_0603_1608Metric_RVB22_R157.kicad_mod`
- `docs/engineering/rvb22/analyses/i32/procurement_redline/history/native_05/candidate_kicad/libraries/RevB.pretty/R_0603_1608Metric_RVB22_R203.kicad_mod`
- `docs/engineering/rvb22/analyses/i32/procurement_redline/history/native_05/candidate_kicad/libraries/RevB.pretty/R_0805_2012Metric.kicad_mod`
- `docs/engineering/rvb22/analyses/i32/procurement_redline/history/native_05/candidate_kicad/libraries/RevB.pretty/R_1206_3216Metric.kicad_mod`
- `docs/engineering/rvb22/analyses/i32/procurement_redline/history/native_05/candidate_kicad/libraries/RevB.pretty/R_2512_6332Metric.kicad_mod`
- `docs/engineering/rvb22/analyses/i32/procurement_redline/history/native_05/candidate_kicad/libraries/RevB.pretty/SOIC-8_3.9x4.9mm_P1.27mm.kicad_mod`
- `docs/engineering/rvb22/analyses/i32/procurement_redline/history/native_05/candidate_kicad/libraries/RevB.pretty/SOT-23-5.kicad_mod`
- `docs/engineering/rvb22/analyses/i32/procurement_redline/history/native_05/candidate_kicad/libraries/RevB.pretty/SOT-23.kicad_mod`
- `docs/engineering/rvb22/analyses/i32/procurement_redline/history/native_05/candidate_kicad/libraries/RevB.pretty/SolderJumper-2_P1.3mm_Open_Pad1.0x1.5mm.kicad_mod`
- `docs/engineering/rvb22/analyses/i32/procurement_redline/history/native_05/candidate_kicad/libraries/RevB.pretty/TDK_CGA4J1_33N_I32.kicad_mod`
- `docs/engineering/rvb22/analyses/i32/procurement_redline/history/native_05/candidate_kicad/libraries/RevB.pretty/TI_DDA0008B_4214849B.kicad_mod`
- `docs/engineering/rvb22/analyses/i32/procurement_redline/history/native_05/candidate_kicad/libraries/RevB.pretty/TI_DPY0002A_TPD1E05U06_SMDMask.kicad_mod`
- `docs/engineering/rvb22/analyses/i32/procurement_redline/history/native_05/candidate_kicad/libraries/RevB.pretty/TI_DQC0010A_I32.kicad_mod`
- `docs/engineering/rvb22/analyses/i32/procurement_redline/history/native_05/candidate_kicad/libraries/RevB.pretty/TI_DRB0008J_TCAN3403.kicad_mod`
- `docs/engineering/rvb22/analyses/i32/procurement_redline/history/native_05/candidate_kicad/libraries/RevB.pretty/TI_PWP0016A_TPS2660.kicad_mod`
- `docs/engineering/rvb22/analyses/i32/procurement_redline/history/native_05/candidate_kicad/libraries/RevB.pretty/TO-252-2.kicad_mod`
- `docs/engineering/rvb22/analyses/i32/procurement_redline/history/native_05/candidate_kicad/libraries/RevB.pretty/TPS3808_DBV0006A.kicad_mod`
- `docs/engineering/rvb22/analyses/i32/procurement_redline/history/native_05/candidate_kicad/libraries/RevB.pretty/Tag-Connect_TC2030-IDC-NL_2x03_P1.27mm_Vertical.kicad_mod`
- `docs/engineering/rvb22/analyses/i32/procurement_redline/history/native_05/candidate_kicad/libraries/RevB.pretty/TestPoint_Pad_D1.5mm.kicad_mod`
- `docs/engineering/rvb22/analyses/i32/procurement_redline/history/native_05/candidate_kicad/libraries/RevB.pretty/U.FL_Hirose_U.FL-R-SMT-1_Vertical.kicad_mod`
- `docs/engineering/rvb22/analyses/i32/procurement_redline/history/native_05/candidate_kicad/libraries/RevB.pretty/VSSOP-8_2.3x2mm_P0.5mm.kicad_mod`
- `docs/engineering/rvb22/analyses/i32/procurement_redline/history/native_05/candidate_kicad/libraries/RevB.pretty/WSLP0603_MANUFACTURER.kicad_mod`
- `docs/engineering/rvb22/analyses/i32/procurement_redline/history/native_05/candidate_kicad/libraries/RevB.pretty/WSLP0603_MANUFACTURER_R153.kicad_mod`
- `docs/engineering/rvb22/analyses/i32/procurement_redline/history/native_05/candidate_kicad/libraries/RevB.pretty/Wurth_61300211121_1x02.kicad_mod`
- `docs/engineering/rvb22/analyses/i32/procurement_redline/history/native_05/candidate_kicad/models/ENVELOPE_CDTop_PA1616D_20Pad_v06.step`
- `docs/engineering/rvb22/analyses/i32/procurement_redline/history/native_05/candidate_kicad/models/ENVELOPE_C_0603_1608Metric_RVB22_C205.step`
- `docs/engineering/rvb22/analyses/i32/procurement_redline/history/native_05/candidate_kicad/models/ENVELOPE_Coilcraft_MSS1246T_12x12_RVB22_L121.step`
- `docs/engineering/rvb22/analyses/i32/procurement_redline/history/native_05/candidate_kicad/models/ENVELOPE_Fuse_Littelfuse-NANO2-885.step`
- `docs/engineering/rvb22/analyses/i32/procurement_redline/history/native_05/candidate_kicad/models/ENVELOPE_HTSSOP-16-1EP_4.4x5mm_P0.65mm_EP3.4x5mm_Mask2.46x2.31mm_RVB22_U151.step`
- `docs/engineering/rvb22/analyses/i32/procurement_redline/history/native_05/candidate_kicad/models/ENVELOPE_I32_PROCUREMENT_L121.step`
- `docs/engineering/rvb22/analyses/i32/procurement_redline/history/native_05/candidate_kicad/models/ENVELOPE_I32_PROCUREMENT_R155.step`
- `docs/engineering/rvb22/analyses/i32/procurement_redline/history/native_05/candidate_kicad/models/ENVELOPE_I32_PROCUREMENT_R156.step`
- `docs/engineering/rvb22/analyses/i32/procurement_redline/history/native_05/candidate_kicad/models/ENVELOPE_I32_PROCUREMENT_R160.step`
- `docs/engineering/rvb22/analyses/i32/procurement_redline/history/native_05/candidate_kicad/models/ENVELOPE_I32_PROCUREMENT_R161.step`
- `docs/engineering/rvb22/analyses/i32/procurement_redline/history/native_05/candidate_kicad/models/ENVELOPE_I32_PROCUREMENT_R162.step`
- `docs/engineering/rvb22/analyses/i32/procurement_redline/history/native_05/candidate_kicad/models/ENVELOPE_I32_PROCUREMENT_R163.step`
- `docs/engineering/rvb22/analyses/i32/procurement_redline/history/native_05/candidate_kicad/models/ENVELOPE_I32_PROCUREMENT_R169.step`
- `docs/engineering/rvb22/analyses/i32/procurement_redline/history/native_05/candidate_kicad/models/ENVELOPE_I32_PROCUREMENT_R170.step`
- `docs/engineering/rvb22/analyses/i32/procurement_redline/history/native_05/candidate_kicad/models/ENVELOPE_KEMET_C1210_10u50V.step`
- `docs/engineering/rvb22/analyses/i32/procurement_redline/history/native_05/candidate_kicad/models/ENVELOPE_KEMET_T598_X_7343_Median_RVB22_C206.step`
- `docs/engineering/rvb22/analyses/i32/procurement_redline/history/native_05/candidate_kicad/models/ENVELOPE_Molex_Micro-Fit_3.0_43045-1200_2x06_P3.00mm_Horizontal_RVB22_F1.step`
- `docs/engineering/rvb22/analyses/i32/procurement_redline/history/native_05/candidate_kicad/models/ENVELOPE_Murata_LQW18AS_1608.step`
- `docs/engineering/rvb22/analyses/i32/procurement_redline/history/native_05/candidate_kicad/models/ENVELOPE_R_0603_1608Metric_RVB22_R155.step`
- `docs/engineering/rvb22/analyses/i32/procurement_redline/history/native_05/candidate_kicad/models/ENVELOPE_R_0603_1608Metric_RVB22_R156.step`
- `docs/engineering/rvb22/analyses/i32/procurement_redline/history/native_05/candidate_kicad/models/ENVELOPE_R_0603_1608Metric_RVB22_R157.step`
- `docs/engineering/rvb22/analyses/i32/procurement_redline/history/native_05/candidate_kicad/models/ENVELOPE_R_0603_1608Metric_RVB22_R203.step`
- `docs/engineering/rvb22/analyses/i32/procurement_redline/history/native_05/candidate_kicad/models/ENVELOPE_TDK_CGA4J1_33N_I32.step`
- `docs/engineering/rvb22/analyses/i32/procurement_redline/history/native_05/candidate_kicad/models/ENVELOPE_TDK_CGA5L1_68N_I32.step`
- `docs/engineering/rvb22/analyses/i32/procurement_redline/history/native_05/candidate_kicad/models/ENVELOPE_TI_DDA0008B_4214849B.step`
- `docs/engineering/rvb22/analyses/i32/procurement_redline/history/native_05/candidate_kicad/models/ENVELOPE_TI_DPY0002A_TPD1E05U06_SMDMask.step`
- `docs/engineering/rvb22/analyses/i32/procurement_redline/history/native_05/candidate_kicad/models/ENVELOPE_TI_DQC0010A_I32.step`
- `docs/engineering/rvb22/analyses/i32/procurement_redline/history/native_05/candidate_kicad/models/ENVELOPE_TI_DRB0008J_TCAN3403.step`
- `docs/engineering/rvb22/analyses/i32/procurement_redline/history/native_05/candidate_kicad/models/ENVELOPE_TI_PWP0016A_TPS2660.step`
- `docs/engineering/rvb22/analyses/i32/procurement_redline/history/native_05/candidate_kicad/models/ENVELOPE_TPS3808_DBV0006A.step`
- `docs/engineering/rvb22/analyses/i32/procurement_redline/history/native_05/candidate_kicad/models/ENVELOPE_WSL2512_I32_R158.step`
- `docs/engineering/rvb22/analyses/i32/procurement_redline/history/native_05/candidate_kicad/models/ENVELOPE_WSLP0603_MANUFACTURER.step`
- `docs/engineering/rvb22/analyses/i32/procurement_redline/history/native_05/candidate_kicad/models/ENVELOPE_WSLP0603_MANUFACTURER_R153.step`
- `docs/engineering/rvb22/analyses/i32/procurement_redline/history/native_05/candidate_kicad/sym-lib-table`
- `docs/engineering/rvb22/analyses/i32/procurement_redline/history/native_05/logs/component_positions.stderr`
- `docs/engineering/rvb22/analyses/i32/procurement_redline/history/native_05/logs/component_positions.stdout`
- `docs/engineering/rvb22/analyses/i32/procurement_redline/history/native_05/logs/component_step.stderr`
- `docs/engineering/rvb22/analyses/i32/procurement_redline/history/native_05/logs/component_step.stdout`
- `docs/engineering/rvb22/analyses/i32/procurement_redline/history/native_05/logs/drc.stderr`
- `docs/engineering/rvb22/analyses/i32/procurement_redline/history/native_05/logs/drc.stdout`
- `docs/engineering/rvb22/analyses/i32/procurement_redline/history/native_05/logs/drills.stderr`
- `docs/engineering/rvb22/analyses/i32/procurement_redline/history/native_05/logs/drills.stdout`
- `docs/engineering/rvb22/analyses/i32/procurement_redline/history/native_05/logs/erc.stderr`
- `docs/engineering/rvb22/analyses/i32/procurement_redline/history/native_05/logs/erc.stdout`
- `docs/engineering/rvb22/analyses/i32/procurement_redline/history/native_05/logs/gerbers.stderr`
- `docs/engineering/rvb22/analyses/i32/procurement_redline/history/native_05/logs/gerbers.stdout`
- `docs/engineering/rvb22/analyses/i32/procurement_redline/history/native_05/logs/kicad_version.stderr`
- `docs/engineering/rvb22/analyses/i32/procurement_redline/history/native_05/logs/kicad_version.stdout`
- `docs/engineering/rvb22/analyses/i32/procurement_redline/history/native_05/logs/pcb_netlist.stderr`
- `docs/engineering/rvb22/analyses/i32/procurement_redline/history/native_05/logs/pcb_netlist.stdout`
- `docs/engineering/rvb22/analyses/i32/procurement_redline/history/native_05/logs/pcbnew_version.stderr`
- `docs/engineering/rvb22/analyses/i32/procurement_redline/history/native_05/logs/pcbnew_version.stdout`
- `docs/engineering/rvb22/analyses/i32/procurement_redline/history/native_05/logs/schematic_bom.stderr`
- `docs/engineering/rvb22/analyses/i32/procurement_redline/history/native_05/logs/schematic_bom.stdout`
- `docs/engineering/rvb22/analyses/i32/procurement_redline/history/native_05/logs/schematic_netlist.stderr`
- `docs/engineering/rvb22/analyses/i32/procurement_redline/history/native_05/logs/schematic_netlist.stdout`
- `docs/engineering/rvb22/analyses/i32/procurement_redline/history/native_05/logs/schematic_pdf.stderr`
- `docs/engineering/rvb22/analyses/i32/procurement_redline/history/native_05/logs/schematic_pdf.stdout`
- `docs/engineering/rvb22/analyses/i32/procurement_redline/history/native_05/logs/zone_refill.stderr`
- `docs/engineering/rvb22/analyses/i32/procurement_redline/history/native_05/logs/zone_refill.stdout`
- `docs/engineering/rvb22/analyses/i32/procurement_redline/history/native_05/model_export/GR86_CCA_RevB.kicad_pcb`
- `docs/engineering/rvb22/analyses/i32/procurement_redline/history/native_05/review_gerbers/GR86_CCA_RevB-B_Cu.gbl`
- `docs/engineering/rvb22/analyses/i32/procurement_redline/history/native_05/review_gerbers/GR86_CCA_RevB-B_Mask.gbs`
- `docs/engineering/rvb22/analyses/i32/procurement_redline/history/native_05/review_gerbers/GR86_CCA_RevB-B_Paste.gbp`
- `docs/engineering/rvb22/analyses/i32/procurement_redline/history/native_05/review_gerbers/GR86_CCA_RevB-B_Silkscreen.gbo`
- `docs/engineering/rvb22/analyses/i32/procurement_redline/history/native_05/review_gerbers/GR86_CCA_RevB-Edge_Cuts.gm1`
- `docs/engineering/rvb22/analyses/i32/procurement_redline/history/native_05/review_gerbers/GR86_CCA_RevB-F_Cu.gtl`
- `docs/engineering/rvb22/analyses/i32/procurement_redline/history/native_05/review_gerbers/GR86_CCA_RevB-F_Mask.gts`
- `docs/engineering/rvb22/analyses/i32/procurement_redline/history/native_05/review_gerbers/GR86_CCA_RevB-F_Paste.gtp`
- `docs/engineering/rvb22/analyses/i32/procurement_redline/history/native_05/review_gerbers/GR86_CCA_RevB-F_Silkscreen.gto`
- `docs/engineering/rvb22/analyses/i32/procurement_redline/history/native_05/review_gerbers/GR86_CCA_RevB-In1_Cu.g1`
- `docs/engineering/rvb22/analyses/i32/procurement_redline/history/native_05/review_gerbers/GR86_CCA_RevB-In2_Cu.g2`
- `docs/engineering/rvb22/analyses/i32/procurement_redline/history/native_05/review_gerbers/GR86_CCA_RevB-NPTH.drl`
- `docs/engineering/rvb22/analyses/i32/procurement_redline/history/native_05/review_gerbers/GR86_CCA_RevB-PTH.drl`
- `docs/engineering/rvb22/analyses/i32/procurement_redline/history/native_05/review_gerbers/GR86_CCA_RevB-job.gbrjob`
- `docs/engineering/rvb22/analyses/i32/procurement_redline/history/pre_ci_binding/FINAL_GATES.json`
- `docs/engineering/rvb22/analyses/i32/procurement_redline/history/pre_ci_binding/FINAL_REVIEW_REGISTER.json`
- `docs/engineering/rvb22/analyses/i32/procurement_redline/history/pre_ci_binding/I32_FINDINGS_REGISTER.json`
- `docs/engineering/rvb22/analyses/i32/procurement_redline/history/pre_redline/EXECUTION_PLAN_CURRENT.md`
- `docs/engineering/rvb22/analyses/i32/procurement_redline/history/pre_redline/GR86_CCA_RevB_Board_Vetting_Summary.md`
- `docs/engineering/rvb22/analyses/i32/procurement_redline/history/pre_redline/README.md`
- `docs/engineering/rvb22/analyses/i32/procurement_redline/history/pre_redline/analyses/i32/ADOPTED_ROUTE_INVENTORY.json`
- `docs/engineering/rvb22/analyses/i32/procurement_redline/history/pre_redline/analyses/i32/AUTHORED_CHANGES.json`
- `docs/engineering/rvb22/analyses/i32/procurement_redline/history/pre_redline/analyses/i32/DESIGN_AND_MODEL_BASIS.md`
- `docs/engineering/rvb22/analyses/i32/procurement_redline/history/pre_redline/analyses/i32/FINAL_EVIDENCE.json`
- `docs/engineering/rvb22/analyses/i32/procurement_redline/history/pre_redline/analyses/i32/FINDINGS_REGISTER.json`
- `docs/engineering/rvb22/analyses/i32/procurement_redline/history/pre_redline/analyses/i32/INPUT_RESULTS.json`
- `docs/engineering/rvb22/analyses/i32/procurement_redline/history/pre_redline/analyses/i32/LAYOUT_ASSESSMENT.md`
- `docs/engineering/rvb22/analyses/i32/procurement_redline/history/pre_redline/analyses/i32/POWER_RESULTS.json`
- `docs/engineering/rvb22/analyses/i32/procurement_redline/history/pre_redline/analyses/i32/QUALIFICATION_AND_SERVICE.md`
- `docs/engineering/rvb22/analyses/i32/procurement_redline/history/pre_redline/analyses/i32/README.md`
- `docs/engineering/rvb22/analyses/i32/procurement_redline/history/pre_redline/analyses/i32/SOURCE_AUDIT.json`
- `docs/engineering/rvb22/analyses/i32/procurement_redline/history/pre_redline/analyses/i32/SOURCE_BINDING.json`
- `docs/engineering/rvb22/analyses/i32/procurement_redline/history/pre_redline/analyses/i32/THERMAL_RESULTS.json`
- `docs/engineering/rvb22/analyses/i32/procurement_redline/history/pre_redline/ci/convergence02-thermal.yml`
- `docs/engineering/rvb22/analyses/i32/procurement_redline/history/pre_redline/ci/convergence04-release-thermal.yml`
- `docs/engineering/rvb22/analyses/i32/procurement_redline/history/pre_redline/ci/desktop-due-diligence.yml`
- `docs/engineering/rvb22/analyses/i32/procurement_redline/history/pre_redline/ci/desktop-feedback-native.yml`
- `docs/engineering/rvb22/analyses/i32/procurement_redline/history/pre_redline/ci/i27-final-clearance.yml`
- `docs/engineering/rvb22/analyses/i32/procurement_redline/history/pre_redline/current/EXECUTION_PLAN.md`
- `docs/engineering/rvb22/analyses/i32/procurement_redline/history/pre_redline/current/GR86_CCA_RevB_ERB_CCB_Review_Register.xlsx`
- `docs/engineering/rvb22/analyses/i32/procurement_redline/history/pre_redline/current/I22_REPRODUCTION.md`
- `docs/engineering/rvb22/analyses/i32/procurement_redline/history/pre_redline/current/MANUFACTURING_AND_ASSEMBLY.md`
- `docs/engineering/rvb22/analyses/i32/procurement_redline/history/pre_redline/current/SOURCE_EFFECTIVITY.json`
- `docs/engineering/rvb22/analyses/i32/procurement_redline/history/pre_redline/current/THERMAL_REVIEW.md`
- `docs/engineering/rvb22/analyses/i32/procurement_redline/history/pre_redline/product/PACKAGE_VERIFICATION.json`
- `docs/engineering/rvb22/analyses/i32/procurement_redline/history/pre_redline/product/PRODUCT_HANDOFF.md`
- `docs/engineering/rvb22/analyses/i32/procurement_redline/history/pre_redline/product/SOURCES.json`
- `docs/engineering/rvb22/analyses/i32/procurement_redline/layout/Discharge_power_routes.png`
- `docs/engineering/rvb22/analyses/i32/procurement_redline/layout/Input_power_routes.png`
- `docs/engineering/rvb22/analyses/i32/procurement_redline/layout/LAYOUT_MEASUREMENTS.json`
- `docs/engineering/rvb22/analyses/i32/procurement_redline/layout/Reservoir_tab_power_routes.png`
- `docs/engineering/rvb22/analyses/i32/procurement_redline/layout/Reset_delay_power_routes.png`
- `docs/engineering/rvb22/analyses/i32/procurement_redline/layout/U121_power_routes.png`
- `docs/engineering/rvb22/analyses/i32/procurement_redline/layout/U151_power_routes.png`
- `docs/engineering/rvb22/analyses/i32/procurement_redline/layout/U152_power_routes.png`
- `docs/engineering/rvb22/analyses/i32/procurement_redline/manufacturing_audit/RESULTS.json`
- `docs/engineering/rvb22/analyses/i32/procurement_redline/manufacturing_audit_final/RESULTS.json`
- `docs/engineering/rvb22/analyses/i32/procurement_redline/mechanics/MECHANICAL.json`
- `docs/engineering/rvb22/analyses/i32/procurement_redline/mechanics_final/MECHANICAL.json`
- `docs/engineering/rvb22/analyses/i32/procurement_redline/native/COPIED_SOURCE_INVENTORY.json`
- `docs/engineering/rvb22/analyses/i32/procurement_redline/native/DRC.json`
- `docs/engineering/rvb22/analyses/i32/procurement_redline/native/ERC.json`
- `docs/engineering/rvb22/analyses/i32/procurement_redline/native/MODEL_RESOLUTION.json`
- `docs/engineering/rvb22/analyses/i32/procurement_redline/native/OUTPUT_MANIFEST.json`
- `docs/engineering/rvb22/analyses/i32/procurement_redline/native/PCB_NETLIST.d356`
- `docs/engineering/rvb22/analyses/i32/procurement_redline/native/RESULT.json`
- `docs/engineering/rvb22/analyses/i32/procurement_redline/native/REVIEW_BOM.csv`
- `docs/engineering/rvb22/analyses/i32/procurement_redline/native/REVIEW_COMPONENTS.step`
- `docs/engineering/rvb22/analyses/i32/procurement_redline/native/REVIEW_POSITIONS.csv`
- `docs/engineering/rvb22/analyses/i32/procurement_redline/native/REVIEW_SCHEMATIC.pdf`
- `docs/engineering/rvb22/analyses/i32/procurement_redline/native/SCHEMATIC_NETLIST.xml`
- `docs/engineering/rvb22/analyses/i32/procurement_redline/native/candidate_kicad/CAN.kicad_sch`
- `docs/engineering/rvb22/analyses/i32/procurement_redline/native/candidate_kicad/CANDIDATE_README.md`
- `docs/engineering/rvb22/analyses/i32/procurement_redline/native/candidate_kicad/ESP32.kicad_sch`
- `docs/engineering/rvb22/analyses/i32/procurement_redline/native/candidate_kicad/FITTED_REFERENCES.json`
- `docs/engineering/rvb22/analyses/i32/procurement_redline/native/candidate_kicad/GPS.kicad_sch`
- `docs/engineering/rvb22/analyses/i32/procurement_redline/native/candidate_kicad/GR86_CCA_RevB.kicad_dru`
- `docs/engineering/rvb22/analyses/i32/procurement_redline/native/candidate_kicad/GR86_CCA_RevB.kicad_pcb`
- `docs/engineering/rvb22/analyses/i32/procurement_redline/native/candidate_kicad/GR86_CCA_RevB.kicad_prl`
- `docs/engineering/rvb22/analyses/i32/procurement_redline/native/candidate_kicad/GR86_CCA_RevB.kicad_pro`
- `docs/engineering/rvb22/analyses/i32/procurement_redline/native/candidate_kicad/GR86_CCA_RevB.kicad_sch`
- `docs/engineering/rvb22/analyses/i32/procurement_redline/native/candidate_kicad/Input_Protection.kicad_sch`
- `docs/engineering/rvb22/analyses/i32/procurement_redline/native/candidate_kicad/LEDs_Status.kicad_sch`
- `docs/engineering/rvb22/analyses/i32/procurement_redline/native/candidate_kicad/Oil_Pressure.kicad_sch`
- `docs/engineering/rvb22/analyses/i32/procurement_redline/native/candidate_kicad/Power_3V3.kicad_sch`
- `docs/engineering/rvb22/analyses/i32/procurement_redline/native/candidate_kicad/Power_5V.kicad_sch`
- `docs/engineering/rvb22/analyses/i32/procurement_redline/native/candidate_kicad/Programming_Debug.kicad_sch`
- `docs/engineering/rvb22/analyses/i32/procurement_redline/native/candidate_kicad/RVB22_POWER_CANDIDATE_ONLY.txt`
- `docs/engineering/rvb22/analyses/i32/procurement_redline/native/candidate_kicad/Test_Points.kicad_sch`
- `docs/engineering/rvb22/analyses/i32/procurement_redline/native/candidate_kicad/Vehicle_Interconnect.kicad_sch`
- `docs/engineering/rvb22/analyses/i32/procurement_redline/native/candidate_kicad/fp-lib-table`
- `docs/engineering/rvb22/analyses/i32/procurement_redline/native/candidate_kicad/libraries/RevB.kicad_sym`
- `docs/engineering/rvb22/analyses/i32/procurement_redline/native/candidate_kicad/libraries/RevB.pretty/CDTop_PA1616D_20Pad_v06.kicad_mod`
- `docs/engineering/rvb22/analyses/i32/procurement_redline/native/candidate_kicad/libraries/RevB.pretty/C_0402_1005Metric.kicad_mod`
- `docs/engineering/rvb22/analyses/i32/procurement_redline/native/candidate_kicad/libraries/RevB.pretty/C_0603_1608Metric.kicad_mod`
- `docs/engineering/rvb22/analyses/i32/procurement_redline/native/candidate_kicad/libraries/RevB.pretty/C_0603_1608Metric_RVB22_C154.kicad_mod`
- `docs/engineering/rvb22/analyses/i32/procurement_redline/native/candidate_kicad/libraries/RevB.pretty/C_0603_1608Metric_RVB22_C205.kicad_mod`
- `docs/engineering/rvb22/analyses/i32/procurement_redline/native/candidate_kicad/libraries/RevB.pretty/C_0805_2012Metric.kicad_mod`
- `docs/engineering/rvb22/analyses/i32/procurement_redline/native/candidate_kicad/libraries/RevB.pretty/C_1210_3225Metric.kicad_mod`
- `docs/engineering/rvb22/analyses/i32/procurement_redline/native/candidate_kicad/libraries/RevB.pretty/Coilcraft_MSS1246T_12x12.kicad_mod`
- `docs/engineering/rvb22/analyses/i32/procurement_redline/native/candidate_kicad/libraries/RevB.pretty/Coilcraft_MSS1246T_12x12_RVB22_L121.kicad_mod`
- `docs/engineering/rvb22/analyses/i32/procurement_redline/native/candidate_kicad/libraries/RevB.pretty/D_SMA.kicad_mod`
- `docs/engineering/rvb22/analyses/i32/procurement_redline/native/candidate_kicad/libraries/RevB.pretty/D_SMB.kicad_mod`
- `docs/engineering/rvb22/analyses/i32/procurement_redline/native/candidate_kicad/libraries/RevB.pretty/D_SMC.kicad_mod`
- `docs/engineering/rvb22/analyses/i32/procurement_redline/native/candidate_kicad/libraries/RevB.pretty/D_SMC_RVB22_D103.kicad_mod`
- `docs/engineering/rvb22/analyses/i32/procurement_redline/native/candidate_kicad/libraries/RevB.pretty/D_SOD-123F.kicad_mod`
- `docs/engineering/rvb22/analyses/i32/procurement_redline/native/candidate_kicad/libraries/RevB.pretty/ESP32-S3-WROOM-1.kicad_mod`
- `docs/engineering/rvb22/analyses/i32/procurement_redline/native/candidate_kicad/libraries/RevB.pretty/ESP32-S3-WROOM-1_RVB22_U201.kicad_mod`
- `docs/engineering/rvb22/analyses/i32/procurement_redline/native/candidate_kicad/libraries/RevB.pretty/ESP32-S3-WROOM-1_RVB22_U201_TH48.kicad_mod`
- `docs/engineering/rvb22/analyses/i32/procurement_redline/native/candidate_kicad/libraries/RevB.pretty/Fuse_Littelfuse-NANO2-885.kicad_mod`
- `docs/engineering/rvb22/analyses/i32/procurement_redline/native/candidate_kicad/libraries/RevB.pretty/HTSSOP-16-1EP_4.4x5mm_P0.65mm_EP3.4x5mm_Mask2.46x2.31mm.kicad_mod`
- `docs/engineering/rvb22/analyses/i32/procurement_redline/native/candidate_kicad/libraries/RevB.pretty/HTSSOP-16-1EP_4.4x5mm_P0.65mm_EP3.4x5mm_Mask2.46x2.31mm_RVB22_U151.kicad_mod`
- `docs/engineering/rvb22/analyses/i32/procurement_redline/native/candidate_kicad/libraries/RevB.pretty/HTSSOP-16-1EP_4.4x5mm_P0.65mm_EP3x3mm.kicad_mod`
- `docs/engineering/rvb22/analyses/i32/procurement_redline/native/candidate_kicad/libraries/RevB.pretty/Hirose_UFL_R_SMT_1_80_RevB.kicad_mod`
- `docs/engineering/rvb22/analyses/i32/procurement_redline/native/candidate_kicad/libraries/RevB.pretty/I32_FINISHED_C159.kicad_mod`
- `docs/engineering/rvb22/analyses/i32/procurement_redline/native/candidate_kicad/libraries/RevB.pretty/I32_FINISHED_C161.kicad_mod`
- `docs/engineering/rvb22/analyses/i32/procurement_redline/native/candidate_kicad/libraries/RevB.pretty/I32_FINISHED_C162.kicad_mod`
- `docs/engineering/rvb22/analyses/i32/procurement_redline/native/candidate_kicad/libraries/RevB.pretty/I32_FINISHED_C165.kicad_mod`
- `docs/engineering/rvb22/analyses/i32/procurement_redline/native/candidate_kicad/libraries/RevB.pretty/I32_FINISHED_C166.kicad_mod`
- `docs/engineering/rvb22/analyses/i32/procurement_redline/native/candidate_kicad/libraries/RevB.pretty/I32_FINISHED_C167.kicad_mod`
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
- `docs/engineering/rvb22/analyses/i32/procurement_redline/native/candidate_kicad/libraries/RevB.pretty/I32_PROCUREMENT_R163.kicad_mod`
- `docs/engineering/rvb22/analyses/i32/procurement_redline/native/candidate_kicad/libraries/RevB.pretty/I32_PROCUREMENT_R169.kicad_mod`
- `docs/engineering/rvb22/analyses/i32/procurement_redline/native/candidate_kicad/libraries/RevB.pretty/I32_PROCUREMENT_R170.kicad_mod`
- `docs/engineering/rvb22/analyses/i32/procurement_redline/native/candidate_kicad/libraries/RevB.pretty/I32_PROCUREMENT_U101.kicad_mod`
- `docs/engineering/rvb22/analyses/i32/procurement_redline/native/candidate_kicad/libraries/RevB.pretty/KEMET_C1210_10u50V.kicad_mod`
- `docs/engineering/rvb22/analyses/i32/procurement_redline/native/candidate_kicad/libraries/RevB.pretty/KEMET_T598_X_7343_Median.kicad_mod`
- `docs/engineering/rvb22/analyses/i32/procurement_redline/native/candidate_kicad/libraries/RevB.pretty/KEMET_T598_X_7343_Median_RVB22_C206.kicad_mod`
- `docs/engineering/rvb22/analyses/i32/procurement_redline/native/candidate_kicad/libraries/RevB.pretty/LED_0603_1608Metric.kicad_mod`
- `docs/engineering/rvb22/analyses/i32/procurement_redline/native/candidate_kicad/libraries/RevB.pretty/L_Coilcraft_XAL5030-XXX.kicad_mod`
- `docs/engineering/rvb22/analyses/i32/procurement_redline/native/candidate_kicad/libraries/RevB.pretty/MSOP-8_3x3mm_P0.65mm.kicad_mod`
- `docs/engineering/rvb22/analyses/i32/procurement_redline/native/candidate_kicad/libraries/RevB.pretty/Molex_Micro-Fit_3.0_43045-1200_2x06_P3.00mm_Horizontal.kicad_mod`
- `docs/engineering/rvb22/analyses/i32/procurement_redline/native/candidate_kicad/libraries/RevB.pretty/Molex_Micro-Fit_3.0_43045-1200_2x06_P3.00mm_Horizontal_RVB22_F1.kicad_mod`
- `docs/engineering/rvb22/analyses/i32/procurement_redline/native/candidate_kicad/libraries/RevB.pretty/MountingHole_4.4mm_Outboard.kicad_mod`
- `docs/engineering/rvb22/analyses/i32/procurement_redline/native/candidate_kicad/libraries/RevB.pretty/Murata_LQW18AS_1608.kicad_mod`
- `docs/engineering/rvb22/analyses/i32/procurement_redline/native/candidate_kicad/libraries/RevB.pretty/Nexperia_SOD323_PMEG2010BEA.kicad_mod`
- `docs/engineering/rvb22/analyses/i32/procurement_redline/native/candidate_kicad/libraries/RevB.pretty/PinHeader_1x02_P2.54mm_Vertical.kicad_mod`
- `docs/engineering/rvb22/analyses/i32/procurement_redline/native/candidate_kicad/libraries/RevB.pretty/R_0603_1608Metric.kicad_mod`
- `docs/engineering/rvb22/analyses/i32/procurement_redline/native/candidate_kicad/libraries/RevB.pretty/R_0603_1608Metric_RVB22_R155.kicad_mod`
- `docs/engineering/rvb22/analyses/i32/procurement_redline/native/candidate_kicad/libraries/RevB.pretty/R_0603_1608Metric_RVB22_R156.kicad_mod`
- `docs/engineering/rvb22/analyses/i32/procurement_redline/native/candidate_kicad/libraries/RevB.pretty/R_0603_1608Metric_RVB22_R157.kicad_mod`
- `docs/engineering/rvb22/analyses/i32/procurement_redline/native/candidate_kicad/libraries/RevB.pretty/R_0603_1608Metric_RVB22_R203.kicad_mod`
- `docs/engineering/rvb22/analyses/i32/procurement_redline/native/candidate_kicad/libraries/RevB.pretty/R_0805_2012Metric.kicad_mod`
- `docs/engineering/rvb22/analyses/i32/procurement_redline/native/candidate_kicad/libraries/RevB.pretty/R_1206_3216Metric.kicad_mod`
- `docs/engineering/rvb22/analyses/i32/procurement_redline/native/candidate_kicad/libraries/RevB.pretty/R_2512_6332Metric.kicad_mod`
- `docs/engineering/rvb22/analyses/i32/procurement_redline/native/candidate_kicad/libraries/RevB.pretty/SOIC-8_3.9x4.9mm_P1.27mm.kicad_mod`
- `docs/engineering/rvb22/analyses/i32/procurement_redline/native/candidate_kicad/libraries/RevB.pretty/SOT-23-5.kicad_mod`
- `docs/engineering/rvb22/analyses/i32/procurement_redline/native/candidate_kicad/libraries/RevB.pretty/SOT-23.kicad_mod`
- `docs/engineering/rvb22/analyses/i32/procurement_redline/native/candidate_kicad/libraries/RevB.pretty/SolderJumper-2_P1.3mm_Open_Pad1.0x1.5mm.kicad_mod`
- `docs/engineering/rvb22/analyses/i32/procurement_redline/native/candidate_kicad/libraries/RevB.pretty/TDK_CGA4J1_33N_I32.kicad_mod`
- `docs/engineering/rvb22/analyses/i32/procurement_redline/native/candidate_kicad/libraries/RevB.pretty/TI_DDA0008B_4214849B.kicad_mod`
- `docs/engineering/rvb22/analyses/i32/procurement_redline/native/candidate_kicad/libraries/RevB.pretty/TI_DPY0002A_TPD1E05U06_SMDMask.kicad_mod`
- `docs/engineering/rvb22/analyses/i32/procurement_redline/native/candidate_kicad/libraries/RevB.pretty/TI_DQC0010A_I32.kicad_mod`
- `docs/engineering/rvb22/analyses/i32/procurement_redline/native/candidate_kicad/libraries/RevB.pretty/TI_DRB0008J_TCAN3403.kicad_mod`
- `docs/engineering/rvb22/analyses/i32/procurement_redline/native/candidate_kicad/libraries/RevB.pretty/TI_PWP0016A_TPS2660.kicad_mod`
- `docs/engineering/rvb22/analyses/i32/procurement_redline/native/candidate_kicad/libraries/RevB.pretty/TO-252-2.kicad_mod`
- `docs/engineering/rvb22/analyses/i32/procurement_redline/native/candidate_kicad/libraries/RevB.pretty/TPS3808_DBV0006A.kicad_mod`
- `docs/engineering/rvb22/analyses/i32/procurement_redline/native/candidate_kicad/libraries/RevB.pretty/Tag-Connect_TC2030-IDC-NL_2x03_P1.27mm_Vertical.kicad_mod`
- `docs/engineering/rvb22/analyses/i32/procurement_redline/native/candidate_kicad/libraries/RevB.pretty/TestPoint_Pad_D1.5mm.kicad_mod`
- `docs/engineering/rvb22/analyses/i32/procurement_redline/native/candidate_kicad/libraries/RevB.pretty/U.FL_Hirose_U.FL-R-SMT-1_Vertical.kicad_mod`
- `docs/engineering/rvb22/analyses/i32/procurement_redline/native/candidate_kicad/libraries/RevB.pretty/VSSOP-8_2.3x2mm_P0.5mm.kicad_mod`
- `docs/engineering/rvb22/analyses/i32/procurement_redline/native/candidate_kicad/libraries/RevB.pretty/WSLP0603_MANUFACTURER.kicad_mod`
- `docs/engineering/rvb22/analyses/i32/procurement_redline/native/candidate_kicad/libraries/RevB.pretty/WSLP0603_MANUFACTURER_R153.kicad_mod`
- `docs/engineering/rvb22/analyses/i32/procurement_redline/native/candidate_kicad/libraries/RevB.pretty/Wurth_61300211121_1x02.kicad_mod`
- `docs/engineering/rvb22/analyses/i32/procurement_redline/native/candidate_kicad/models/ENVELOPE_CDTop_PA1616D_20Pad_v06.step`
- `docs/engineering/rvb22/analyses/i32/procurement_redline/native/candidate_kicad/models/ENVELOPE_C_0603_1608Metric_RVB22_C205.step`
- `docs/engineering/rvb22/analyses/i32/procurement_redline/native/candidate_kicad/models/ENVELOPE_Coilcraft_MSS1246T_12x12_RVB22_L121.step`
- `docs/engineering/rvb22/analyses/i32/procurement_redline/native/candidate_kicad/models/ENVELOPE_Fuse_Littelfuse-NANO2-885.step`
- `docs/engineering/rvb22/analyses/i32/procurement_redline/native/candidate_kicad/models/ENVELOPE_HTSSOP-16-1EP_4.4x5mm_P0.65mm_EP3.4x5mm_Mask2.46x2.31mm_RVB22_U151.step`
- `docs/engineering/rvb22/analyses/i32/procurement_redline/native/candidate_kicad/models/ENVELOPE_I32_PROCUREMENT_L121.step`
- `docs/engineering/rvb22/analyses/i32/procurement_redline/native/candidate_kicad/models/ENVELOPE_I32_PROCUREMENT_R155.step`
- `docs/engineering/rvb22/analyses/i32/procurement_redline/native/candidate_kicad/models/ENVELOPE_I32_PROCUREMENT_R156.step`
- `docs/engineering/rvb22/analyses/i32/procurement_redline/native/candidate_kicad/models/ENVELOPE_I32_PROCUREMENT_R160.step`
- `docs/engineering/rvb22/analyses/i32/procurement_redline/native/candidate_kicad/models/ENVELOPE_I32_PROCUREMENT_R161.step`
- `docs/engineering/rvb22/analyses/i32/procurement_redline/native/candidate_kicad/models/ENVELOPE_I32_PROCUREMENT_R162.step`
- `docs/engineering/rvb22/analyses/i32/procurement_redline/native/candidate_kicad/models/ENVELOPE_I32_PROCUREMENT_R163.step`
- `docs/engineering/rvb22/analyses/i32/procurement_redline/native/candidate_kicad/models/ENVELOPE_I32_PROCUREMENT_R169.step`
- `docs/engineering/rvb22/analyses/i32/procurement_redline/native/candidate_kicad/models/ENVELOPE_I32_PROCUREMENT_R170.step`
- `docs/engineering/rvb22/analyses/i32/procurement_redline/native/candidate_kicad/models/ENVELOPE_KEMET_C1210_10u50V.step`
- `docs/engineering/rvb22/analyses/i32/procurement_redline/native/candidate_kicad/models/ENVELOPE_KEMET_T598_X_7343_Median_RVB22_C206.step`
- `docs/engineering/rvb22/analyses/i32/procurement_redline/native/candidate_kicad/models/ENVELOPE_Molex_Micro-Fit_3.0_43045-1200_2x06_P3.00mm_Horizontal_RVB22_F1.step`
- `docs/engineering/rvb22/analyses/i32/procurement_redline/native/candidate_kicad/models/ENVELOPE_Murata_LQW18AS_1608.step`
- `docs/engineering/rvb22/analyses/i32/procurement_redline/native/candidate_kicad/models/ENVELOPE_R_0603_1608Metric_RVB22_R155.step`
- `docs/engineering/rvb22/analyses/i32/procurement_redline/native/candidate_kicad/models/ENVELOPE_R_0603_1608Metric_RVB22_R156.step`
- `docs/engineering/rvb22/analyses/i32/procurement_redline/native/candidate_kicad/models/ENVELOPE_R_0603_1608Metric_RVB22_R157.step`
- `docs/engineering/rvb22/analyses/i32/procurement_redline/native/candidate_kicad/models/ENVELOPE_R_0603_1608Metric_RVB22_R203.step`
- `docs/engineering/rvb22/analyses/i32/procurement_redline/native/candidate_kicad/models/ENVELOPE_TDK_CGA4J1_33N_I32.step`
- `docs/engineering/rvb22/analyses/i32/procurement_redline/native/candidate_kicad/models/ENVELOPE_TDK_CGA5L1_68N_I32.step`
- `docs/engineering/rvb22/analyses/i32/procurement_redline/native/candidate_kicad/models/ENVELOPE_TI_DDA0008B_4214849B.step`
- `docs/engineering/rvb22/analyses/i32/procurement_redline/native/candidate_kicad/models/ENVELOPE_TI_DPY0002A_TPD1E05U06_SMDMask.step`
- `docs/engineering/rvb22/analyses/i32/procurement_redline/native/candidate_kicad/models/ENVELOPE_TI_DQC0010A_I32.step`
- `docs/engineering/rvb22/analyses/i32/procurement_redline/native/candidate_kicad/models/ENVELOPE_TI_DRB0008J_TCAN3403.step`
- `docs/engineering/rvb22/analyses/i32/procurement_redline/native/candidate_kicad/models/ENVELOPE_TI_PWP0016A_TPS2660.step`
- `docs/engineering/rvb22/analyses/i32/procurement_redline/native/candidate_kicad/models/ENVELOPE_TPS3808_DBV0006A.step`
- `docs/engineering/rvb22/analyses/i32/procurement_redline/native/candidate_kicad/models/ENVELOPE_WSL2512_I32_R158.step`
- `docs/engineering/rvb22/analyses/i32/procurement_redline/native/candidate_kicad/models/ENVELOPE_WSLP0603_MANUFACTURER.step`
- `docs/engineering/rvb22/analyses/i32/procurement_redline/native/candidate_kicad/models/ENVELOPE_WSLP0603_MANUFACTURER_R153.step`
- `docs/engineering/rvb22/analyses/i32/procurement_redline/native/candidate_kicad/sym-lib-table`
- `docs/engineering/rvb22/analyses/i32/procurement_redline/native/logs/component_positions.stderr`
- `docs/engineering/rvb22/analyses/i32/procurement_redline/native/logs/component_positions.stdout`
- `docs/engineering/rvb22/analyses/i32/procurement_redline/native/logs/component_step.stderr`
- `docs/engineering/rvb22/analyses/i32/procurement_redline/native/logs/component_step.stdout`
- `docs/engineering/rvb22/analyses/i32/procurement_redline/native/logs/drc.stderr`
- `docs/engineering/rvb22/analyses/i32/procurement_redline/native/logs/drc.stdout`
- `docs/engineering/rvb22/analyses/i32/procurement_redline/native/logs/drills.stderr`
- `docs/engineering/rvb22/analyses/i32/procurement_redline/native/logs/drills.stdout`
- `docs/engineering/rvb22/analyses/i32/procurement_redline/native/logs/erc.stderr`
- `docs/engineering/rvb22/analyses/i32/procurement_redline/native/logs/erc.stdout`
- `docs/engineering/rvb22/analyses/i32/procurement_redline/native/logs/gerbers.stderr`
- `docs/engineering/rvb22/analyses/i32/procurement_redline/native/logs/gerbers.stdout`
- `docs/engineering/rvb22/analyses/i32/procurement_redline/native/logs/kicad_version.stderr`
- `docs/engineering/rvb22/analyses/i32/procurement_redline/native/logs/kicad_version.stdout`
- `docs/engineering/rvb22/analyses/i32/procurement_redline/native/logs/pcb_netlist.stderr`
- `docs/engineering/rvb22/analyses/i32/procurement_redline/native/logs/pcb_netlist.stdout`
- `docs/engineering/rvb22/analyses/i32/procurement_redline/native/logs/pcbnew_version.stderr`
- `docs/engineering/rvb22/analyses/i32/procurement_redline/native/logs/pcbnew_version.stdout`
- `docs/engineering/rvb22/analyses/i32/procurement_redline/native/logs/schematic_bom.stderr`
- `docs/engineering/rvb22/analyses/i32/procurement_redline/native/logs/schematic_bom.stdout`
- `docs/engineering/rvb22/analyses/i32/procurement_redline/native/logs/schematic_netlist.stderr`
- `docs/engineering/rvb22/analyses/i32/procurement_redline/native/logs/schematic_netlist.stdout`
- `docs/engineering/rvb22/analyses/i32/procurement_redline/native/logs/schematic_pdf.stderr`
- `docs/engineering/rvb22/analyses/i32/procurement_redline/native/logs/schematic_pdf.stdout`
- `docs/engineering/rvb22/analyses/i32/procurement_redline/native/logs/zone_refill.stderr`
- `docs/engineering/rvb22/analyses/i32/procurement_redline/native/logs/zone_refill.stdout`
- `docs/engineering/rvb22/analyses/i32/procurement_redline/native/model_export/GR86_CCA_RevB.kicad_pcb`
- `docs/engineering/rvb22/analyses/i32/procurement_redline/native/review_gerbers/GR86_CCA_RevB-B_Cu.gbl`
- `docs/engineering/rvb22/analyses/i32/procurement_redline/native/review_gerbers/GR86_CCA_RevB-B_Mask.gbs`
- `docs/engineering/rvb22/analyses/i32/procurement_redline/native/review_gerbers/GR86_CCA_RevB-B_Paste.gbp`
- `docs/engineering/rvb22/analyses/i32/procurement_redline/native/review_gerbers/GR86_CCA_RevB-B_Silkscreen.gbo`
- `docs/engineering/rvb22/analyses/i32/procurement_redline/native/review_gerbers/GR86_CCA_RevB-Edge_Cuts.gm1`
- `docs/engineering/rvb22/analyses/i32/procurement_redline/native/review_gerbers/GR86_CCA_RevB-F_Cu.gtl`
- `docs/engineering/rvb22/analyses/i32/procurement_redline/native/review_gerbers/GR86_CCA_RevB-F_Mask.gts`
- `docs/engineering/rvb22/analyses/i32/procurement_redline/native/review_gerbers/GR86_CCA_RevB-F_Paste.gtp`
- `docs/engineering/rvb22/analyses/i32/procurement_redline/native/review_gerbers/GR86_CCA_RevB-F_Silkscreen.gto`
- `docs/engineering/rvb22/analyses/i32/procurement_redline/native/review_gerbers/GR86_CCA_RevB-In1_Cu.g1`
- `docs/engineering/rvb22/analyses/i32/procurement_redline/native/review_gerbers/GR86_CCA_RevB-In2_Cu.g2`
- `docs/engineering/rvb22/analyses/i32/procurement_redline/native/review_gerbers/GR86_CCA_RevB-NPTH.drl`
- `docs/engineering/rvb22/analyses/i32/procurement_redline/native/review_gerbers/GR86_CCA_RevB-PTH.drl`
- `docs/engineering/rvb22/analyses/i32/procurement_redline/native/review_gerbers/GR86_CCA_RevB-job.gbrjob`
- `docs/engineering/rvb22/analyses/i32/procurement_redline/native_exports.log`
- `docs/engineering/rvb22/analyses/i32/procurement_redline/native_exports_final.log`
- `docs/engineering/rvb22/analyses/i32/procurement_redline/package_check.py`
- `docs/engineering/rvb22/analyses/i32/procurement_redline/references/C19679768.pdf`
- `docs/engineering/rvb22/analyses/i32/procurement_redline/references/C342967.pdf`
- `docs/engineering/rvb22/analyses/i32/procurement_redline/references/C688370.pdf`
- `docs/engineering/rvb22/analyses/i32/procurement_redline/references/C864499.pdf`
- `docs/engineering/rvb22/analyses/i32/procurement_redline/references/L121-manufacturer.pdf`
- `docs/engineering/rvb22/analyses/i32/procurement_redline/references/R156-landpatterns.pdf`
- `docs/engineering/rvb22/analyses/i32/procurement_redline/references/R156-plt.pdf`
- `docs/engineering/rvb22/analyses/i32/procurement_redline/requirements.txt`
- `docs/engineering/rvb22/analyses/i32/procurement_redline/restore_waveforms.py`
- `docs/engineering/rvb22/analyses/i32/procurement_redline/review_register/Power_3V3_native.png`
- `docs/engineering/rvb22/analyses/i32/procurement_redline/review_register/after.png`
- `docs/engineering/rvb22/analyses/i32/procurement_redline/review_register/before.png`
- `docs/engineering/rvb22/analyses/i32/procurement_redline/review_register/inspection.ndjson`
- `docs/engineering/rvb22/analyses/i32/procurement_redline/review_register/update_review_register.mjs`
- `docs/engineering/rvb22/analyses/i32/procurement_redline/sourcing_evidence.py`
- `docs/engineering/rvb22/analyses/i32/procurement_redline/spice/CONTROL_RESULTS.json`
- `docs/engineering/rvb22/analyses/i32/procurement_redline/spice/QUALIFICATION_SUMMARY.json`
- `docs/engineering/rvb22/analyses/i32/procurement_redline/spice/RAW_RECORD_MANIFEST.json`
- `docs/engineering/rvb22/analyses/i32/procurement_redline/spice/SWAP_RESULTS.json`
- `docs/engineering/rvb22/analyses/i32/procurement_redline/spice/controls/control__high_reference_slow_loop_low_damping/RESULT.json`
- `docs/engineering/rvb22/analyses/i32/procurement_redline/spice/controls/control__high_reference_slow_loop_low_damping/case.cir`
- `docs/engineering/rvb22/analyses/i32/procurement_redline/spice/controls/control__high_reference_slow_loop_low_damping/completion.txt`
- `docs/engineering/rvb22/analyses/i32/procurement_redline/spice/controls/control__high_reference_slow_loop_low_damping/lm63615_derivative.lib`
- `docs/engineering/rvb22/analyses/i32/procurement_redline/spice/controls/control__high_reference_slow_loop_low_damping/run.log`
- `docs/engineering/rvb22/analyses/i32/procurement_redline/spice/controls/control__high_reference_slow_loop_low_damping/trace.csv`
- `docs/engineering/rvb22/analyses/i32/procurement_redline/spice/controls/control__high_reference_slow_loop_low_damping/waveform.tsv.gz.part01`
- `docs/engineering/rvb22/analyses/i32/procurement_redline/spice/controls/control__high_reference_slow_loop_low_damping/waveform.tsv.gz.part02`
- `docs/engineering/rvb22/analyses/i32/procurement_redline/spice/controls/control__live_crank_6V/RESULT.json`
- `docs/engineering/rvb22/analyses/i32/procurement_redline/spice/controls/control__live_crank_6V/case.cir`
- `docs/engineering/rvb22/analyses/i32/procurement_redline/spice/controls/control__live_crank_6V/completion.txt`
- `docs/engineering/rvb22/analyses/i32/procurement_redline/spice/controls/control__live_crank_6V/lm63615_derivative.lib`
- `docs/engineering/rvb22/analyses/i32/procurement_redline/spice/controls/control__live_crank_6V/run.log`
- `docs/engineering/rvb22/analyses/i32/procurement_redline/spice/controls/control__live_crank_6V/trace.csv`
- `docs/engineering/rvb22/analyses/i32/procurement_redline/spice/controls/control__live_crank_6V/waveform.tsv.gz.part01`
- `docs/engineering/rvb22/analyses/i32/procurement_redline/spice/controls/control__live_crank_6V/waveform.tsv.gz.part02`
- `docs/engineering/rvb22/analyses/i32/procurement_redline/spice/controls/control__live_crank_6V/waveform.tsv.gz.part03`
- `docs/engineering/rvb22/analyses/i32/procurement_redline/spice/controls/control__live_crank_6V/waveform.tsv.gz.part04`
- `docs/engineering/rvb22/analyses/i32/procurement_redline/spice/controls/control__live_crank_6V/waveform.tsv.gz.part05`
- `docs/engineering/rvb22/analyses/i32/procurement_redline/spice/controls/control__live_crank_6V/waveform.tsv.gz.part06`
- `docs/engineering/rvb22/analyses/i32/procurement_redline/spice/controls/control__live_overvoltage_24V/RESULT.json`
- `docs/engineering/rvb22/analyses/i32/procurement_redline/spice/controls/control__live_overvoltage_24V/case.cir`
- `docs/engineering/rvb22/analyses/i32/procurement_redline/spice/controls/control__live_overvoltage_24V/completion.txt`
- `docs/engineering/rvb22/analyses/i32/procurement_redline/spice/controls/control__live_overvoltage_24V/lm63615_derivative.lib`
- `docs/engineering/rvb22/analyses/i32/procurement_redline/spice/controls/control__live_overvoltage_24V/run.log`
- `docs/engineering/rvb22/analyses/i32/procurement_redline/spice/controls/control__live_overvoltage_24V/trace.csv`
- `docs/engineering/rvb22/analyses/i32/procurement_redline/spice/controls/control__live_overvoltage_24V/waveform.tsv.gz.part01`
- `docs/engineering/rvb22/analyses/i32/procurement_redline/spice/controls/control__live_overvoltage_24V/waveform.tsv.gz.part02`
- `docs/engineering/rvb22/analyses/i32/procurement_redline/spice/controls/control__live_overvoltage_24V/waveform.tsv.gz.part03`
- `docs/engineering/rvb22/analyses/i32/procurement_redline/spice/controls/control__live_overvoltage_24V/waveform.tsv.gz.part04`
- `docs/engineering/rvb22/analyses/i32/procurement_redline/spice/controls/control__live_overvoltage_24V/waveform.tsv.gz.part05`
- `docs/engineering/rvb22/analyses/i32/procurement_redline/spice/controls/control__live_overvoltage_24V/waveform.tsv.gz.part06`
- `docs/engineering/rvb22/analyses/i32/procurement_redline/spice/controls/control__low_reference_slow_loop_aged_damping/RESULT.json`
- `docs/engineering/rvb22/analyses/i32/procurement_redline/spice/controls/control__low_reference_slow_loop_aged_damping/case.cir`
- `docs/engineering/rvb22/analyses/i32/procurement_redline/spice/controls/control__low_reference_slow_loop_aged_damping/completion.txt`
- `docs/engineering/rvb22/analyses/i32/procurement_redline/spice/controls/control__low_reference_slow_loop_aged_damping/lm63615_derivative.lib`
- `docs/engineering/rvb22/analyses/i32/procurement_redline/spice/controls/control__low_reference_slow_loop_aged_damping/run.log`
- `docs/engineering/rvb22/analyses/i32/procurement_redline/spice/controls/control__low_reference_slow_loop_aged_damping/trace.csv`
- `docs/engineering/rvb22/analyses/i32/procurement_redline/spice/controls/control__low_reference_slow_loop_aged_damping/waveform.tsv.gz.part01`
- `docs/engineering/rvb22/analyses/i32/procurement_redline/spice/controls/control__low_reference_slow_loop_aged_damping/waveform.tsv.gz.part02`
- `docs/engineering/rvb22/analyses/i32/procurement_redline/spice/controls/control__minimum_inductance_saturation_guard/RESULT.json`
- `docs/engineering/rvb22/analyses/i32/procurement_redline/spice/controls/control__minimum_inductance_saturation_guard/case.cir`
- `docs/engineering/rvb22/analyses/i32/procurement_redline/spice/controls/control__minimum_inductance_saturation_guard/completion.txt`
- `docs/engineering/rvb22/analyses/i32/procurement_redline/spice/controls/control__minimum_inductance_saturation_guard/lm63615_derivative.lib`
- `docs/engineering/rvb22/analyses/i32/procurement_redline/spice/controls/control__minimum_inductance_saturation_guard/run.log`
- `docs/engineering/rvb22/analyses/i32/procurement_redline/spice/controls/control__minimum_inductance_saturation_guard/trace.csv`
- `docs/engineering/rvb22/analyses/i32/procurement_redline/spice/controls/control__minimum_inductance_saturation_guard/waveform.tsv.gz.part01`
- `docs/engineering/rvb22/analyses/i32/procurement_redline/spice/controls/control__minimum_inductance_saturation_guard/waveform.tsv.gz.part02`
- `docs/engineering/rvb22/analyses/i32/procurement_redline/spice/controls/control__nominal_hot_leakage/RESULT.json`
- `docs/engineering/rvb22/analyses/i32/procurement_redline/spice/controls/control__nominal_hot_leakage/case.cir`
- `docs/engineering/rvb22/analyses/i32/procurement_redline/spice/controls/control__nominal_hot_leakage/completion.txt`
- `docs/engineering/rvb22/analyses/i32/procurement_redline/spice/controls/control__nominal_hot_leakage/lm63615_derivative.lib`
- `docs/engineering/rvb22/analyses/i32/procurement_redline/spice/controls/control__nominal_hot_leakage/run.log`
- `docs/engineering/rvb22/analyses/i32/procurement_redline/spice/controls/control__nominal_hot_leakage/trace.csv`
- `docs/engineering/rvb22/analyses/i32/procurement_redline/spice/controls/control__nominal_hot_leakage/waveform.tsv.gz.part01`
- `docs/engineering/rvb22/analyses/i32/procurement_redline/spice/controls/control__nominal_hot_leakage/waveform.tsv.gz.part02`
- `docs/engineering/rvb22/analyses/i32/procurement_redline/spice/replay_source/PROVENANCE.json`
- `docs/engineering/rvb22/analyses/i32/procurement_redline/spice/replay_source/final_procurement_spice_qual.py`
- `docs/engineering/rvb22/analyses/i32/procurement_redline/spice/replay_source/power_chain.py`
- `docs/engineering/rvb22/analyses/i32/procurement_redline/spice/replay_source/selected_power_cases.py`
- `docs/engineering/rvb22/analyses/i32/procurement_redline/spice/replay_source/substitution_spice_qual.py`
- `docs/engineering/rvb22/analyses/i32/procurement_redline/spice/swaps/swap__SNS_falling_restart/RESULT.json`
- `docs/engineering/rvb22/analyses/i32/procurement_redline/spice/swaps/swap__SNS_falling_restart/case.cir`
- `docs/engineering/rvb22/analyses/i32/procurement_redline/spice/swaps/swap__SNS_falling_restart/completion.txt`
- `docs/engineering/rvb22/analyses/i32/procurement_redline/spice/swaps/swap__SNS_falling_restart/lm63615_derivative.lib`
- `docs/engineering/rvb22/analyses/i32/procurement_redline/spice/swaps/swap__SNS_falling_restart/run.log`
- `docs/engineering/rvb22/analyses/i32/procurement_redline/spice/swaps/swap__SNS_falling_restart/trace.csv`
- `docs/engineering/rvb22/analyses/i32/procurement_redline/spice/swaps/swap__SNS_falling_restart/waveform.tsv.gz.part01`
- `docs/engineering/rvb22/analyses/i32/procurement_redline/spice/swaps/swap__SNS_falling_restart/waveform.tsv.gz.part02`
- `docs/engineering/rvb22/analyses/i32/procurement_redline/spice/swaps/swap__SNS_falling_restart/waveform.tsv.gz.part03`
- `docs/engineering/rvb22/analyses/i32/procurement_redline/spice/swaps/swap__SNS_falling_restart_stored_corner/RESULT.json`
- `docs/engineering/rvb22/analyses/i32/procurement_redline/spice/swaps/swap__SNS_falling_restart_stored_corner/case.cir`
- `docs/engineering/rvb22/analyses/i32/procurement_redline/spice/swaps/swap__SNS_falling_restart_stored_corner/completion.txt`
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
- `docs/engineering/rvb22/analyses/i32/procurement_redline/spice/swaps/swap__slowest_charging_earliest_boot/run.log`
- `docs/engineering/rvb22/analyses/i32/procurement_redline/spice/swaps/swap__slowest_charging_earliest_boot/trace.csv`
- `docs/engineering/rvb22/analyses/i32/procurement_redline/spice/swaps/swap__slowest_charging_earliest_boot/waveform.tsv.gz.part01`
- `docs/engineering/rvb22/analyses/i32/procurement_redline/spice/swaps/swap__slowest_charging_earliest_boot/waveform.tsv.gz.part02`
- `docs/engineering/rvb22/analyses/i32/procurement_redline/thermal/0.25/I32_measured_loss_allocation.json`
- `docs/engineering/rvb22/analyses/i32/procurement_redline/thermal/0.25/I32_measured_loss_allocation.npz`
- `docs/engineering/rvb22/analyses/i32/procurement_redline/thermal/0.25/I32_stacked_80pct_sensitivity.json`
- `docs/engineering/rvb22/analyses/i32/procurement_redline/thermal/0.25/I32_stacked_80pct_sensitivity.npz`
- `docs/engineering/rvb22/analyses/i32/procurement_redline/thermal/0.25/RESULTS.json`
- `docs/engineering/rvb22/analyses/i32/procurement_redline/thermal/0.25/retained_I25_vector_on_I32_copper.json`
- `docs/engineering/rvb22/analyses/i32/procurement_redline/thermal/0.25/retained_I25_vector_on_I32_copper.npz`
- `docs/engineering/rvb22/analyses/i32/procurement_redline/thermal/0.5/I32_measured_loss_allocation.json`
- `docs/engineering/rvb22/analyses/i32/procurement_redline/thermal/0.5/I32_measured_loss_allocation.npz`
- `docs/engineering/rvb22/analyses/i32/procurement_redline/thermal/0.5/I32_stacked_80pct_sensitivity.json`
- `docs/engineering/rvb22/analyses/i32/procurement_redline/thermal/0.5/I32_stacked_80pct_sensitivity.npz`
- `docs/engineering/rvb22/analyses/i32/procurement_redline/thermal/0.5/RESULTS.json`
- `docs/engineering/rvb22/analyses/i32/procurement_redline/thermal/0.5/retained_I25_vector_on_I32_copper.json`
- `docs/engineering/rvb22/analyses/i32/procurement_redline/thermal/0.5/retained_I25_vector_on_I32_copper.npz`
- `docs/engineering/rvb22/analyses/i32/procurement_redline/thermal_0.25_bound.log`
- `docs/engineering/rvb22/analyses/i32/procurement_redline/thermal_0.5.log`
- `docs/engineering/rvb22/analyses/i32/procurement_redline/thermal_0.5_bound.log`
- `docs/engineering/rvb22/analyses/i32/procurement_redline/verify_package.py`
- `docs/engineering/rvb22/analyses/i32/source_audit.py`
- `docs/engineering/rvb22/analyses/i32/substitution_spice_qual.py`
- `docs/engineering/rvb22/analyses/i32/thermal_check.py`
- `docs/engineering/rvb22/current/EXECUTION_PLAN.md`
- `docs/engineering/rvb22/current/GR86_CCA_RevB_ERB_CCB_Review_Register.xlsx`
- `docs/engineering/rvb22/current/I22_REPRODUCTION.md`
- `docs/engineering/rvb22/current/MANUFACTURING_AND_ASSEMBLY.md`
- `docs/engineering/rvb22/current/SOURCE_EFFECTIVITY.json`
- `docs/engineering/rvb22/current/THERMAL_REVIEW.md`
- `docs/engineering/rvb22/product/PACKAGE_VERIFICATION.json`
- `docs/engineering/rvb22/product/PRODUCT_HANDOFF.md`
- `docs/engineering/rvb22/product/SOURCES.json`

## Sourced ECAD and manufacturing successor (768)

- `.github/workflows/i32-sourced-package.yml`
- `README.md`
- `docs/engineering/rvb22/analyses/i32/procurement_completion/ASSEMBLY_AND_ACCEPTANCE.md`
- `docs/engineering/rvb22/analyses/i32/procurement_completion/CAD_PROPERTY_REDLINE.json`
- `docs/engineering/rvb22/analyses/i32/procurement_completion/CONTINUATION.md`
- `docs/engineering/rvb22/analyses/i32/procurement_completion/IDENTITY_ALIASES.md`
- `docs/engineering/rvb22/analyses/i32/procurement_completion/NATIVE_TOOLCHAIN.json`
- `docs/engineering/rvb22/analyses/i32/procurement_completion/README.md`
- `docs/engineering/rvb22/analyses/i32/procurement_completion/REGRESSION_TESTS.log`
- `docs/engineering/rvb22/analyses/i32/procurement_completion/SOURCES.json`
- `docs/engineering/rvb22/analyses/i32/procurement_completion/VERIFICATION.json`
- `docs/engineering/rvb22/analyses/i32/procurement_completion/build.py`
- `docs/engineering/rvb22/analyses/i32/procurement_completion/catalog/C161212.html.gz`
- `docs/engineering/rvb22/analyses/i32/procurement_completion/catalog/C161212.json`
- `docs/engineering/rvb22/analyses/i32/procurement_completion/catalog/C1709453.html.gz`
- `docs/engineering/rvb22/analyses/i32/procurement_completion/catalog/C1709453.json`
- `docs/engineering/rvb22/analyses/i32/procurement_completion/catalog/C1709494.html.gz`
- `docs/engineering/rvb22/analyses/i32/procurement_completion/catalog/C1709494.json`
- `docs/engineering/rvb22/analyses/i32/procurement_completion/catalog/C1710754.html.gz`
- `docs/engineering/rvb22/analyses/i32/procurement_completion/catalog/C1710754.json`
- `docs/engineering/rvb22/analyses/i32/procurement_completion/catalog/C190124.html.gz`
- `docs/engineering/rvb22/analyses/i32/procurement_completion/catalog/C190124.json`
- `docs/engineering/rvb22/analyses/i32/procurement_completion/catalog/C19679768.html.gz`
- `docs/engineering/rvb22/analyses/i32/procurement_completion/catalog/C19679768.json`
- `docs/engineering/rvb22/analyses/i32/procurement_completion/catalog/C1978408.html.gz`
- `docs/engineering/rvb22/analyses/i32/procurement_completion/catalog/C1978408.json`
- `docs/engineering/rvb22/analyses/i32/procurement_completion/catalog/C1981952.html.gz`
- `docs/engineering/rvb22/analyses/i32/procurement_completion/catalog/C1981952.json`
- `docs/engineering/rvb22/analyses/i32/procurement_completion/catalog/C1982070.html.gz`
- `docs/engineering/rvb22/analyses/i32/procurement_completion/catalog/C1982070.json`
- `docs/engineering/rvb22/analyses/i32/procurement_completion/catalog/C19941093.html.gz`
- `docs/engineering/rvb22/analyses/i32/procurement_completion/catalog/C19941093.json`
- `docs/engineering/rvb22/analyses/i32/procurement_completion/catalog/C2072225.html.gz`
- `docs/engineering/rvb22/analyses/i32/procurement_completion/catalog/C2072225.json`
- `docs/engineering/rvb22/analyses/i32/procurement_completion/catalog/C2074591.html.gz`
- `docs/engineering/rvb22/analyses/i32/procurement_completion/catalog/C2074591.json`
- `docs/engineering/rvb22/analyses/i32/procurement_completion/catalog/C2075852.html.gz`
- `docs/engineering/rvb22/analyses/i32/procurement_completion/catalog/C2075852.json`
- `docs/engineering/rvb22/analyses/i32/procurement_completion/catalog/C2076134.html.gz`
- `docs/engineering/rvb22/analyses/i32/procurement_completion/catalog/C2076134.json`
- `docs/engineering/rvb22/analyses/i32/procurement_completion/catalog/C2079063.html.gz`
- `docs/engineering/rvb22/analyses/i32/procurement_completion/catalog/C2079063.json`
- `docs/engineering/rvb22/analyses/i32/procurement_completion/catalog/C2089518.html.gz`
- `docs/engineering/rvb22/analyses/i32/procurement_completion/catalog/C2089518.json`
- `docs/engineering/rvb22/analyses/i32/procurement_completion/catalog/C2089718.html.gz`
- `docs/engineering/rvb22/analyses/i32/procurement_completion/catalog/C2089718.json`
- `docs/engineering/rvb22/analyses/i32/procurement_completion/catalog/C2100485.html.gz`
- `docs/engineering/rvb22/analyses/i32/procurement_completion/catalog/C2100485.json`
- `docs/engineering/rvb22/analyses/i32/procurement_completion/catalog/C21404.html.gz`
- `docs/engineering/rvb22/analyses/i32/procurement_completion/catalog/C21404.json`
- `docs/engineering/rvb22/analyses/i32/procurement_completion/catalog/C2167688.html.gz`
- `docs/engineering/rvb22/analyses/i32/procurement_completion/catalog/C2167688.json`
- `docs/engineering/rvb22/analyses/i32/procurement_completion/catalog/C2169200.html.gz`
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
- `docs/engineering/rvb22/analyses/i32/procurement_completion/catalog/C844929.html.gz`
- `docs/engineering/rvb22/analyses/i32/procurement_completion/catalog/C844929.json`
- `docs/engineering/rvb22/analyses/i32/procurement_completion/catalog/C844931.html.gz`
- `docs/engineering/rvb22/analyses/i32/procurement_completion/catalog/C844931.json`
- `docs/engineering/rvb22/analyses/i32/procurement_completion/catalog/C844933.html.gz`
- `docs/engineering/rvb22/analyses/i32/procurement_completion/catalog/C844933.json`
- `docs/engineering/rvb22/analyses/i32/procurement_completion/catalog/C85864.html.gz`
- `docs/engineering/rvb22/analyses/i32/procurement_completion/catalog/C85864.json`
- `docs/engineering/rvb22/analyses/i32/procurement_completion/catalog/C85973.html.gz`
- `docs/engineering/rvb22/analyses/i32/procurement_completion/catalog/C85973.json`
- `docs/engineering/rvb22/analyses/i32/procurement_completion/catalog/C864499.html.gz`
- `docs/engineering/rvb22/analyses/i32/procurement_completion/catalog/C864499.json`
- `docs/engineering/rvb22/analyses/i32/procurement_completion/catalog/C88374.html.gz`
- `docs/engineering/rvb22/analyses/i32/procurement_completion/catalog/C88374.json`
- `docs/engineering/rvb22/analyses/i32/procurement_completion/catalog/C88419.html.gz`
- `docs/engineering/rvb22/analyses/i32/procurement_completion/catalog/C88419.json`
- `docs/engineering/rvb22/analyses/i32/procurement_completion/catalog_search/search-CGA5L1C0G2A683J160AE.json`
- `docs/engineering/rvb22/analyses/i32/procurement_completion/catalog_search/search-LQW18AS1N6J0ZD.json`
- `docs/engineering/rvb22/analyses/i32/procurement_completion/catalog_search/search-S5JHE3_A_H.json`
- `docs/engineering/rvb22/analyses/i32/procurement_completion/catalog_search/search-SMCJ110AHE3_A_H.json`
- `docs/engineering/rvb22/analyses/i32/procurement_completion/catalog_search/search-TNPW060324K3BEEA.json`
- `docs/engineering/rvb22/analyses/i32/procurement_completion/catalog_search/search-TNPW1206549KBEEA.json`
- `docs/engineering/rvb22/analyses/i32/procurement_completion/catalog_search/search-TPS22953QDQCRQ1.json`
- `docs/engineering/rvb22/analyses/i32/procurement_completion/native/COPIED_SOURCE_INVENTORY.json`
- `docs/engineering/rvb22/analyses/i32/procurement_completion/native/DRC.json`
- `docs/engineering/rvb22/analyses/i32/procurement_completion/native/ERC.json`
- `docs/engineering/rvb22/analyses/i32/procurement_completion/native/OUTPUT_MANIFEST.json`
- `docs/engineering/rvb22/analyses/i32/procurement_completion/native/PCB_NETLIST.d356`
- `docs/engineering/rvb22/analyses/i32/procurement_completion/native/RESULT.json`
- `docs/engineering/rvb22/analyses/i32/procurement_completion/native/REVIEW_BOM.csv`
- `docs/engineering/rvb22/analyses/i32/procurement_completion/native/REVIEW_POSITIONS.csv`
- `docs/engineering/rvb22/analyses/i32/procurement_completion/native/REVIEW_SCHEMATIC.pdf`
- `docs/engineering/rvb22/analyses/i32/procurement_completion/native/SCHEMATIC_NETLIST.xml`
- `docs/engineering/rvb22/analyses/i32/procurement_completion/native/candidate_kicad/CAN.kicad_sch`
- `docs/engineering/rvb22/analyses/i32/procurement_completion/native/candidate_kicad/CANDIDATE_README.md`
- `docs/engineering/rvb22/analyses/i32/procurement_completion/native/candidate_kicad/ESP32.kicad_sch`
- `docs/engineering/rvb22/analyses/i32/procurement_completion/native/candidate_kicad/FITTED_REFERENCES.json`
- `docs/engineering/rvb22/analyses/i32/procurement_completion/native/candidate_kicad/GPS.kicad_sch`
- `docs/engineering/rvb22/analyses/i32/procurement_completion/native/candidate_kicad/GR86_CCA_RevB.kicad_dru`
- `docs/engineering/rvb22/analyses/i32/procurement_completion/native/candidate_kicad/GR86_CCA_RevB.kicad_pcb`
- `docs/engineering/rvb22/analyses/i32/procurement_completion/native/candidate_kicad/GR86_CCA_RevB.kicad_prl`
- `docs/engineering/rvb22/analyses/i32/procurement_completion/native/candidate_kicad/GR86_CCA_RevB.kicad_pro`
- `docs/engineering/rvb22/analyses/i32/procurement_completion/native/candidate_kicad/GR86_CCA_RevB.kicad_sch`
- `docs/engineering/rvb22/analyses/i32/procurement_completion/native/candidate_kicad/Input_Protection.kicad_sch`
- `docs/engineering/rvb22/analyses/i32/procurement_completion/native/candidate_kicad/LEDs_Status.kicad_sch`
- `docs/engineering/rvb22/analyses/i32/procurement_completion/native/candidate_kicad/Oil_Pressure.kicad_sch`
- `docs/engineering/rvb22/analyses/i32/procurement_completion/native/candidate_kicad/Power_3V3.kicad_sch`
- `docs/engineering/rvb22/analyses/i32/procurement_completion/native/candidate_kicad/Power_5V.kicad_sch`
- `docs/engineering/rvb22/analyses/i32/procurement_completion/native/candidate_kicad/Programming_Debug.kicad_sch`
- `docs/engineering/rvb22/analyses/i32/procurement_completion/native/candidate_kicad/RVB22_POWER_CANDIDATE_ONLY.txt`
- `docs/engineering/rvb22/analyses/i32/procurement_completion/native/candidate_kicad/Test_Points.kicad_sch`
- `docs/engineering/rvb22/analyses/i32/procurement_completion/native/candidate_kicad/Vehicle_Interconnect.kicad_sch`
- `docs/engineering/rvb22/analyses/i32/procurement_completion/native/candidate_kicad/fp-lib-table`
- `docs/engineering/rvb22/analyses/i32/procurement_completion/native/candidate_kicad/libraries/RevB.kicad_sym`
- `docs/engineering/rvb22/analyses/i32/procurement_completion/native/candidate_kicad/libraries/RevB.pretty/CDTop_PA1616D_20Pad_v06.kicad_mod`
- `docs/engineering/rvb22/analyses/i32/procurement_completion/native/candidate_kicad/libraries/RevB.pretty/C_0402_1005Metric.kicad_mod`
- `docs/engineering/rvb22/analyses/i32/procurement_completion/native/candidate_kicad/libraries/RevB.pretty/C_0603_1608Metric.kicad_mod`
- `docs/engineering/rvb22/analyses/i32/procurement_completion/native/candidate_kicad/libraries/RevB.pretty/C_0603_1608Metric_RVB22_C154.kicad_mod`
- `docs/engineering/rvb22/analyses/i32/procurement_completion/native/candidate_kicad/libraries/RevB.pretty/C_0603_1608Metric_RVB22_C205.kicad_mod`
- `docs/engineering/rvb22/analyses/i32/procurement_completion/native/candidate_kicad/libraries/RevB.pretty/C_0805_2012Metric.kicad_mod`
- `docs/engineering/rvb22/analyses/i32/procurement_completion/native/candidate_kicad/libraries/RevB.pretty/C_1210_3225Metric.kicad_mod`
- `docs/engineering/rvb22/analyses/i32/procurement_completion/native/candidate_kicad/libraries/RevB.pretty/Coilcraft_MSS1246T_12x12.kicad_mod`
- `docs/engineering/rvb22/analyses/i32/procurement_completion/native/candidate_kicad/libraries/RevB.pretty/Coilcraft_MSS1246T_12x12_RVB22_L121.kicad_mod`
- `docs/engineering/rvb22/analyses/i32/procurement_completion/native/candidate_kicad/libraries/RevB.pretty/D_SMA.kicad_mod`
- `docs/engineering/rvb22/analyses/i32/procurement_completion/native/candidate_kicad/libraries/RevB.pretty/D_SMB.kicad_mod`
- `docs/engineering/rvb22/analyses/i32/procurement_completion/native/candidate_kicad/libraries/RevB.pretty/D_SMC.kicad_mod`
- `docs/engineering/rvb22/analyses/i32/procurement_completion/native/candidate_kicad/libraries/RevB.pretty/D_SMC_RVB22_D103.kicad_mod`
- `docs/engineering/rvb22/analyses/i32/procurement_completion/native/candidate_kicad/libraries/RevB.pretty/D_SOD-123F.kicad_mod`
- `docs/engineering/rvb22/analyses/i32/procurement_completion/native/candidate_kicad/libraries/RevB.pretty/ESP32-S3-WROOM-1.kicad_mod`
- `docs/engineering/rvb22/analyses/i32/procurement_completion/native/candidate_kicad/libraries/RevB.pretty/ESP32-S3-WROOM-1_RVB22_U201.kicad_mod`
- `docs/engineering/rvb22/analyses/i32/procurement_completion/native/candidate_kicad/libraries/RevB.pretty/ESP32-S3-WROOM-1_RVB22_U201_TH48.kicad_mod`
- `docs/engineering/rvb22/analyses/i32/procurement_completion/native/candidate_kicad/libraries/RevB.pretty/Fuse_Littelfuse-NANO2-885.kicad_mod`
- `docs/engineering/rvb22/analyses/i32/procurement_completion/native/candidate_kicad/libraries/RevB.pretty/HTSSOP-16-1EP_4.4x5mm_P0.65mm_EP3.4x5mm_Mask2.46x2.31mm.kicad_mod`
- `docs/engineering/rvb22/analyses/i32/procurement_completion/native/candidate_kicad/libraries/RevB.pretty/HTSSOP-16-1EP_4.4x5mm_P0.65mm_EP3.4x5mm_Mask2.46x2.31mm_RVB22_U151.kicad_mod`
- `docs/engineering/rvb22/analyses/i32/procurement_completion/native/candidate_kicad/libraries/RevB.pretty/HTSSOP-16-1EP_4.4x5mm_P0.65mm_EP3x3mm.kicad_mod`
- `docs/engineering/rvb22/analyses/i32/procurement_completion/native/candidate_kicad/libraries/RevB.pretty/Hirose_UFL_R_SMT_1_80_RevB.kicad_mod`
- `docs/engineering/rvb22/analyses/i32/procurement_completion/native/candidate_kicad/libraries/RevB.pretty/I32_FINISHED_C159.kicad_mod`
- `docs/engineering/rvb22/analyses/i32/procurement_completion/native/candidate_kicad/libraries/RevB.pretty/I32_FINISHED_C161.kicad_mod`
- `docs/engineering/rvb22/analyses/i32/procurement_completion/native/candidate_kicad/libraries/RevB.pretty/I32_FINISHED_C162.kicad_mod`
- `docs/engineering/rvb22/analyses/i32/procurement_completion/native/candidate_kicad/libraries/RevB.pretty/I32_FINISHED_C165.kicad_mod`
- `docs/engineering/rvb22/analyses/i32/procurement_completion/native/candidate_kicad/libraries/RevB.pretty/I32_FINISHED_C166.kicad_mod`
- `docs/engineering/rvb22/analyses/i32/procurement_completion/native/candidate_kicad/libraries/RevB.pretty/I32_FINISHED_C167.kicad_mod`
- `docs/engineering/rvb22/analyses/i32/procurement_completion/native/candidate_kicad/libraries/RevB.pretty/I32_FINISHED_Q152.kicad_mod`
- `docs/engineering/rvb22/analyses/i32/procurement_completion/native/candidate_kicad/libraries/RevB.pretty/I32_FINISHED_Q153.kicad_mod`
- `docs/engineering/rvb22/analyses/i32/procurement_completion/native/candidate_kicad/libraries/RevB.pretty/I32_FINISHED_R151.kicad_mod`
- `docs/engineering/rvb22/analyses/i32/procurement_completion/native/candidate_kicad/libraries/RevB.pretty/I32_FINISHED_R155.kicad_mod`
- `docs/engineering/rvb22/analyses/i32/procurement_completion/native/candidate_kicad/libraries/RevB.pretty/I32_FINISHED_R156.kicad_mod`
- `docs/engineering/rvb22/analyses/i32/procurement_completion/native/candidate_kicad/libraries/RevB.pretty/I32_FINISHED_R158.kicad_mod`
- `docs/engineering/rvb22/analyses/i32/procurement_completion/native/candidate_kicad/libraries/RevB.pretty/I32_FINISHED_R159.kicad_mod`
- `docs/engineering/rvb22/analyses/i32/procurement_completion/native/candidate_kicad/libraries/RevB.pretty/I32_FINISHED_R160.kicad_mod`
- `docs/engineering/rvb22/analyses/i32/procurement_completion/native/candidate_kicad/libraries/RevB.pretty/I32_FINISHED_R161.kicad_mod`
- `docs/engineering/rvb22/analyses/i32/procurement_completion/native/candidate_kicad/libraries/RevB.pretty/I32_FINISHED_R162.kicad_mod`
- `docs/engineering/rvb22/analyses/i32/procurement_completion/native/candidate_kicad/libraries/RevB.pretty/I32_FINISHED_R163.kicad_mod`
- `docs/engineering/rvb22/analyses/i32/procurement_completion/native/candidate_kicad/libraries/RevB.pretty/I32_FINISHED_R164.kicad_mod`
- `docs/engineering/rvb22/analyses/i32/procurement_completion/native/candidate_kicad/libraries/RevB.pretty/I32_FINISHED_R165.kicad_mod`
- `docs/engineering/rvb22/analyses/i32/procurement_completion/native/candidate_kicad/libraries/RevB.pretty/I32_FINISHED_R166.kicad_mod`
- `docs/engineering/rvb22/analyses/i32/procurement_completion/native/candidate_kicad/libraries/RevB.pretty/I32_FINISHED_R167.kicad_mod`
- `docs/engineering/rvb22/analyses/i32/procurement_completion/native/candidate_kicad/libraries/RevB.pretty/I32_FINISHED_R168.kicad_mod`
- `docs/engineering/rvb22/analyses/i32/procurement_completion/native/candidate_kicad/libraries/RevB.pretty/I32_FINISHED_R169.kicad_mod`
- `docs/engineering/rvb22/analyses/i32/procurement_completion/native/candidate_kicad/libraries/RevB.pretty/I32_FINISHED_R170.kicad_mod`
- `docs/engineering/rvb22/analyses/i32/procurement_completion/native/candidate_kicad/libraries/RevB.pretty/I32_FINISHED_R204.kicad_mod`
- `docs/engineering/rvb22/analyses/i32/procurement_completion/native/candidate_kicad/libraries/RevB.pretty/I32_FINISHED_TP154.kicad_mod`
- `docs/engineering/rvb22/analyses/i32/procurement_completion/native/candidate_kicad/libraries/RevB.pretty/I32_FINISHED_U152.kicad_mod`
- `docs/engineering/rvb22/analyses/i32/procurement_completion/native/candidate_kicad/libraries/RevB.pretty/I32_FINISHED_U153.kicad_mod`
- `docs/engineering/rvb22/analyses/i32/procurement_completion/native/candidate_kicad/libraries/RevB.pretty/I32_PROCUREMENT_C152.kicad_mod`
- `docs/engineering/rvb22/analyses/i32/procurement_completion/native/candidate_kicad/libraries/RevB.pretty/I32_PROCUREMENT_C154.kicad_mod`
- `docs/engineering/rvb22/analyses/i32/procurement_completion/native/candidate_kicad/libraries/RevB.pretty/I32_PROCUREMENT_C165.kicad_mod`
- `docs/engineering/rvb22/analyses/i32/procurement_completion/native/candidate_kicad/libraries/RevB.pretty/I32_PROCUREMENT_L121.kicad_mod`
- `docs/engineering/rvb22/analyses/i32/procurement_completion/native/candidate_kicad/libraries/RevB.pretty/I32_PROCUREMENT_R155.kicad_mod`
- `docs/engineering/rvb22/analyses/i32/procurement_completion/native/candidate_kicad/libraries/RevB.pretty/I32_PROCUREMENT_R156.kicad_mod`
- `docs/engineering/rvb22/analyses/i32/procurement_completion/native/candidate_kicad/libraries/RevB.pretty/I32_PROCUREMENT_R160.kicad_mod`
- `docs/engineering/rvb22/analyses/i32/procurement_completion/native/candidate_kicad/libraries/RevB.pretty/I32_PROCUREMENT_R161.kicad_mod`
- `docs/engineering/rvb22/analyses/i32/procurement_completion/native/candidate_kicad/libraries/RevB.pretty/I32_PROCUREMENT_R162.kicad_mod`
- `docs/engineering/rvb22/analyses/i32/procurement_completion/native/candidate_kicad/libraries/RevB.pretty/I32_PROCUREMENT_R163.kicad_mod`
- `docs/engineering/rvb22/analyses/i32/procurement_completion/native/candidate_kicad/libraries/RevB.pretty/I32_PROCUREMENT_R169.kicad_mod`
- `docs/engineering/rvb22/analyses/i32/procurement_completion/native/candidate_kicad/libraries/RevB.pretty/I32_PROCUREMENT_R170.kicad_mod`
- `docs/engineering/rvb22/analyses/i32/procurement_completion/native/candidate_kicad/libraries/RevB.pretty/I32_PROCUREMENT_U101.kicad_mod`
- `docs/engineering/rvb22/analyses/i32/procurement_completion/native/candidate_kicad/libraries/RevB.pretty/KEMET_C1210_10u50V.kicad_mod`
- `docs/engineering/rvb22/analyses/i32/procurement_completion/native/candidate_kicad/libraries/RevB.pretty/KEMET_T598_X_7343_Median.kicad_mod`
- `docs/engineering/rvb22/analyses/i32/procurement_completion/native/candidate_kicad/libraries/RevB.pretty/KEMET_T598_X_7343_Median_RVB22_C206.kicad_mod`
- `docs/engineering/rvb22/analyses/i32/procurement_completion/native/candidate_kicad/libraries/RevB.pretty/LED_0603_1608Metric.kicad_mod`
- `docs/engineering/rvb22/analyses/i32/procurement_completion/native/candidate_kicad/libraries/RevB.pretty/L_Coilcraft_XAL5030-XXX.kicad_mod`
- `docs/engineering/rvb22/analyses/i32/procurement_completion/native/candidate_kicad/libraries/RevB.pretty/MSOP-8_3x3mm_P0.65mm.kicad_mod`
- `docs/engineering/rvb22/analyses/i32/procurement_completion/native/candidate_kicad/libraries/RevB.pretty/Molex_Micro-Fit_3.0_43045-1200_2x06_P3.00mm_Horizontal.kicad_mod`
- `docs/engineering/rvb22/analyses/i32/procurement_completion/native/candidate_kicad/libraries/RevB.pretty/Molex_Micro-Fit_3.0_43045-1200_2x06_P3.00mm_Horizontal_RVB22_F1.kicad_mod`
- `docs/engineering/rvb22/analyses/i32/procurement_completion/native/candidate_kicad/libraries/RevB.pretty/MountingHole_4.4mm_Outboard.kicad_mod`
- `docs/engineering/rvb22/analyses/i32/procurement_completion/native/candidate_kicad/libraries/RevB.pretty/Murata_LQW18AS_1608.kicad_mod`
- `docs/engineering/rvb22/analyses/i32/procurement_completion/native/candidate_kicad/libraries/RevB.pretty/Nexperia_SOD323_PMEG2010BEA.kicad_mod`
- `docs/engineering/rvb22/analyses/i32/procurement_completion/native/candidate_kicad/libraries/RevB.pretty/PinHeader_1x02_P2.54mm_Vertical.kicad_mod`
- `docs/engineering/rvb22/analyses/i32/procurement_completion/native/candidate_kicad/libraries/RevB.pretty/R_0603_1608Metric.kicad_mod`
- `docs/engineering/rvb22/analyses/i32/procurement_completion/native/candidate_kicad/libraries/RevB.pretty/R_0603_1608Metric_RVB22_R155.kicad_mod`
- `docs/engineering/rvb22/analyses/i32/procurement_completion/native/candidate_kicad/libraries/RevB.pretty/R_0603_1608Metric_RVB22_R156.kicad_mod`
- `docs/engineering/rvb22/analyses/i32/procurement_completion/native/candidate_kicad/libraries/RevB.pretty/R_0603_1608Metric_RVB22_R157.kicad_mod`
- `docs/engineering/rvb22/analyses/i32/procurement_completion/native/candidate_kicad/libraries/RevB.pretty/R_0603_1608Metric_RVB22_R203.kicad_mod`
- `docs/engineering/rvb22/analyses/i32/procurement_completion/native/candidate_kicad/libraries/RevB.pretty/R_0805_2012Metric.kicad_mod`
- `docs/engineering/rvb22/analyses/i32/procurement_completion/native/candidate_kicad/libraries/RevB.pretty/R_1206_3216Metric.kicad_mod`
- `docs/engineering/rvb22/analyses/i32/procurement_completion/native/candidate_kicad/libraries/RevB.pretty/R_2512_6332Metric.kicad_mod`
- `docs/engineering/rvb22/analyses/i32/procurement_completion/native/candidate_kicad/libraries/RevB.pretty/SOIC-8_3.9x4.9mm_P1.27mm.kicad_mod`
- `docs/engineering/rvb22/analyses/i32/procurement_completion/native/candidate_kicad/libraries/RevB.pretty/SOT-23-5.kicad_mod`
- `docs/engineering/rvb22/analyses/i32/procurement_completion/native/candidate_kicad/libraries/RevB.pretty/SOT-23.kicad_mod`
- `docs/engineering/rvb22/analyses/i32/procurement_completion/native/candidate_kicad/libraries/RevB.pretty/SolderJumper-2_P1.3mm_Open_Pad1.0x1.5mm.kicad_mod`
- `docs/engineering/rvb22/analyses/i32/procurement_completion/native/candidate_kicad/libraries/RevB.pretty/TDK_CGA4J1_33N_I32.kicad_mod`
- `docs/engineering/rvb22/analyses/i32/procurement_completion/native/candidate_kicad/libraries/RevB.pretty/TI_DDA0008B_4214849B.kicad_mod`
- `docs/engineering/rvb22/analyses/i32/procurement_completion/native/candidate_kicad/libraries/RevB.pretty/TI_DPY0002A_TPD1E05U06_SMDMask.kicad_mod`
- `docs/engineering/rvb22/analyses/i32/procurement_completion/native/candidate_kicad/libraries/RevB.pretty/TI_DQC0010A_I32.kicad_mod`
- `docs/engineering/rvb22/analyses/i32/procurement_completion/native/candidate_kicad/libraries/RevB.pretty/TI_DRB0008J_TCAN3403.kicad_mod`
- `docs/engineering/rvb22/analyses/i32/procurement_completion/native/candidate_kicad/libraries/RevB.pretty/TI_PWP0016A_TPS2660.kicad_mod`
- `docs/engineering/rvb22/analyses/i32/procurement_completion/native/candidate_kicad/libraries/RevB.pretty/TO-252-2.kicad_mod`
- `docs/engineering/rvb22/analyses/i32/procurement_completion/native/candidate_kicad/libraries/RevB.pretty/TPS3808_DBV0006A.kicad_mod`
- `docs/engineering/rvb22/analyses/i32/procurement_completion/native/candidate_kicad/libraries/RevB.pretty/Tag-Connect_TC2030-IDC-NL_2x03_P1.27mm_Vertical.kicad_mod`
- `docs/engineering/rvb22/analyses/i32/procurement_completion/native/candidate_kicad/libraries/RevB.pretty/TestPoint_Pad_D1.5mm.kicad_mod`
- `docs/engineering/rvb22/analyses/i32/procurement_completion/native/candidate_kicad/libraries/RevB.pretty/U.FL_Hirose_U.FL-R-SMT-1_Vertical.kicad_mod`
- `docs/engineering/rvb22/analyses/i32/procurement_completion/native/candidate_kicad/libraries/RevB.pretty/VSSOP-8_2.3x2mm_P0.5mm.kicad_mod`
- `docs/engineering/rvb22/analyses/i32/procurement_completion/native/candidate_kicad/libraries/RevB.pretty/WSLP0603_MANUFACTURER.kicad_mod`
- `docs/engineering/rvb22/analyses/i32/procurement_completion/native/candidate_kicad/libraries/RevB.pretty/WSLP0603_MANUFACTURER_R153.kicad_mod`
- `docs/engineering/rvb22/analyses/i32/procurement_completion/native/candidate_kicad/libraries/RevB.pretty/Wurth_61300211121_1x02.kicad_mod`
- `docs/engineering/rvb22/analyses/i32/procurement_completion/native/candidate_kicad/models/ENVELOPE_CDTop_PA1616D_20Pad_v06.step`
- `docs/engineering/rvb22/analyses/i32/procurement_completion/native/candidate_kicad/models/ENVELOPE_C_0603_1608Metric_RVB22_C205.step`
- `docs/engineering/rvb22/analyses/i32/procurement_completion/native/candidate_kicad/models/ENVELOPE_Coilcraft_MSS1246T_12x12_RVB22_L121.step`
- `docs/engineering/rvb22/analyses/i32/procurement_completion/native/candidate_kicad/models/ENVELOPE_Fuse_Littelfuse-NANO2-885.step`
- `docs/engineering/rvb22/analyses/i32/procurement_completion/native/candidate_kicad/models/ENVELOPE_HTSSOP-16-1EP_4.4x5mm_P0.65mm_EP3.4x5mm_Mask2.46x2.31mm_RVB22_U151.step`
- `docs/engineering/rvb22/analyses/i32/procurement_completion/native/candidate_kicad/models/ENVELOPE_I32_PROCUREMENT_L121.step`
- `docs/engineering/rvb22/analyses/i32/procurement_completion/native/candidate_kicad/models/ENVELOPE_I32_PROCUREMENT_R155.step`
- `docs/engineering/rvb22/analyses/i32/procurement_completion/native/candidate_kicad/models/ENVELOPE_I32_PROCUREMENT_R156.step`
- `docs/engineering/rvb22/analyses/i32/procurement_completion/native/candidate_kicad/models/ENVELOPE_I32_PROCUREMENT_R160.step`
- `docs/engineering/rvb22/analyses/i32/procurement_completion/native/candidate_kicad/models/ENVELOPE_I32_PROCUREMENT_R161.step`
- `docs/engineering/rvb22/analyses/i32/procurement_completion/native/candidate_kicad/models/ENVELOPE_I32_PROCUREMENT_R162.step`
- `docs/engineering/rvb22/analyses/i32/procurement_completion/native/candidate_kicad/models/ENVELOPE_I32_PROCUREMENT_R163.step`
- `docs/engineering/rvb22/analyses/i32/procurement_completion/native/candidate_kicad/models/ENVELOPE_I32_PROCUREMENT_R169.step`
- `docs/engineering/rvb22/analyses/i32/procurement_completion/native/candidate_kicad/models/ENVELOPE_I32_PROCUREMENT_R170.step`
- `docs/engineering/rvb22/analyses/i32/procurement_completion/native/candidate_kicad/models/ENVELOPE_KEMET_C1210_10u50V.step`
- `docs/engineering/rvb22/analyses/i32/procurement_completion/native/candidate_kicad/models/ENVELOPE_KEMET_T598_X_7343_Median_RVB22_C206.step`
- `docs/engineering/rvb22/analyses/i32/procurement_completion/native/candidate_kicad/models/ENVELOPE_Molex_Micro-Fit_3.0_43045-1200_2x06_P3.00mm_Horizontal_RVB22_F1.step`
- `docs/engineering/rvb22/analyses/i32/procurement_completion/native/candidate_kicad/models/ENVELOPE_Murata_LQW18AS_1608.step`
- `docs/engineering/rvb22/analyses/i32/procurement_completion/native/candidate_kicad/models/ENVELOPE_R_0603_1608Metric_RVB22_R155.step`
- `docs/engineering/rvb22/analyses/i32/procurement_completion/native/candidate_kicad/models/ENVELOPE_R_0603_1608Metric_RVB22_R156.step`
- `docs/engineering/rvb22/analyses/i32/procurement_completion/native/candidate_kicad/models/ENVELOPE_R_0603_1608Metric_RVB22_R157.step`
- `docs/engineering/rvb22/analyses/i32/procurement_completion/native/candidate_kicad/models/ENVELOPE_R_0603_1608Metric_RVB22_R203.step`
- `docs/engineering/rvb22/analyses/i32/procurement_completion/native/candidate_kicad/models/ENVELOPE_TDK_CGA4J1_33N_I32.step`
- `docs/engineering/rvb22/analyses/i32/procurement_completion/native/candidate_kicad/models/ENVELOPE_TDK_CGA5L1_68N_I32.step`
- `docs/engineering/rvb22/analyses/i32/procurement_completion/native/candidate_kicad/models/ENVELOPE_TI_DDA0008B_4214849B.step`
- `docs/engineering/rvb22/analyses/i32/procurement_completion/native/candidate_kicad/models/ENVELOPE_TI_DPY0002A_TPD1E05U06_SMDMask.step`
- `docs/engineering/rvb22/analyses/i32/procurement_completion/native/candidate_kicad/models/ENVELOPE_TI_DQC0010A_I32.step`
- `docs/engineering/rvb22/analyses/i32/procurement_completion/native/candidate_kicad/models/ENVELOPE_TI_DRB0008J_TCAN3403.step`
- `docs/engineering/rvb22/analyses/i32/procurement_completion/native/candidate_kicad/models/ENVELOPE_TI_PWP0016A_TPS2660.step`
- `docs/engineering/rvb22/analyses/i32/procurement_completion/native/candidate_kicad/models/ENVELOPE_TPS3808_DBV0006A.step`
- `docs/engineering/rvb22/analyses/i32/procurement_completion/native/candidate_kicad/models/ENVELOPE_WSL2512_I32_R158.step`
- `docs/engineering/rvb22/analyses/i32/procurement_completion/native/candidate_kicad/models/ENVELOPE_WSLP0603_MANUFACTURER.step`
- `docs/engineering/rvb22/analyses/i32/procurement_completion/native/candidate_kicad/models/ENVELOPE_WSLP0603_MANUFACTURER_R153.step`
- `docs/engineering/rvb22/analyses/i32/procurement_completion/native/candidate_kicad/sym-lib-table`
- `docs/engineering/rvb22/analyses/i32/procurement_completion/native/logs/component_positions.stderr`
- `docs/engineering/rvb22/analyses/i32/procurement_completion/native/logs/component_positions.stdout`
- `docs/engineering/rvb22/analyses/i32/procurement_completion/native/logs/drc.stderr`
- `docs/engineering/rvb22/analyses/i32/procurement_completion/native/logs/drc.stdout`
- `docs/engineering/rvb22/analyses/i32/procurement_completion/native/logs/drills.stderr`
- `docs/engineering/rvb22/analyses/i32/procurement_completion/native/logs/drills.stdout`
- `docs/engineering/rvb22/analyses/i32/procurement_completion/native/logs/erc.stderr`
- `docs/engineering/rvb22/analyses/i32/procurement_completion/native/logs/erc.stdout`
- `docs/engineering/rvb22/analyses/i32/procurement_completion/native/logs/gerbers.stderr`
- `docs/engineering/rvb22/analyses/i32/procurement_completion/native/logs/gerbers.stdout`
- `docs/engineering/rvb22/analyses/i32/procurement_completion/native/logs/kicad_version.stderr`
- `docs/engineering/rvb22/analyses/i32/procurement_completion/native/logs/kicad_version.stdout`
- `docs/engineering/rvb22/analyses/i32/procurement_completion/native/logs/pcb_netlist.stderr`
- `docs/engineering/rvb22/analyses/i32/procurement_completion/native/logs/pcb_netlist.stdout`
- `docs/engineering/rvb22/analyses/i32/procurement_completion/native/logs/pcbnew_version.stderr`
- `docs/engineering/rvb22/analyses/i32/procurement_completion/native/logs/pcbnew_version.stdout`
- `docs/engineering/rvb22/analyses/i32/procurement_completion/native/logs/schematic_bom.stderr`
- `docs/engineering/rvb22/analyses/i32/procurement_completion/native/logs/schematic_bom.stdout`
- `docs/engineering/rvb22/analyses/i32/procurement_completion/native/logs/schematic_netlist.stderr`
- `docs/engineering/rvb22/analyses/i32/procurement_completion/native/logs/schematic_netlist.stdout`
- `docs/engineering/rvb22/analyses/i32/procurement_completion/native/logs/schematic_pdf.stderr`
- `docs/engineering/rvb22/analyses/i32/procurement_completion/native/logs/schematic_pdf.stdout`
- `docs/engineering/rvb22/analyses/i32/procurement_completion/native/logs/zone_refill.stderr`
- `docs/engineering/rvb22/analyses/i32/procurement_completion/native/logs/zone_refill.stdout`
- `docs/engineering/rvb22/analyses/i32/procurement_completion/native/review_gerbers/GR86_CCA_RevB-B_Cu.gbl`
- `docs/engineering/rvb22/analyses/i32/procurement_completion/native/review_gerbers/GR86_CCA_RevB-B_Mask.gbs`
- `docs/engineering/rvb22/analyses/i32/procurement_completion/native/review_gerbers/GR86_CCA_RevB-B_Paste.gbp`
- `docs/engineering/rvb22/analyses/i32/procurement_completion/native/review_gerbers/GR86_CCA_RevB-B_Silkscreen.gbo`
- `docs/engineering/rvb22/analyses/i32/procurement_completion/native/review_gerbers/GR86_CCA_RevB-Edge_Cuts.gm1`
- `docs/engineering/rvb22/analyses/i32/procurement_completion/native/review_gerbers/GR86_CCA_RevB-F_Cu.gtl`
- `docs/engineering/rvb22/analyses/i32/procurement_completion/native/review_gerbers/GR86_CCA_RevB-F_Mask.gts`
- `docs/engineering/rvb22/analyses/i32/procurement_completion/native/review_gerbers/GR86_CCA_RevB-F_Paste.gtp`
- `docs/engineering/rvb22/analyses/i32/procurement_completion/native/review_gerbers/GR86_CCA_RevB-F_Silkscreen.gto`
- `docs/engineering/rvb22/analyses/i32/procurement_completion/native/review_gerbers/GR86_CCA_RevB-In1_Cu.g1`
- `docs/engineering/rvb22/analyses/i32/procurement_completion/native/review_gerbers/GR86_CCA_RevB-In2_Cu.g2`
- `docs/engineering/rvb22/analyses/i32/procurement_completion/native/review_gerbers/GR86_CCA_RevB-NPTH.drl`
- `docs/engineering/rvb22/analyses/i32/procurement_completion/native/review_gerbers/GR86_CCA_RevB-PTH.drl`
- `docs/engineering/rvb22/analyses/i32/procurement_completion/native/review_gerbers/GR86_CCA_RevB-job.gbrjob`
- `docs/engineering/rvb22/analyses/i32/procurement_completion/test_build.py`
- `docs/engineering/rvb22/current/i32_sourced_manufacturing/ASSEMBLY_AND_ACCEPTANCE.md`
- `docs/engineering/rvb22/current/i32_sourced_manufacturing/COHERENCE.json`
- `docs/engineering/rvb22/current/i32_sourced_manufacturing/FIRMWARE_EFFECTIVITY.json`
- `docs/engineering/rvb22/current/i32_sourced_manufacturing/IDENTITY_ALIASES.md`
- `docs/engineering/rvb22/current/i32_sourced_manufacturing/PROCUREMENT_SOURCES.json`
- `docs/engineering/rvb22/current/i32_sourced_manufacturing/README.md`
- `docs/engineering/rvb22/current/i32_sourced_manufacturing/SOURCE_MANIFEST.json`
- `docs/engineering/rvb22/current/i32_sourced_manufacturing/assembly/COMPLETE_FITTED_BOM.csv`
- `docs/engineering/rvb22/current/i32_sourced_manufacturing/assembly/DO_NOT_POPULATE.json`
- `docs/engineering/rvb22/current/i32_sourced_manufacturing/assembly/JLCPCB_BOM.csv`
- `docs/engineering/rvb22/current/i32_sourced_manufacturing/assembly/JLCPCB_CPL.csv`
- `docs/engineering/rvb22/current/i32_sourced_manufacturing/assembly/LOCAL_ASSEMBLY_BOM.csv`
- `docs/engineering/rvb22/current/i32_sourced_manufacturing/assembly/PREORDER_REQUIREMENTS.csv`
- `docs/engineering/rvb22/current/i32_sourced_manufacturing/assembly/PROCUREMENT_BOM.csv`
- `docs/engineering/rvb22/current/i32_sourced_manufacturing/assembly/PROCUREMENT_REDLINE.csv`
- `docs/engineering/rvb22/current/i32_sourced_manufacturing/documentation/POPULATED_COMPONENTS.step`
- `docs/engineering/rvb22/current/i32_sourced_manufacturing/documentation/QUALIFIED_ASSEMBLY_REQUIREMENTS.md`
- `docs/engineering/rvb22/current/i32_sourced_manufacturing/documentation/SCHEMATIC.pdf`
- `docs/engineering/rvb22/current/i32_sourced_manufacturing/documentation/SCHEMATIC_NETLIST.xml`
- `docs/engineering/rvb22/current/i32_sourced_manufacturing/editable_source/cad/CAN.kicad_sch`
- `docs/engineering/rvb22/current/i32_sourced_manufacturing/editable_source/cad/CANDIDATE_README.md`
- `docs/engineering/rvb22/current/i32_sourced_manufacturing/editable_source/cad/ESP32.kicad_sch`
- `docs/engineering/rvb22/current/i32_sourced_manufacturing/editable_source/cad/FITTED_REFERENCES.json`
- `docs/engineering/rvb22/current/i32_sourced_manufacturing/editable_source/cad/GPS.kicad_sch`
- `docs/engineering/rvb22/current/i32_sourced_manufacturing/editable_source/cad/GR86_CCA_RevB.kicad_dru`
- `docs/engineering/rvb22/current/i32_sourced_manufacturing/editable_source/cad/GR86_CCA_RevB.kicad_pcb`
- `docs/engineering/rvb22/current/i32_sourced_manufacturing/editable_source/cad/GR86_CCA_RevB.kicad_prl`
- `docs/engineering/rvb22/current/i32_sourced_manufacturing/editable_source/cad/GR86_CCA_RevB.kicad_pro`
- `docs/engineering/rvb22/current/i32_sourced_manufacturing/editable_source/cad/GR86_CCA_RevB.kicad_sch`
- `docs/engineering/rvb22/current/i32_sourced_manufacturing/editable_source/cad/Input_Protection.kicad_sch`
- `docs/engineering/rvb22/current/i32_sourced_manufacturing/editable_source/cad/LEDs_Status.kicad_sch`
- `docs/engineering/rvb22/current/i32_sourced_manufacturing/editable_source/cad/Oil_Pressure.kicad_sch`
- `docs/engineering/rvb22/current/i32_sourced_manufacturing/editable_source/cad/Power_3V3.kicad_sch`
- `docs/engineering/rvb22/current/i32_sourced_manufacturing/editable_source/cad/Power_5V.kicad_sch`
- `docs/engineering/rvb22/current/i32_sourced_manufacturing/editable_source/cad/Programming_Debug.kicad_sch`
- `docs/engineering/rvb22/current/i32_sourced_manufacturing/editable_source/cad/RVB22_POWER_CANDIDATE_ONLY.txt`
- `docs/engineering/rvb22/current/i32_sourced_manufacturing/editable_source/cad/Test_Points.kicad_sch`
- `docs/engineering/rvb22/current/i32_sourced_manufacturing/editable_source/cad/Vehicle_Interconnect.kicad_sch`
- `docs/engineering/rvb22/current/i32_sourced_manufacturing/editable_source/cad/fp-lib-table`
- `docs/engineering/rvb22/current/i32_sourced_manufacturing/editable_source/cad/libraries/RevB.kicad_sym`
- `docs/engineering/rvb22/current/i32_sourced_manufacturing/editable_source/cad/libraries/RevB.pretty/CDTop_PA1616D_20Pad_v06.kicad_mod`
- `docs/engineering/rvb22/current/i32_sourced_manufacturing/editable_source/cad/libraries/RevB.pretty/C_0402_1005Metric.kicad_mod`
- `docs/engineering/rvb22/current/i32_sourced_manufacturing/editable_source/cad/libraries/RevB.pretty/C_0603_1608Metric.kicad_mod`
- `docs/engineering/rvb22/current/i32_sourced_manufacturing/editable_source/cad/libraries/RevB.pretty/C_0603_1608Metric_RVB22_C154.kicad_mod`
- `docs/engineering/rvb22/current/i32_sourced_manufacturing/editable_source/cad/libraries/RevB.pretty/C_0603_1608Metric_RVB22_C205.kicad_mod`
- `docs/engineering/rvb22/current/i32_sourced_manufacturing/editable_source/cad/libraries/RevB.pretty/C_0805_2012Metric.kicad_mod`
- `docs/engineering/rvb22/current/i32_sourced_manufacturing/editable_source/cad/libraries/RevB.pretty/C_1210_3225Metric.kicad_mod`
- `docs/engineering/rvb22/current/i32_sourced_manufacturing/editable_source/cad/libraries/RevB.pretty/Coilcraft_MSS1246T_12x12.kicad_mod`
- `docs/engineering/rvb22/current/i32_sourced_manufacturing/editable_source/cad/libraries/RevB.pretty/Coilcraft_MSS1246T_12x12_RVB22_L121.kicad_mod`
- `docs/engineering/rvb22/current/i32_sourced_manufacturing/editable_source/cad/libraries/RevB.pretty/D_SMA.kicad_mod`
- `docs/engineering/rvb22/current/i32_sourced_manufacturing/editable_source/cad/libraries/RevB.pretty/D_SMB.kicad_mod`
- `docs/engineering/rvb22/current/i32_sourced_manufacturing/editable_source/cad/libraries/RevB.pretty/D_SMC.kicad_mod`
- `docs/engineering/rvb22/current/i32_sourced_manufacturing/editable_source/cad/libraries/RevB.pretty/D_SMC_RVB22_D103.kicad_mod`
- `docs/engineering/rvb22/current/i32_sourced_manufacturing/editable_source/cad/libraries/RevB.pretty/D_SOD-123F.kicad_mod`
- `docs/engineering/rvb22/current/i32_sourced_manufacturing/editable_source/cad/libraries/RevB.pretty/ESP32-S3-WROOM-1.kicad_mod`
- `docs/engineering/rvb22/current/i32_sourced_manufacturing/editable_source/cad/libraries/RevB.pretty/ESP32-S3-WROOM-1_RVB22_U201.kicad_mod`
- `docs/engineering/rvb22/current/i32_sourced_manufacturing/editable_source/cad/libraries/RevB.pretty/ESP32-S3-WROOM-1_RVB22_U201_TH48.kicad_mod`
- `docs/engineering/rvb22/current/i32_sourced_manufacturing/editable_source/cad/libraries/RevB.pretty/Fuse_Littelfuse-NANO2-885.kicad_mod`
- `docs/engineering/rvb22/current/i32_sourced_manufacturing/editable_source/cad/libraries/RevB.pretty/HTSSOP-16-1EP_4.4x5mm_P0.65mm_EP3.4x5mm_Mask2.46x2.31mm.kicad_mod`
- `docs/engineering/rvb22/current/i32_sourced_manufacturing/editable_source/cad/libraries/RevB.pretty/HTSSOP-16-1EP_4.4x5mm_P0.65mm_EP3.4x5mm_Mask2.46x2.31mm_RVB22_U151.kicad_mod`
- `docs/engineering/rvb22/current/i32_sourced_manufacturing/editable_source/cad/libraries/RevB.pretty/HTSSOP-16-1EP_4.4x5mm_P0.65mm_EP3x3mm.kicad_mod`
- `docs/engineering/rvb22/current/i32_sourced_manufacturing/editable_source/cad/libraries/RevB.pretty/Hirose_UFL_R_SMT_1_80_RevB.kicad_mod`
- `docs/engineering/rvb22/current/i32_sourced_manufacturing/editable_source/cad/libraries/RevB.pretty/I32_FINISHED_C159.kicad_mod`
- `docs/engineering/rvb22/current/i32_sourced_manufacturing/editable_source/cad/libraries/RevB.pretty/I32_FINISHED_C161.kicad_mod`
- `docs/engineering/rvb22/current/i32_sourced_manufacturing/editable_source/cad/libraries/RevB.pretty/I32_FINISHED_C162.kicad_mod`
- `docs/engineering/rvb22/current/i32_sourced_manufacturing/editable_source/cad/libraries/RevB.pretty/I32_FINISHED_C165.kicad_mod`
- `docs/engineering/rvb22/current/i32_sourced_manufacturing/editable_source/cad/libraries/RevB.pretty/I32_FINISHED_C166.kicad_mod`
- `docs/engineering/rvb22/current/i32_sourced_manufacturing/editable_source/cad/libraries/RevB.pretty/I32_FINISHED_C167.kicad_mod`
- `docs/engineering/rvb22/current/i32_sourced_manufacturing/editable_source/cad/libraries/RevB.pretty/I32_FINISHED_Q152.kicad_mod`
- `docs/engineering/rvb22/current/i32_sourced_manufacturing/editable_source/cad/libraries/RevB.pretty/I32_FINISHED_Q153.kicad_mod`
- `docs/engineering/rvb22/current/i32_sourced_manufacturing/editable_source/cad/libraries/RevB.pretty/I32_FINISHED_R151.kicad_mod`
- `docs/engineering/rvb22/current/i32_sourced_manufacturing/editable_source/cad/libraries/RevB.pretty/I32_FINISHED_R155.kicad_mod`
- `docs/engineering/rvb22/current/i32_sourced_manufacturing/editable_source/cad/libraries/RevB.pretty/I32_FINISHED_R156.kicad_mod`
- `docs/engineering/rvb22/current/i32_sourced_manufacturing/editable_source/cad/libraries/RevB.pretty/I32_FINISHED_R158.kicad_mod`
- `docs/engineering/rvb22/current/i32_sourced_manufacturing/editable_source/cad/libraries/RevB.pretty/I32_FINISHED_R159.kicad_mod`
- `docs/engineering/rvb22/current/i32_sourced_manufacturing/editable_source/cad/libraries/RevB.pretty/I32_FINISHED_R160.kicad_mod`
- `docs/engineering/rvb22/current/i32_sourced_manufacturing/editable_source/cad/libraries/RevB.pretty/I32_FINISHED_R161.kicad_mod`
- `docs/engineering/rvb22/current/i32_sourced_manufacturing/editable_source/cad/libraries/RevB.pretty/I32_FINISHED_R162.kicad_mod`
- `docs/engineering/rvb22/current/i32_sourced_manufacturing/editable_source/cad/libraries/RevB.pretty/I32_FINISHED_R163.kicad_mod`
- `docs/engineering/rvb22/current/i32_sourced_manufacturing/editable_source/cad/libraries/RevB.pretty/I32_FINISHED_R164.kicad_mod`
- `docs/engineering/rvb22/current/i32_sourced_manufacturing/editable_source/cad/libraries/RevB.pretty/I32_FINISHED_R165.kicad_mod`
- `docs/engineering/rvb22/current/i32_sourced_manufacturing/editable_source/cad/libraries/RevB.pretty/I32_FINISHED_R166.kicad_mod`
- `docs/engineering/rvb22/current/i32_sourced_manufacturing/editable_source/cad/libraries/RevB.pretty/I32_FINISHED_R167.kicad_mod`
- `docs/engineering/rvb22/current/i32_sourced_manufacturing/editable_source/cad/libraries/RevB.pretty/I32_FINISHED_R168.kicad_mod`
- `docs/engineering/rvb22/current/i32_sourced_manufacturing/editable_source/cad/libraries/RevB.pretty/I32_FINISHED_R169.kicad_mod`
- `docs/engineering/rvb22/current/i32_sourced_manufacturing/editable_source/cad/libraries/RevB.pretty/I32_FINISHED_R170.kicad_mod`
- `docs/engineering/rvb22/current/i32_sourced_manufacturing/editable_source/cad/libraries/RevB.pretty/I32_FINISHED_R204.kicad_mod`
- `docs/engineering/rvb22/current/i32_sourced_manufacturing/editable_source/cad/libraries/RevB.pretty/I32_FINISHED_TP154.kicad_mod`
- `docs/engineering/rvb22/current/i32_sourced_manufacturing/editable_source/cad/libraries/RevB.pretty/I32_FINISHED_U152.kicad_mod`
- `docs/engineering/rvb22/current/i32_sourced_manufacturing/editable_source/cad/libraries/RevB.pretty/I32_FINISHED_U153.kicad_mod`
- `docs/engineering/rvb22/current/i32_sourced_manufacturing/editable_source/cad/libraries/RevB.pretty/I32_PROCUREMENT_C152.kicad_mod`
- `docs/engineering/rvb22/current/i32_sourced_manufacturing/editable_source/cad/libraries/RevB.pretty/I32_PROCUREMENT_C154.kicad_mod`
- `docs/engineering/rvb22/current/i32_sourced_manufacturing/editable_source/cad/libraries/RevB.pretty/I32_PROCUREMENT_C165.kicad_mod`
- `docs/engineering/rvb22/current/i32_sourced_manufacturing/editable_source/cad/libraries/RevB.pretty/I32_PROCUREMENT_L121.kicad_mod`
- `docs/engineering/rvb22/current/i32_sourced_manufacturing/editable_source/cad/libraries/RevB.pretty/I32_PROCUREMENT_R155.kicad_mod`
- `docs/engineering/rvb22/current/i32_sourced_manufacturing/editable_source/cad/libraries/RevB.pretty/I32_PROCUREMENT_R156.kicad_mod`
- `docs/engineering/rvb22/current/i32_sourced_manufacturing/editable_source/cad/libraries/RevB.pretty/I32_PROCUREMENT_R160.kicad_mod`
- `docs/engineering/rvb22/current/i32_sourced_manufacturing/editable_source/cad/libraries/RevB.pretty/I32_PROCUREMENT_R161.kicad_mod`
- `docs/engineering/rvb22/current/i32_sourced_manufacturing/editable_source/cad/libraries/RevB.pretty/I32_PROCUREMENT_R162.kicad_mod`
- `docs/engineering/rvb22/current/i32_sourced_manufacturing/editable_source/cad/libraries/RevB.pretty/I32_PROCUREMENT_R163.kicad_mod`
- `docs/engineering/rvb22/current/i32_sourced_manufacturing/editable_source/cad/libraries/RevB.pretty/I32_PROCUREMENT_R169.kicad_mod`
- `docs/engineering/rvb22/current/i32_sourced_manufacturing/editable_source/cad/libraries/RevB.pretty/I32_PROCUREMENT_R170.kicad_mod`
- `docs/engineering/rvb22/current/i32_sourced_manufacturing/editable_source/cad/libraries/RevB.pretty/I32_PROCUREMENT_U101.kicad_mod`
- `docs/engineering/rvb22/current/i32_sourced_manufacturing/editable_source/cad/libraries/RevB.pretty/KEMET_C1210_10u50V.kicad_mod`
- `docs/engineering/rvb22/current/i32_sourced_manufacturing/editable_source/cad/libraries/RevB.pretty/KEMET_T598_X_7343_Median.kicad_mod`
- `docs/engineering/rvb22/current/i32_sourced_manufacturing/editable_source/cad/libraries/RevB.pretty/KEMET_T598_X_7343_Median_RVB22_C206.kicad_mod`
- `docs/engineering/rvb22/current/i32_sourced_manufacturing/editable_source/cad/libraries/RevB.pretty/LED_0603_1608Metric.kicad_mod`
- `docs/engineering/rvb22/current/i32_sourced_manufacturing/editable_source/cad/libraries/RevB.pretty/L_Coilcraft_XAL5030-XXX.kicad_mod`
- `docs/engineering/rvb22/current/i32_sourced_manufacturing/editable_source/cad/libraries/RevB.pretty/MSOP-8_3x3mm_P0.65mm.kicad_mod`
- `docs/engineering/rvb22/current/i32_sourced_manufacturing/editable_source/cad/libraries/RevB.pretty/Molex_Micro-Fit_3.0_43045-1200_2x06_P3.00mm_Horizontal.kicad_mod`
- `docs/engineering/rvb22/current/i32_sourced_manufacturing/editable_source/cad/libraries/RevB.pretty/Molex_Micro-Fit_3.0_43045-1200_2x06_P3.00mm_Horizontal_RVB22_F1.kicad_mod`
- `docs/engineering/rvb22/current/i32_sourced_manufacturing/editable_source/cad/libraries/RevB.pretty/MountingHole_4.4mm_Outboard.kicad_mod`
- `docs/engineering/rvb22/current/i32_sourced_manufacturing/editable_source/cad/libraries/RevB.pretty/Murata_LQW18AS_1608.kicad_mod`
- `docs/engineering/rvb22/current/i32_sourced_manufacturing/editable_source/cad/libraries/RevB.pretty/Nexperia_SOD323_PMEG2010BEA.kicad_mod`
- `docs/engineering/rvb22/current/i32_sourced_manufacturing/editable_source/cad/libraries/RevB.pretty/PinHeader_1x02_P2.54mm_Vertical.kicad_mod`
- `docs/engineering/rvb22/current/i32_sourced_manufacturing/editable_source/cad/libraries/RevB.pretty/R_0603_1608Metric.kicad_mod`
- `docs/engineering/rvb22/current/i32_sourced_manufacturing/editable_source/cad/libraries/RevB.pretty/R_0603_1608Metric_RVB22_R155.kicad_mod`
- `docs/engineering/rvb22/current/i32_sourced_manufacturing/editable_source/cad/libraries/RevB.pretty/R_0603_1608Metric_RVB22_R156.kicad_mod`
- `docs/engineering/rvb22/current/i32_sourced_manufacturing/editable_source/cad/libraries/RevB.pretty/R_0603_1608Metric_RVB22_R157.kicad_mod`
- `docs/engineering/rvb22/current/i32_sourced_manufacturing/editable_source/cad/libraries/RevB.pretty/R_0603_1608Metric_RVB22_R203.kicad_mod`
- `docs/engineering/rvb22/current/i32_sourced_manufacturing/editable_source/cad/libraries/RevB.pretty/R_0805_2012Metric.kicad_mod`
- `docs/engineering/rvb22/current/i32_sourced_manufacturing/editable_source/cad/libraries/RevB.pretty/R_1206_3216Metric.kicad_mod`
- `docs/engineering/rvb22/current/i32_sourced_manufacturing/editable_source/cad/libraries/RevB.pretty/R_2512_6332Metric.kicad_mod`
- `docs/engineering/rvb22/current/i32_sourced_manufacturing/editable_source/cad/libraries/RevB.pretty/SOIC-8_3.9x4.9mm_P1.27mm.kicad_mod`
- `docs/engineering/rvb22/current/i32_sourced_manufacturing/editable_source/cad/libraries/RevB.pretty/SOT-23-5.kicad_mod`
- `docs/engineering/rvb22/current/i32_sourced_manufacturing/editable_source/cad/libraries/RevB.pretty/SOT-23.kicad_mod`
- `docs/engineering/rvb22/current/i32_sourced_manufacturing/editable_source/cad/libraries/RevB.pretty/SolderJumper-2_P1.3mm_Open_Pad1.0x1.5mm.kicad_mod`
- `docs/engineering/rvb22/current/i32_sourced_manufacturing/editable_source/cad/libraries/RevB.pretty/TDK_CGA4J1_33N_I32.kicad_mod`
- `docs/engineering/rvb22/current/i32_sourced_manufacturing/editable_source/cad/libraries/RevB.pretty/TI_DDA0008B_4214849B.kicad_mod`
- `docs/engineering/rvb22/current/i32_sourced_manufacturing/editable_source/cad/libraries/RevB.pretty/TI_DPY0002A_TPD1E05U06_SMDMask.kicad_mod`
- `docs/engineering/rvb22/current/i32_sourced_manufacturing/editable_source/cad/libraries/RevB.pretty/TI_DQC0010A_I32.kicad_mod`
- `docs/engineering/rvb22/current/i32_sourced_manufacturing/editable_source/cad/libraries/RevB.pretty/TI_DRB0008J_TCAN3403.kicad_mod`
- `docs/engineering/rvb22/current/i32_sourced_manufacturing/editable_source/cad/libraries/RevB.pretty/TI_PWP0016A_TPS2660.kicad_mod`
- `docs/engineering/rvb22/current/i32_sourced_manufacturing/editable_source/cad/libraries/RevB.pretty/TO-252-2.kicad_mod`
- `docs/engineering/rvb22/current/i32_sourced_manufacturing/editable_source/cad/libraries/RevB.pretty/TPS3808_DBV0006A.kicad_mod`
- `docs/engineering/rvb22/current/i32_sourced_manufacturing/editable_source/cad/libraries/RevB.pretty/Tag-Connect_TC2030-IDC-NL_2x03_P1.27mm_Vertical.kicad_mod`
- `docs/engineering/rvb22/current/i32_sourced_manufacturing/editable_source/cad/libraries/RevB.pretty/TestPoint_Pad_D1.5mm.kicad_mod`
- `docs/engineering/rvb22/current/i32_sourced_manufacturing/editable_source/cad/libraries/RevB.pretty/U.FL_Hirose_U.FL-R-SMT-1_Vertical.kicad_mod`
- `docs/engineering/rvb22/current/i32_sourced_manufacturing/editable_source/cad/libraries/RevB.pretty/VSSOP-8_2.3x2mm_P0.5mm.kicad_mod`
- `docs/engineering/rvb22/current/i32_sourced_manufacturing/editable_source/cad/libraries/RevB.pretty/WSLP0603_MANUFACTURER.kicad_mod`
- `docs/engineering/rvb22/current/i32_sourced_manufacturing/editable_source/cad/libraries/RevB.pretty/WSLP0603_MANUFACTURER_R153.kicad_mod`
- `docs/engineering/rvb22/current/i32_sourced_manufacturing/editable_source/cad/libraries/RevB.pretty/Wurth_61300211121_1x02.kicad_mod`
- `docs/engineering/rvb22/current/i32_sourced_manufacturing/editable_source/cad/models/ENVELOPE_CDTop_PA1616D_20Pad_v06.step`
- `docs/engineering/rvb22/current/i32_sourced_manufacturing/editable_source/cad/models/ENVELOPE_C_0603_1608Metric_RVB22_C205.step`
- `docs/engineering/rvb22/current/i32_sourced_manufacturing/editable_source/cad/models/ENVELOPE_Coilcraft_MSS1246T_12x12_RVB22_L121.step`
- `docs/engineering/rvb22/current/i32_sourced_manufacturing/editable_source/cad/models/ENVELOPE_Fuse_Littelfuse-NANO2-885.step`
- `docs/engineering/rvb22/current/i32_sourced_manufacturing/editable_source/cad/models/ENVELOPE_HTSSOP-16-1EP_4.4x5mm_P0.65mm_EP3.4x5mm_Mask2.46x2.31mm_RVB22_U151.step`
- `docs/engineering/rvb22/current/i32_sourced_manufacturing/editable_source/cad/models/ENVELOPE_I32_PROCUREMENT_L121.step`
- `docs/engineering/rvb22/current/i32_sourced_manufacturing/editable_source/cad/models/ENVELOPE_I32_PROCUREMENT_R155.step`
- `docs/engineering/rvb22/current/i32_sourced_manufacturing/editable_source/cad/models/ENVELOPE_I32_PROCUREMENT_R156.step`
- `docs/engineering/rvb22/current/i32_sourced_manufacturing/editable_source/cad/models/ENVELOPE_I32_PROCUREMENT_R160.step`
- `docs/engineering/rvb22/current/i32_sourced_manufacturing/editable_source/cad/models/ENVELOPE_I32_PROCUREMENT_R161.step`
- `docs/engineering/rvb22/current/i32_sourced_manufacturing/editable_source/cad/models/ENVELOPE_I32_PROCUREMENT_R162.step`
- `docs/engineering/rvb22/current/i32_sourced_manufacturing/editable_source/cad/models/ENVELOPE_I32_PROCUREMENT_R163.step`
- `docs/engineering/rvb22/current/i32_sourced_manufacturing/editable_source/cad/models/ENVELOPE_I32_PROCUREMENT_R169.step`
- `docs/engineering/rvb22/current/i32_sourced_manufacturing/editable_source/cad/models/ENVELOPE_I32_PROCUREMENT_R170.step`
- `docs/engineering/rvb22/current/i32_sourced_manufacturing/editable_source/cad/models/ENVELOPE_KEMET_C1210_10u50V.step`
- `docs/engineering/rvb22/current/i32_sourced_manufacturing/editable_source/cad/models/ENVELOPE_KEMET_T598_X_7343_Median_RVB22_C206.step`
- `docs/engineering/rvb22/current/i32_sourced_manufacturing/editable_source/cad/models/ENVELOPE_Molex_Micro-Fit_3.0_43045-1200_2x06_P3.00mm_Horizontal_RVB22_F1.step`
- `docs/engineering/rvb22/current/i32_sourced_manufacturing/editable_source/cad/models/ENVELOPE_Murata_LQW18AS_1608.step`
- `docs/engineering/rvb22/current/i32_sourced_manufacturing/editable_source/cad/models/ENVELOPE_R_0603_1608Metric_RVB22_R155.step`
- `docs/engineering/rvb22/current/i32_sourced_manufacturing/editable_source/cad/models/ENVELOPE_R_0603_1608Metric_RVB22_R156.step`
- `docs/engineering/rvb22/current/i32_sourced_manufacturing/editable_source/cad/models/ENVELOPE_R_0603_1608Metric_RVB22_R157.step`
- `docs/engineering/rvb22/current/i32_sourced_manufacturing/editable_source/cad/models/ENVELOPE_R_0603_1608Metric_RVB22_R203.step`
- `docs/engineering/rvb22/current/i32_sourced_manufacturing/editable_source/cad/models/ENVELOPE_TDK_CGA4J1_33N_I32.step`
- `docs/engineering/rvb22/current/i32_sourced_manufacturing/editable_source/cad/models/ENVELOPE_TDK_CGA5L1_68N_I32.step`
- `docs/engineering/rvb22/current/i32_sourced_manufacturing/editable_source/cad/models/ENVELOPE_TI_DDA0008B_4214849B.step`
- `docs/engineering/rvb22/current/i32_sourced_manufacturing/editable_source/cad/models/ENVELOPE_TI_DPY0002A_TPD1E05U06_SMDMask.step`
- `docs/engineering/rvb22/current/i32_sourced_manufacturing/editable_source/cad/models/ENVELOPE_TI_DQC0010A_I32.step`
- `docs/engineering/rvb22/current/i32_sourced_manufacturing/editable_source/cad/models/ENVELOPE_TI_DRB0008J_TCAN3403.step`
- `docs/engineering/rvb22/current/i32_sourced_manufacturing/editable_source/cad/models/ENVELOPE_TI_PWP0016A_TPS2660.step`
- `docs/engineering/rvb22/current/i32_sourced_manufacturing/editable_source/cad/models/ENVELOPE_TPS3808_DBV0006A.step`
- `docs/engineering/rvb22/current/i32_sourced_manufacturing/editable_source/cad/models/ENVELOPE_WSL2512_I32_R158.step`
- `docs/engineering/rvb22/current/i32_sourced_manufacturing/editable_source/cad/models/ENVELOPE_WSLP0603_MANUFACTURER.step`
- `docs/engineering/rvb22/current/i32_sourced_manufacturing/editable_source/cad/models/ENVELOPE_WSLP0603_MANUFACTURER_R153.step`
- `docs/engineering/rvb22/current/i32_sourced_manufacturing/editable_source/cad/sym-lib-table`
- `docs/engineering/rvb22/current/i32_sourced_manufacturing/fabrication/FILL_CAP_PLANARIZE_49_VIAS.csv`
- `docs/engineering/rvb22/current/i32_sourced_manufacturing/fabrication/JLCPCB_GERBERS.zip`
- `docs/engineering/rvb22/current/i32_sourced_manufacturing/fabrication/PCB_NETLIST.d356`
- `docs/engineering/rvb22/current/i32_sourced_manufacturing/fabrication/STACKUP_AND_PROCESS.json`
- `docs/engineering/rvb22/current/i32_sourced_manufacturing/fabrication/gerbers/GR86_CCA_RevB-B_Cu.gbl`
- `docs/engineering/rvb22/current/i32_sourced_manufacturing/fabrication/gerbers/GR86_CCA_RevB-B_Mask.gbs`
- `docs/engineering/rvb22/current/i32_sourced_manufacturing/fabrication/gerbers/GR86_CCA_RevB-B_Paste.gbp`
- `docs/engineering/rvb22/current/i32_sourced_manufacturing/fabrication/gerbers/GR86_CCA_RevB-B_Silkscreen.gbo`
- `docs/engineering/rvb22/current/i32_sourced_manufacturing/fabrication/gerbers/GR86_CCA_RevB-Edge_Cuts.gm1`
- `docs/engineering/rvb22/current/i32_sourced_manufacturing/fabrication/gerbers/GR86_CCA_RevB-F_Cu.gtl`
- `docs/engineering/rvb22/current/i32_sourced_manufacturing/fabrication/gerbers/GR86_CCA_RevB-F_Mask.gts`
- `docs/engineering/rvb22/current/i32_sourced_manufacturing/fabrication/gerbers/GR86_CCA_RevB-F_Paste.gtp`
- `docs/engineering/rvb22/current/i32_sourced_manufacturing/fabrication/gerbers/GR86_CCA_RevB-F_Silkscreen.gto`
- `docs/engineering/rvb22/current/i32_sourced_manufacturing/fabrication/gerbers/GR86_CCA_RevB-In1_Cu.g1`
- `docs/engineering/rvb22/current/i32_sourced_manufacturing/fabrication/gerbers/GR86_CCA_RevB-In2_Cu.g2`
- `docs/engineering/rvb22/current/i32_sourced_manufacturing/fabrication/gerbers/GR86_CCA_RevB-NPTH.drl`
- `docs/engineering/rvb22/current/i32_sourced_manufacturing/fabrication/gerbers/GR86_CCA_RevB-PTH.drl`
- `docs/engineering/rvb22/current/i32_sourced_manufacturing/fabrication/gerbers/GR86_CCA_RevB-job.gbrjob`
- `docs/engineering/rvb22/current/i32_sourced_manufacturing/sourcing_evidence/catalog/C161212.html.gz`
- `docs/engineering/rvb22/current/i32_sourced_manufacturing/sourcing_evidence/catalog/C161212.json`
- `docs/engineering/rvb22/current/i32_sourced_manufacturing/sourcing_evidence/catalog/C1709453.html.gz`
- `docs/engineering/rvb22/current/i32_sourced_manufacturing/sourcing_evidence/catalog/C1709453.json`
- `docs/engineering/rvb22/current/i32_sourced_manufacturing/sourcing_evidence/catalog/C1709494.html.gz`
- `docs/engineering/rvb22/current/i32_sourced_manufacturing/sourcing_evidence/catalog/C1709494.json`
- `docs/engineering/rvb22/current/i32_sourced_manufacturing/sourcing_evidence/catalog/C1710754.html.gz`
- `docs/engineering/rvb22/current/i32_sourced_manufacturing/sourcing_evidence/catalog/C1710754.json`
- `docs/engineering/rvb22/current/i32_sourced_manufacturing/sourcing_evidence/catalog/C190124.html.gz`
- `docs/engineering/rvb22/current/i32_sourced_manufacturing/sourcing_evidence/catalog/C190124.json`
- `docs/engineering/rvb22/current/i32_sourced_manufacturing/sourcing_evidence/catalog/C19679768.html.gz`
- `docs/engineering/rvb22/current/i32_sourced_manufacturing/sourcing_evidence/catalog/C19679768.json`
- `docs/engineering/rvb22/current/i32_sourced_manufacturing/sourcing_evidence/catalog/C1978408.html.gz`
- `docs/engineering/rvb22/current/i32_sourced_manufacturing/sourcing_evidence/catalog/C1978408.json`
- `docs/engineering/rvb22/current/i32_sourced_manufacturing/sourcing_evidence/catalog/C1981952.html.gz`
- `docs/engineering/rvb22/current/i32_sourced_manufacturing/sourcing_evidence/catalog/C1981952.json`
- `docs/engineering/rvb22/current/i32_sourced_manufacturing/sourcing_evidence/catalog/C1982070.html.gz`
- `docs/engineering/rvb22/current/i32_sourced_manufacturing/sourcing_evidence/catalog/C1982070.json`
- `docs/engineering/rvb22/current/i32_sourced_manufacturing/sourcing_evidence/catalog/C19941093.html.gz`
- `docs/engineering/rvb22/current/i32_sourced_manufacturing/sourcing_evidence/catalog/C19941093.json`
- `docs/engineering/rvb22/current/i32_sourced_manufacturing/sourcing_evidence/catalog/C2072225.html.gz`
- `docs/engineering/rvb22/current/i32_sourced_manufacturing/sourcing_evidence/catalog/C2072225.json`
- `docs/engineering/rvb22/current/i32_sourced_manufacturing/sourcing_evidence/catalog/C2074591.html.gz`
- `docs/engineering/rvb22/current/i32_sourced_manufacturing/sourcing_evidence/catalog/C2074591.json`
- `docs/engineering/rvb22/current/i32_sourced_manufacturing/sourcing_evidence/catalog/C2075852.html.gz`
- `docs/engineering/rvb22/current/i32_sourced_manufacturing/sourcing_evidence/catalog/C2075852.json`
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
- `docs/engineering/rvb22/current/i32_sourced_manufacturing/sourcing_evidence/catalog/C844919.json`
- `docs/engineering/rvb22/current/i32_sourced_manufacturing/sourcing_evidence/catalog/C844920.html.gz`
- `docs/engineering/rvb22/current/i32_sourced_manufacturing/sourcing_evidence/catalog/C844920.json`
- `docs/engineering/rvb22/current/i32_sourced_manufacturing/sourcing_evidence/catalog/C844929.html.gz`
- `docs/engineering/rvb22/current/i32_sourced_manufacturing/sourcing_evidence/catalog/C844929.json`
- `docs/engineering/rvb22/current/i32_sourced_manufacturing/sourcing_evidence/catalog/C844931.html.gz`
- `docs/engineering/rvb22/current/i32_sourced_manufacturing/sourcing_evidence/catalog/C844931.json`
- `docs/engineering/rvb22/current/i32_sourced_manufacturing/sourcing_evidence/catalog/C844933.html.gz`
- `docs/engineering/rvb22/current/i32_sourced_manufacturing/sourcing_evidence/catalog/C844933.json`
- `docs/engineering/rvb22/current/i32_sourced_manufacturing/sourcing_evidence/catalog/C85864.html.gz`
- `docs/engineering/rvb22/current/i32_sourced_manufacturing/sourcing_evidence/catalog/C85864.json`
- `docs/engineering/rvb22/current/i32_sourced_manufacturing/sourcing_evidence/catalog/C85973.html.gz`
- `docs/engineering/rvb22/current/i32_sourced_manufacturing/sourcing_evidence/catalog/C85973.json`
- `docs/engineering/rvb22/current/i32_sourced_manufacturing/sourcing_evidence/catalog/C864499.html.gz`
- `docs/engineering/rvb22/current/i32_sourced_manufacturing/sourcing_evidence/catalog/C864499.json`
- `docs/engineering/rvb22/current/i32_sourced_manufacturing/sourcing_evidence/catalog/C88374.html.gz`
- `docs/engineering/rvb22/current/i32_sourced_manufacturing/sourcing_evidence/catalog/C88374.json`
- `docs/engineering/rvb22/current/i32_sourced_manufacturing/sourcing_evidence/catalog/C88419.html.gz`
- `docs/engineering/rvb22/current/i32_sourced_manufacturing/sourcing_evidence/catalog/C88419.json`
- `docs/engineering/rvb22/product/GR86_I32_SOURCED_MANUFACTURING.zip`
