tranquilWorks/gr86-cca-telemetry/docs/engineering/rvb22/analyses/i32/references/CGA5L1C0G2A683J160AE_SOURCE.md

# C166 selected timing capacitor

Manufacturer page checked September14,2026: [TDK CGA5L1C0G2A683J160AE](https://product.tdk.com/en/search/capacitor/ceramic/mlcc/info?part_no=CGA5L1C0G2A683J160AE). Production, automotive AEC-Q200, soft termination. This is a factual extraction, not an archived original manufacturer PDF.

68nF, tolerance5%,100V,C0G0±30ppm/K,-55..125C. Body maxima3.60mm long,1.90mm wide,1.90mm high (nominal3.2x1.6x1.6). Minimum terminal width.20mm and terminal separation1.00mm. Reflow land recommendations PA2.00..2.40mm,PB1.00..1.20mm,PC1.10..1.60mm. Adopted PA2.20,PB1.10,PC1.50mm; pad centers±1.65mm. Source Fab/STEP represents maximum body; courtyard2.45x1.20mm half-extents.

Insulation resistance minimum7352Mohm; Qminimum1000. Vendor plots are typical reference characteristics. Sourcing and exact delivery specification confirmation remain supplier gates; search-index stock is not a purchasing commitment.
