tranquilWorks/gr86-cca-telemetry/docs/engineering/rvb22/analyses/i32/evidence/runs/vendor_closed_cascade_ng47/SIMULATOR_VERSION.txt

******
** ngspice-47 : Circuit level simulation program
** Compiled with KLU Direct Linear Solver
** The U. C. Berkeley CAD Group
** Copyright 1985-1994, Regents of the University of California.
** Copyright 2001-2026, The ngspice team.
** Please get your ngspice manual from https://ngspice.sourceforge.io/docs.html
** Please file your bug-reports at http://ngspice.sourceforge.net/bugrep.html
** Creation Date: Sun Sep 13 20:23:02 UTC 2026
******
