tranquilWorks/gr86-cca-telemetry/docs/engineering/rvb22/analyses/i32/procurement_redline/filled_returns/Ground_returns.png

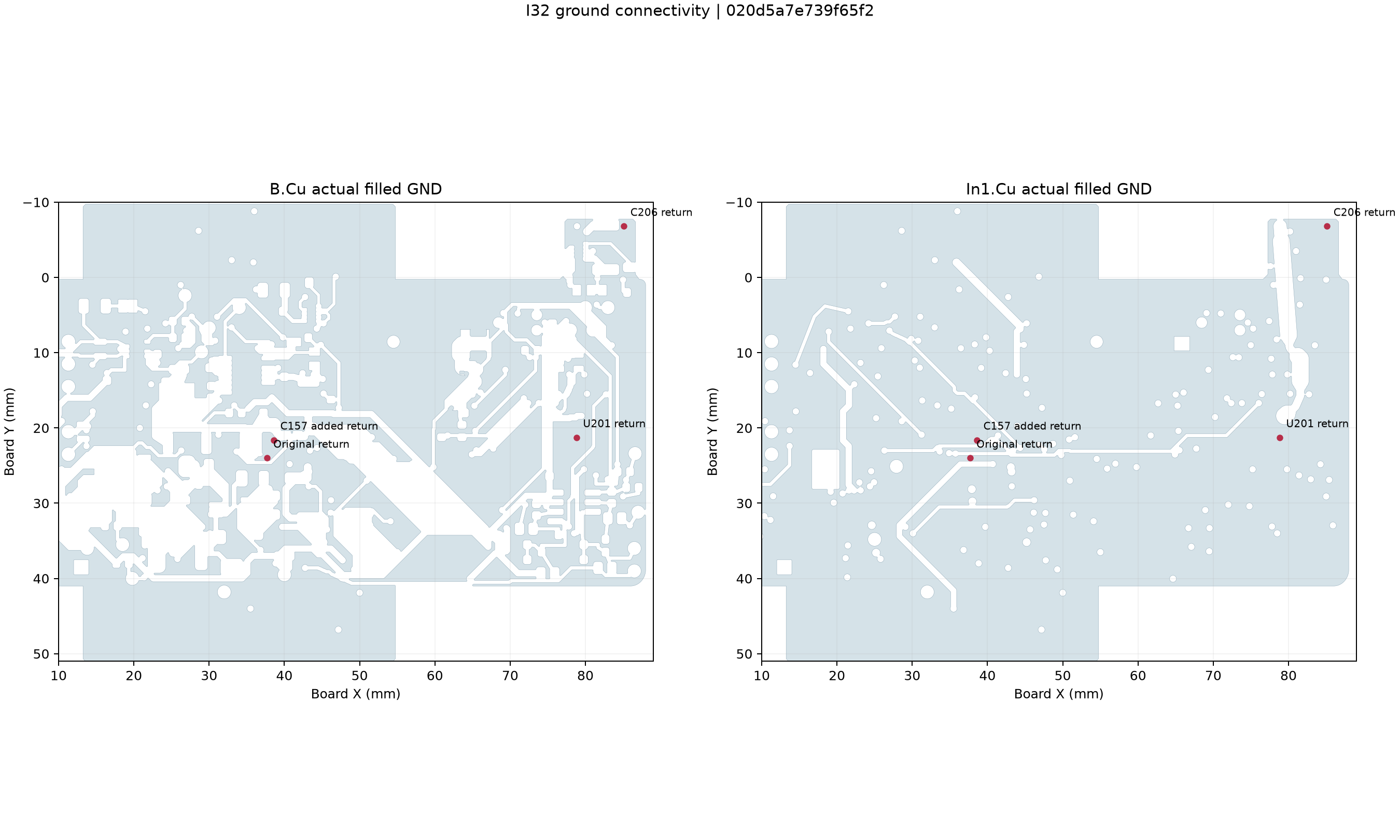
docs/engineering/rvb22/analyses/i32/procurement_redline/filled_returns/Ground_returns.png
