tranquilWorks/gr86-cca-telemetry/docs/engineering/rvb22/analyses/i32/procurement_redline/layout/Input_power_routes.png

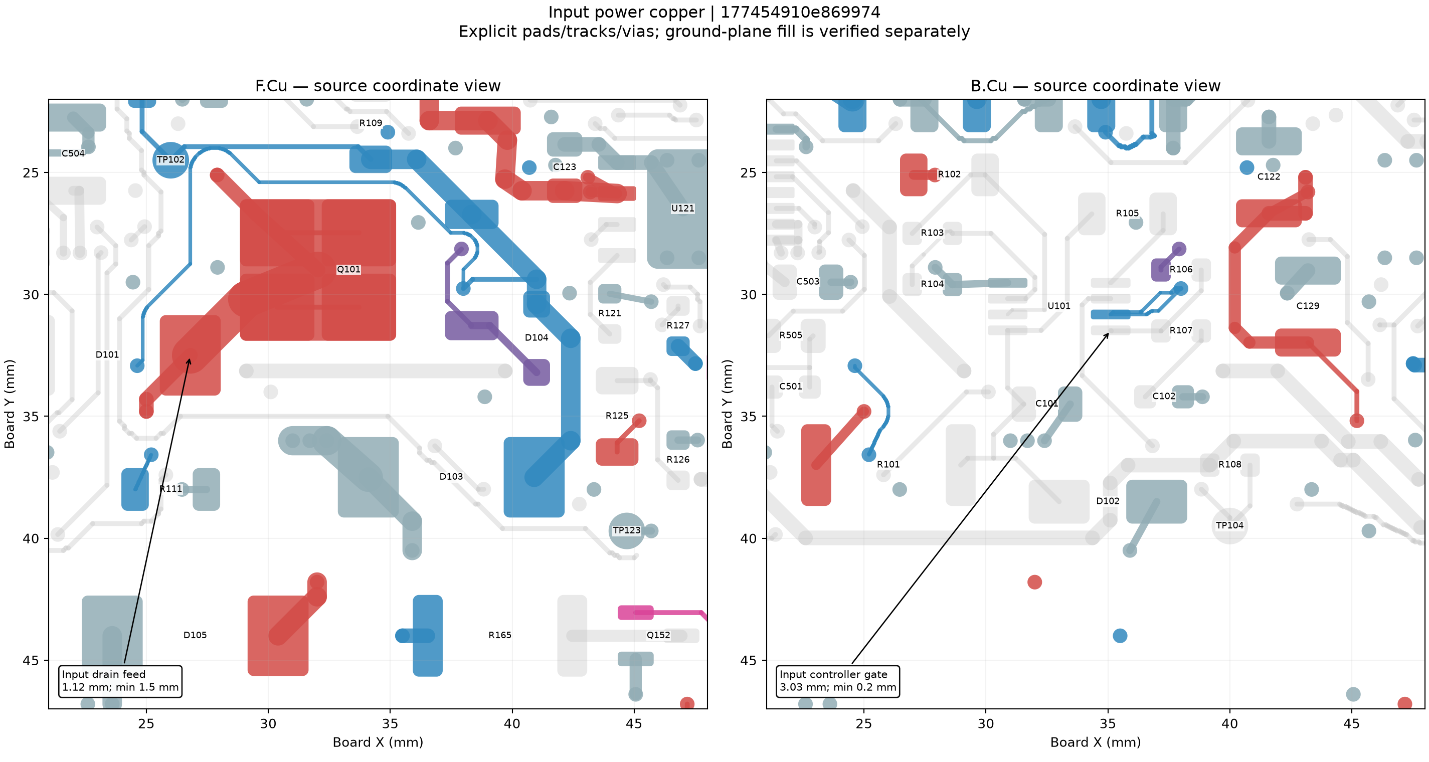
docs/engineering/rvb22/analyses/i32/procurement_redline/layout/Input_power_routes.png
