tranquilWorks/gr86-cca-telemetry/docs/engineering/rvb22/analyses/i32/procurement_redline/layout/Reset_delay_power_routes.png

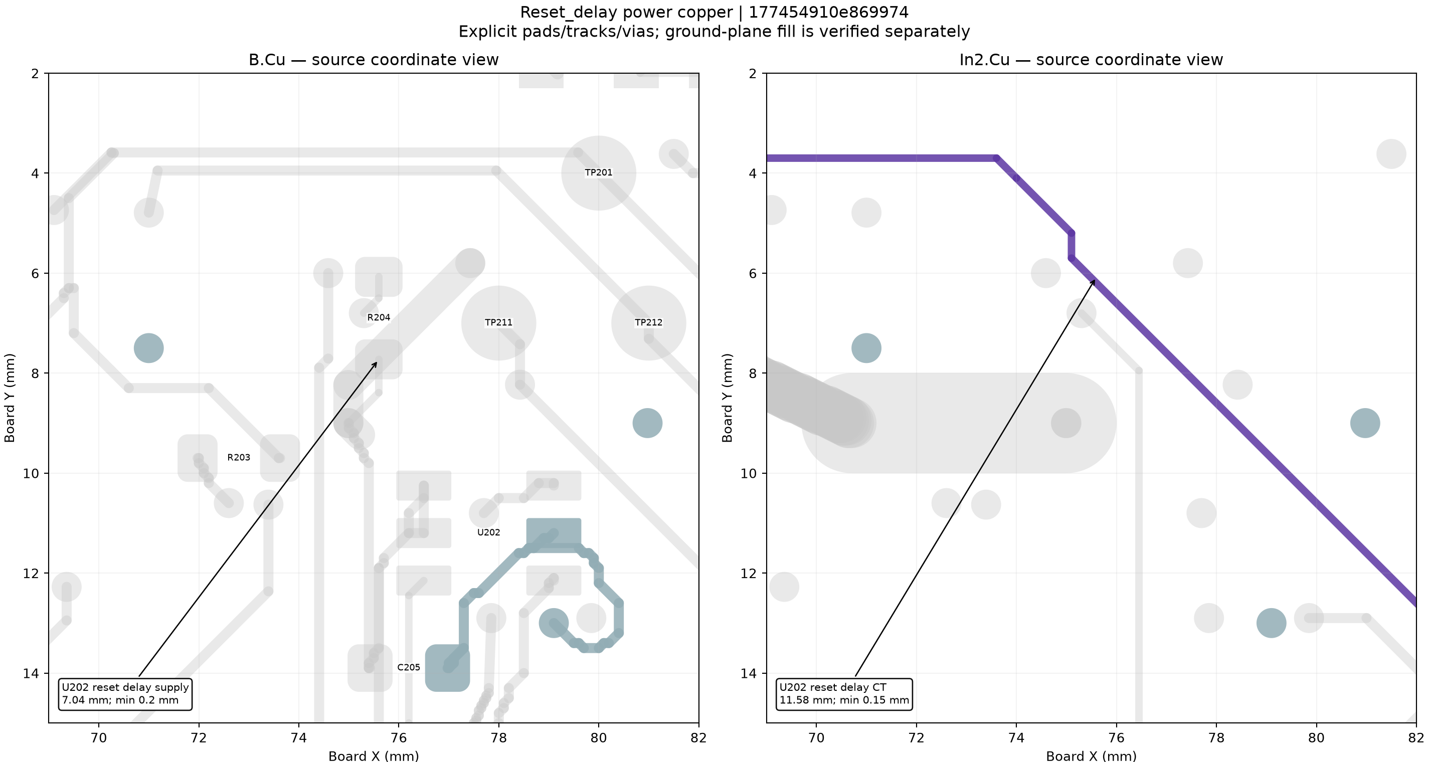
docs/engineering/rvb22/analyses/i32/procurement_redline/layout/Reset_delay_power_routes.png
