tranquilWorks/gr86-cca-telemetry/docs/engineering/rvb22/analyses/i32/procurement_redline/review_register/before.png

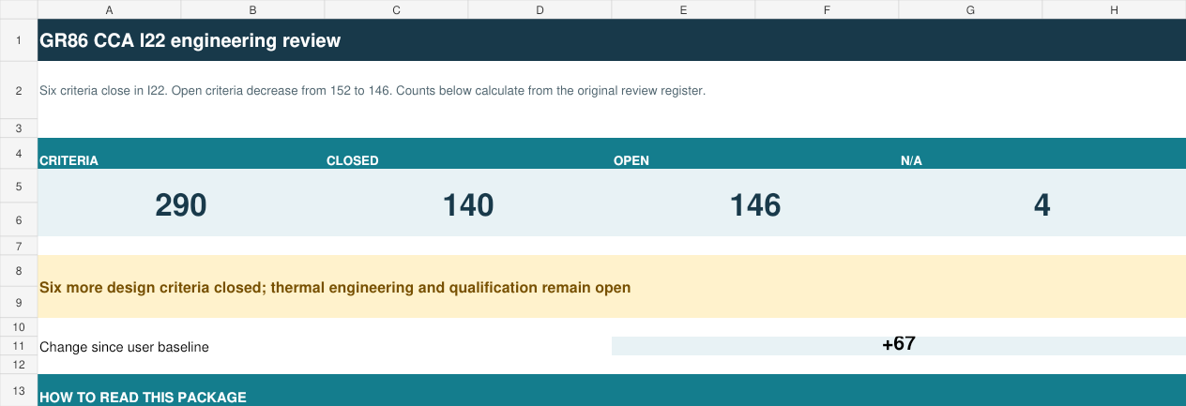
docs/engineering/rvb22/analyses/i32/procurement_redline/review_register/before.png
