tranquilWorks/gr86-cca-telemetry/docs/engineering/rvb22/analyses/i32/procurement_completion/native/candidate_kicad/models/ENVELOPE_CDTop_PA1616D_20Pad_v06.step

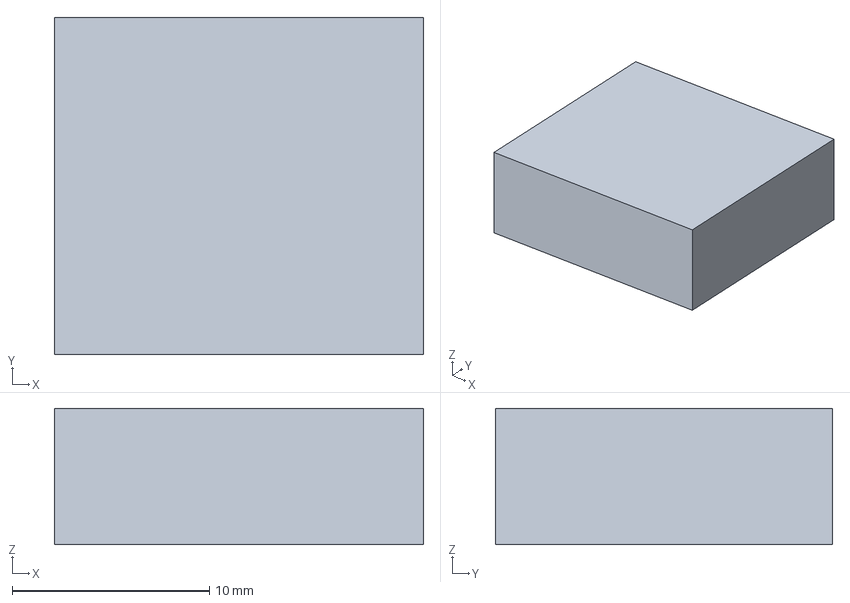
[picture p15: CAD file, 2026-09-14]
docs/engineering/rvb22/analyses/i32/procurement_completion/native/candidate_kicad/models/ENVELOPE_CDTop_PA1616D_20Pad_v06.step
18.7 x 17.1 x 6.90 mm
