tranquilWorks/gr86-cca-telemetry/docs/engineering/rvb22/current/i32_sourced_manufacturing/editable_source/cad/models/ENVELOPE_KEMET_T598_X_7343_Median_RVB22_C206.step

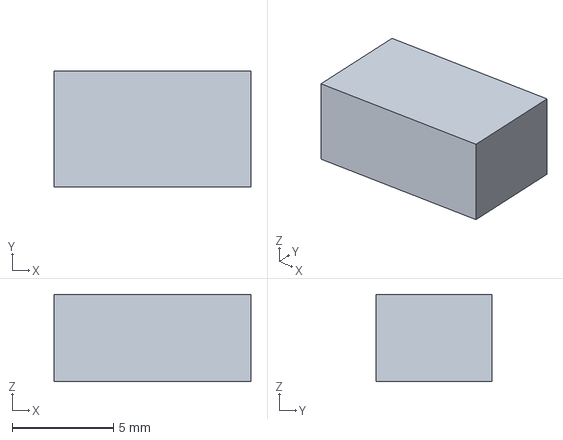
[picture p16: CAD file, 2026-09-14]
docs/engineering/rvb22/current/i32_sourced_manufacturing/editable_source/cad/models/ENVELOPE_KEMET_T598_X_7343_Median_RVB22_C206.step
9.72 x 5.70 x 4.30 mm
