tranquilWorks/gr86-cca-telemetry/docs/engineering/rvb22/analyses/i32/procurement_completion/native/candidate_kicad/models/ENVELOPE_TI_DQC0010A_I32.step

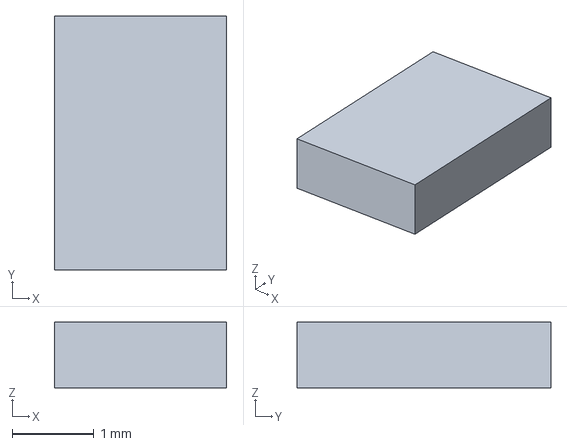
[picture p17: CAD file, 2026-09-14]
docs/engineering/rvb22/analyses/i32/procurement_completion/native/candidate_kicad/models/ENVELOPE_TI_DQC0010A_I32.step
2.10 x 3.10 x 0.8 mm
