tranquilWorks/gr86-cca-telemetry/docs/engineering/rvb22/current/i32_sourced_manufacturing/editable_source/cad/models/ENVELOPE_TI_DRB0008J_TCAN3403.step

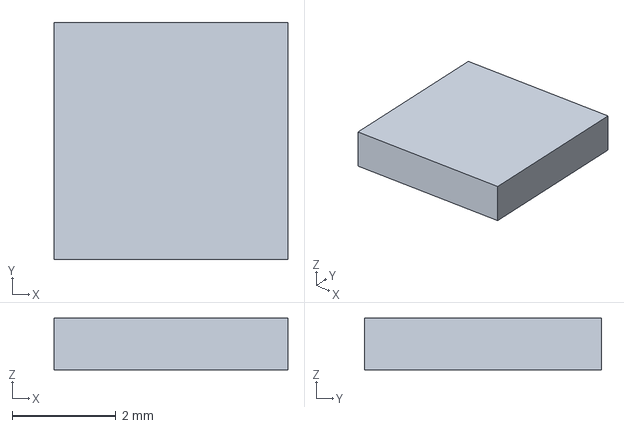
[picture p18: CAD file, 2026-09-14]
docs/engineering/rvb22/current/i32_sourced_manufacturing/editable_source/cad/models/ENVELOPE_TI_DRB0008J_TCAN3403.step
4.50 x 4.55 x 1.00 mm
