tranquilWorks/gr86-cca-telemetry/docs/engineering/rvb22/analyses/i32/procurement_completion/native/candidate_kicad/models/ENVELOPE_TDK_CGA5L1_68N_I32.step

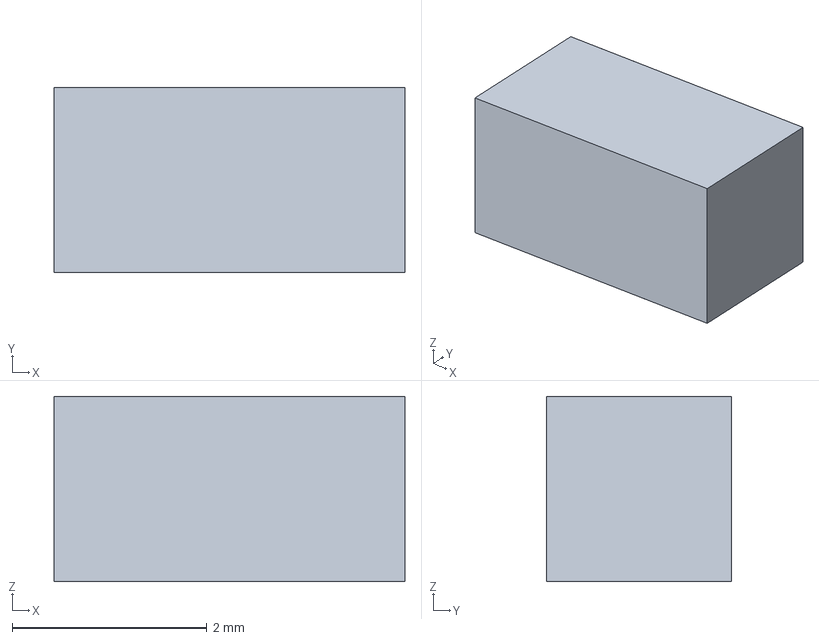
[picture p19: CAD file, 2026-09-14]
docs/engineering/rvb22/analyses/i32/procurement_completion/native/candidate_kicad/models/ENVELOPE_TDK_CGA5L1_68N_I32.step
3.60 x 1.90 x 1.90 mm
