tranquilWorks/gr86-cca-telemetry/docs/engineering/rvb22/current/i32_sourced_manufacturing/editable_source/cad/models/ENVELOPE_R_0603_1608Metric_RVB22_R157.step

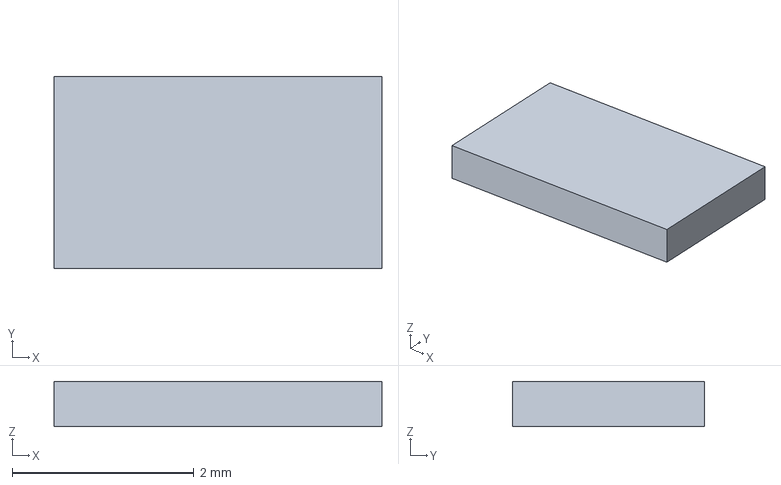
[picture p20: CAD file, 2026-09-14]
docs/engineering/rvb22/current/i32_sourced_manufacturing/editable_source/cad/models/ENVELOPE_R_0603_1608Metric_RVB22_R157.step
3.61 x 2.11 x 0.5 mm
