tranquilWorks/gr86-cca-telemetry/docs/engineering/rvb22/analyses/i32/procurement_completion/native/candidate_kicad/models/ENVELOPE_TI_DPY0002A_TPD1E05U06_SMDMask.step

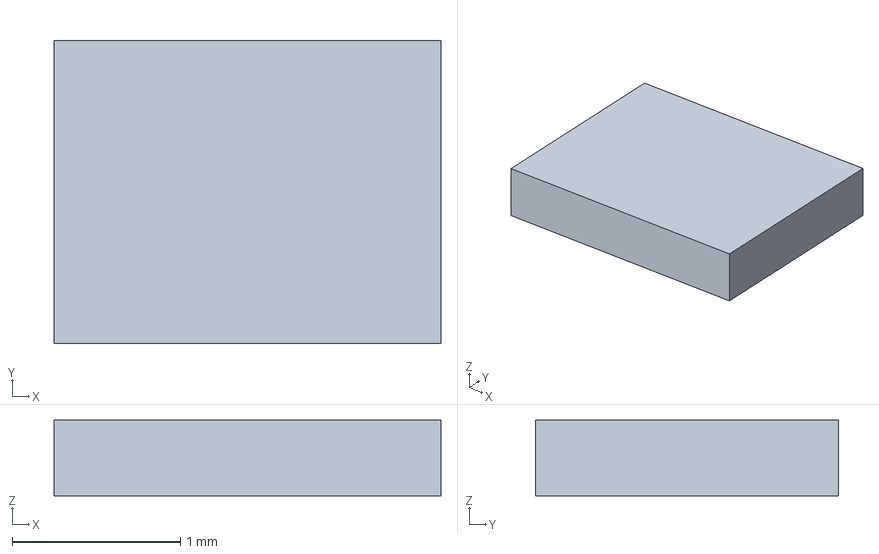
[picture p21: CAD file, 2026-09-14]
docs/engineering/rvb22/analyses/i32/procurement_completion/native/candidate_kicad/models/ENVELOPE_TI_DPY0002A_TPD1E05U06_SMDMask.step
2.30 x 1.80 x 0.45 mm
