tranquilWorks/gr86-cca-telemetry/docs/engineering/rvb22/current/i32_sourced_manufacturing/editable_source/cad/models/ENVELOPE_WSLP0603_MANUFACTURER_R153.step

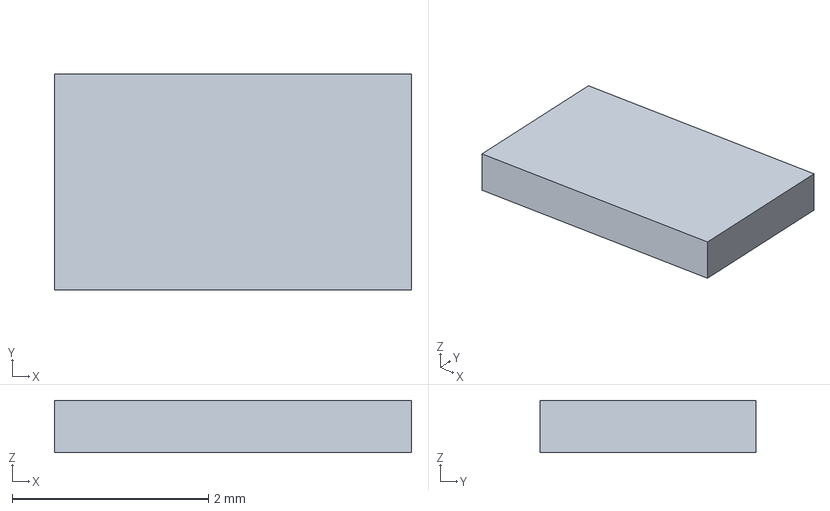
[picture p22: CAD file, 2026-09-14]
docs/engineering/rvb22/current/i32_sourced_manufacturing/editable_source/cad/models/ENVELOPE_WSLP0603_MANUFACTURER_R153.step
3.64 x 2.20 x 0.533 mm
