tranquilWorks/gr86-cca-telemetry/docs/engineering/rvb22/analyses/i32/procurement_completion/native/candidate_kicad/models/ENVELOPE_WSL2512_I32_R158.step

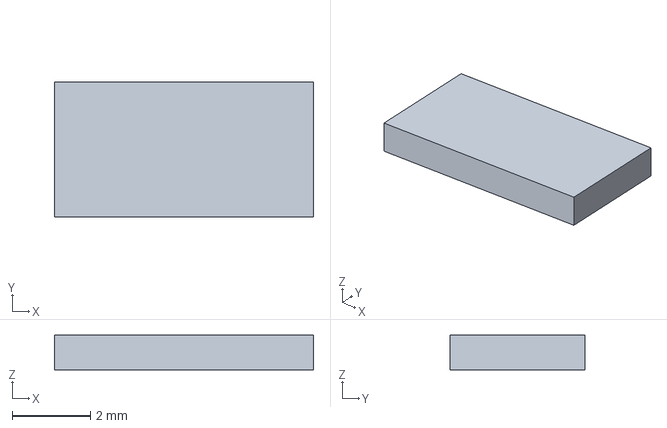
[picture p23: CAD file, 2026-09-14]
docs/engineering/rvb22/analyses/i32/procurement_completion/native/candidate_kicad/models/ENVELOPE_WSL2512_I32_R158.step
6.60 x 3.43 x 0.889 mm
