tranquilWorks/gr86-cca-telemetry/docs/engineering/rvb22/current/i32_sourced_manufacturing/editable_source/cad/models/ENVELOPE_KEMET_C1210_10u50V.step

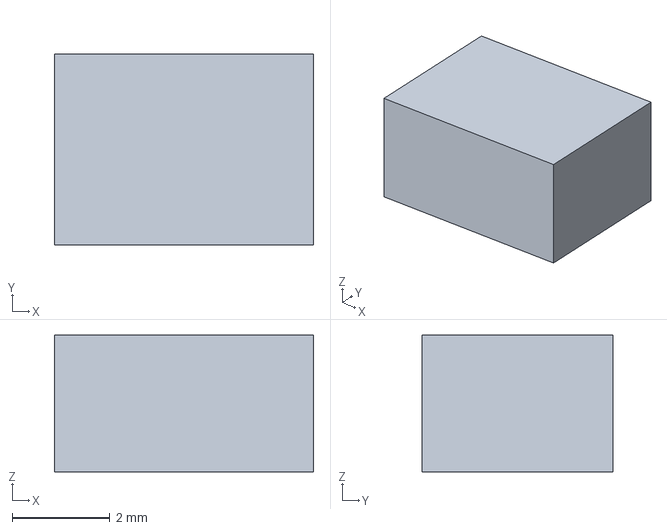
[picture p24: CAD file, 2026-09-14]
docs/engineering/rvb22/current/i32_sourced_manufacturing/editable_source/cad/models/ENVELOPE_KEMET_C1210_10u50V.step
5.30 x 3.90 x 2.80 mm
