tranquilWorks/gr86-cca-telemetry/docs/engineering/rvb22/analyses/i32/procurement_completion/native/candidate_kicad/models/ENVELOPE_R_0603_1608Metric_RVB22_R155.step

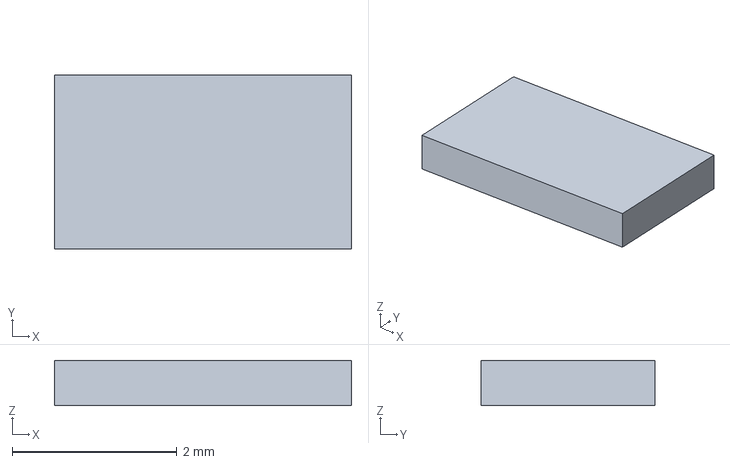
[picture p25: CAD file, 2026-09-14]
docs/engineering/rvb22/analyses/i32/procurement_completion/native/candidate_kicad/models/ENVELOPE_R_0603_1608Metric_RVB22_R155.step
3.61 x 2.11 x 0.55 mm
