tranquilWorks/gr86-cca-telemetry/docs/engineering/rvb22/current/i32_sourced_manufacturing/editable_source/cad/models/ENVELOPE_Fuse_Littelfuse-NANO2-885.step

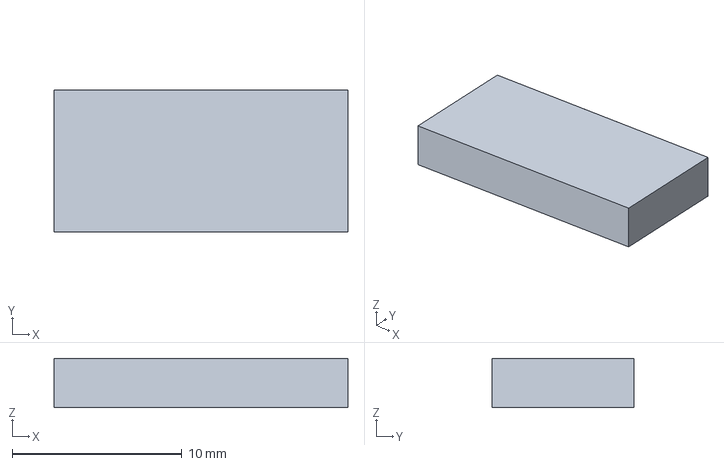
[picture p27: CAD file, 2026-09-14]
docs/engineering/rvb22/current/i32_sourced_manufacturing/editable_source/cad/models/ENVELOPE_Fuse_Littelfuse-NANO2-885.step
17.3 x 8.36 x 2.90 mm
