tranquilWorks/gr86-cca-telemetry/docs/engineering/rvb22/analyses/i32/procurement_completion/native/candidate_kicad/models/ENVELOPE_Coilcraft_MSS1246T_12x12_RVB22_L121.step

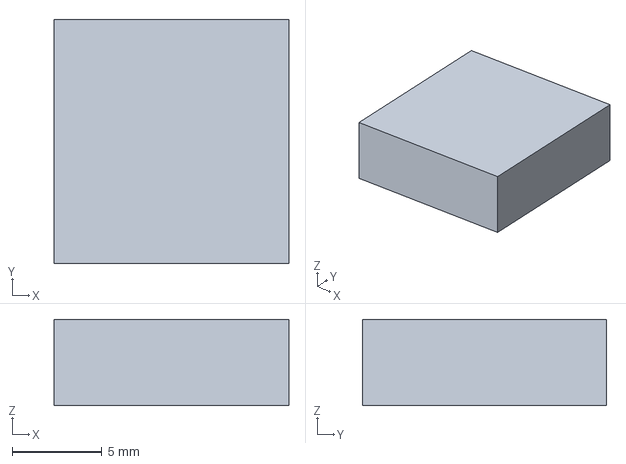
[picture p28: CAD file, 2026-09-14]
docs/engineering/rvb22/analyses/i32/procurement_completion/native/candidate_kicad/models/ENVELOPE_Coilcraft_MSS1246T_12x12_RVB22_L121.step
13.1 x 13.6 x 4.80 mm
