tranquilWorks/gr86-cca-telemetry/docs/engineering/rvb22/analyses/i32/procurement_completion/native/candidate_kicad/models/ENVELOPE_TPS3808_DBV0006A.step

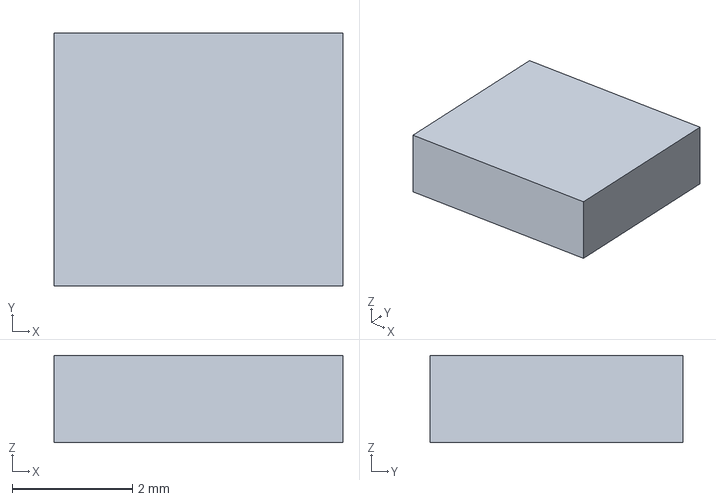
[picture p31: CAD file, 2026-09-14]
docs/engineering/rvb22/analyses/i32/procurement_completion/native/candidate_kicad/models/ENVELOPE_TPS3808_DBV0006A.step
4.80 x 4.20 x 1.45 mm
