tranquilWorks/gr86-cca-telemetry/docs/engineering/rvb22/current/i32_sourced_manufacturing/editable_source/cad/models/ENVELOPE_WSLP0603_MANUFACTURER.step

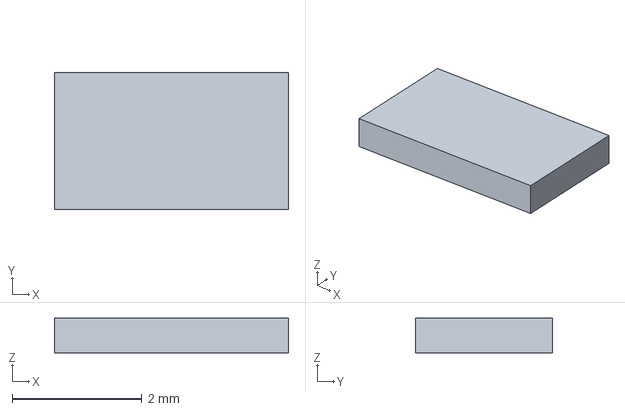
[picture p32: CAD file, 2026-09-14]
docs/engineering/rvb22/current/i32_sourced_manufacturing/editable_source/cad/models/ENVELOPE_WSLP0603_MANUFACTURER.step
3.61 x 2.11 x 0.533 mm
