tranquilWorks/gr86-cca-telemetry/docs/engineering/rvb22/analyses/i32/procurement_completion/native/candidate_kicad/models/ENVELOPE_Murata_LQW18AS_1608.step

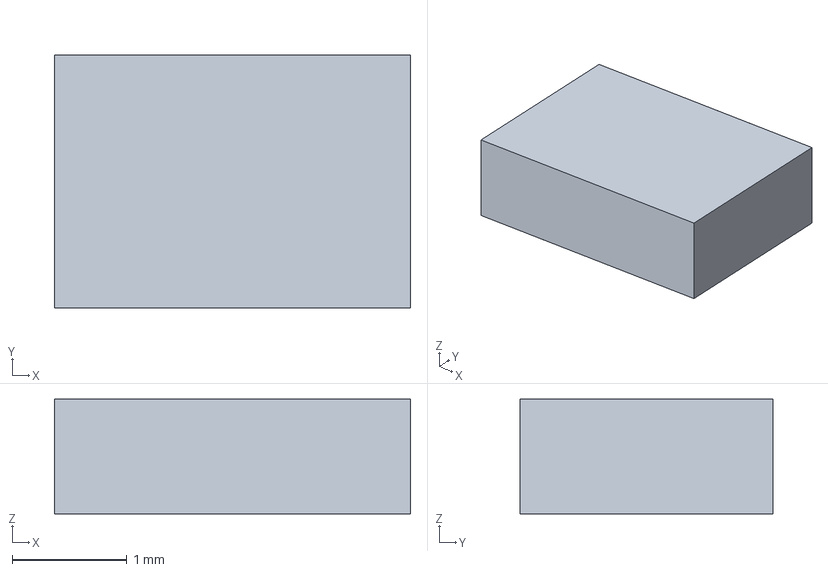
[picture p33: CAD file, 2026-09-14]
docs/engineering/rvb22/analyses/i32/procurement_completion/native/candidate_kicad/models/ENVELOPE_Murata_LQW18AS_1608.step
3.10 x 2.20 x 1.00 mm
