tranquilWorks/gr86-cca-telemetry/docs/engineering/rvb22/analyses/i32/procurement_completion/native/candidate_kicad/models/ENVELOPE_TDK_CGA4J1_33N_I32.step

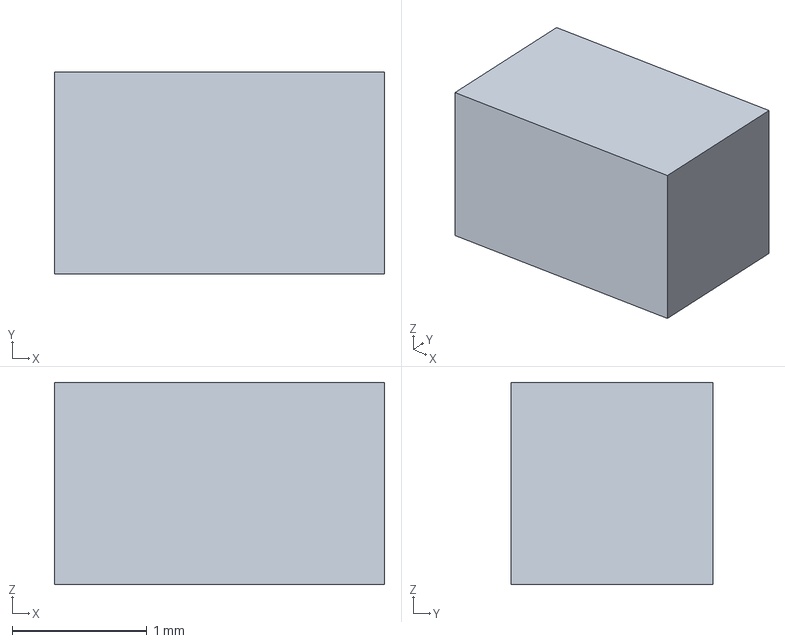
[picture p34: CAD file, 2026-09-14]
docs/engineering/rvb22/analyses/i32/procurement_completion/native/candidate_kicad/models/ENVELOPE_TDK_CGA4J1_33N_I32.step
2.45 x 1.50 x 1.50 mm
