tranquilWorks/gr86-cca-telemetry/docs/engineering/rvb22/analyses/i32/procurement_completion/native/candidate_kicad/models/ENVELOPE_TI_DDA0008B_4214849B.step

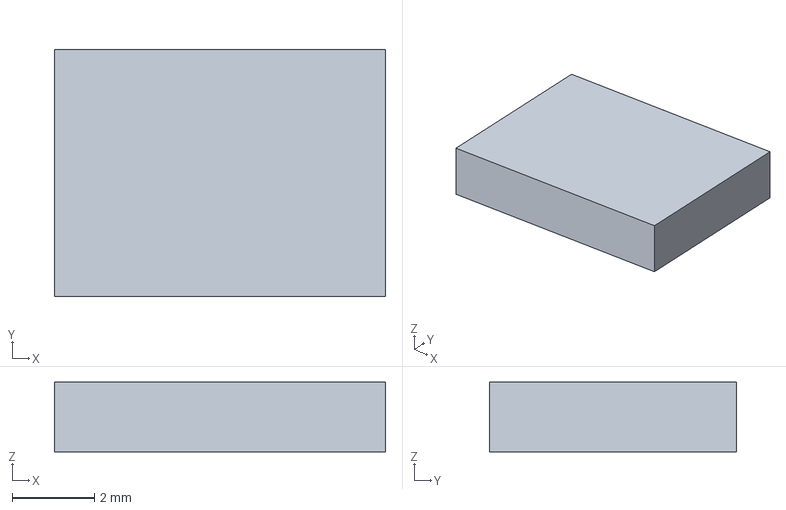
[picture p35: CAD file, 2026-09-14]
docs/engineering/rvb22/analyses/i32/procurement_completion/native/candidate_kicad/models/ENVELOPE_TI_DDA0008B_4214849B.step
8.05 x 6.00 x 1.70 mm
