tranquilWorks/gr86-cca-telemetry/docs/engineering/rvb22/analyses/convergence_01/run_review.py

#!/usr/bin/env python3
"""Source-bound product convergence checks. Engineering completion != qualification.

The baseline register is preserved. Results distinguish repeatable checks,
reused bounded analysis, redesign work and physical-only acceptance.
"""
from __future__ import annotations
import argparse, copy, csv, hashlib, json, re, sys
from collections import Counter
from pathlib import Path
D=Path(__file__).resolve().parent
sys.path.insert(0,str(D/'support'))
import sexpdata as sx
import check_combined_copper as c
W=D.parents[1]
PCB_HASH='52ca35cf8cb4e2b4a27d053686ee3a85564f1e94dfdb7dcb4bca4083dd527312'
I32=W/'analyses/i32/procurement_redline'
FROZEN_REFS={'C152','C154','C165','L121','R155','R156','R160','R161','R162','R163','R169','R170','U101'}
REFERENCE_PCB_HASH=('5b373f6033fdbd18f126f8ca054b619abada2568778c5a8fc303c4e756fb06c8')
FILLED_HASH='896ca56bf4ad836d63b84537cfd20bfcbf1783c60ac5d92ab7c7783d54f57e92'

def digest(path):return hashlib.sha256(Path(path).read_bytes()).hexdigest()
def read(path):return json.loads(Path(path).read_text())
def save(path,data):Path(path).write_text(json.dumps(data,indent=2,ensure_ascii=False)+'\n')
def fp_map(tree):return {c.prop(f)['Reference']:f for f in c.child(tree,'footprint')}
def pins(f):return {str(p[1]):str(c.get(p,'net')[1])for p in c.child(f,'pad')if c.get(p,'net')}
def require(ok,msg):
    if not ok:raise ValueError(msg)
def fitted(f):return c.prop(f).get('Assembly')in('FACTORY','MANUAL_GPS')

def receive_only(tree,sketch):
    fs=fp_map(tree);p=c.prop
    require(p(fs['R301'])['Assembly']=='DNP','R301 must be unpopulated in receive-only product')
    require(pins(fs['R301'])=={'1':'CAN_TX_MCU','2':'CAN_TXD'},'Unexpected TX isolation topology')
    require(fitted(fs['R303'])and p(fs['R303'])['MPN']=='CRCW060310K0FKEA','Missing exact fitted 10k recessive pull-up')
    require(pins(fs['R303'])=={'1':'+3V3','2':'CAN_TXD'},'Pull-up wiring changed')
    require(pins(fs['U301'])['1']=='CAN_TXD','TXD pin route changed')
    require(p(fs['R306'])['Assembly']=='DNP','Permanent bus termination must remain unpopulated')
    # No other fitted two-terminal link may bypass R301; examine physical population, not only firmware strings.
    bypass=[]
    for ref,f in fs.items():
        ns=set(pins(f).values())
        if fitted(f) and ns=={'CAN_TX_MCU','CAN_TXD'}:bypass.append(ref)
    require(not bypass,'Fitted TX bridge: '+str(bypass))
    code=re.sub(r'/\*.*?\*/|//[^\n]*','',sketch,flags=re.S)
    require(len(re.findall(r'\bTWAI_MODE_LISTEN_ONLY\b',code))==1,'Listen-only mode missing or ambiguous')
    require(not re.search(r'\bTWAI_MODE_(NORMAL|NO_ACK)\b|\btwai_transmit\s*\(',code),'Transmit-enabled code path present')
    require(re.search(r'general\.tx_queue_len\s*=\s*0\s*;',code),'Transmit queue not disabled')
    for gpio,num in [('CAN_TX_GPIO',5),('CAN_RX_GPIO',4)]:
        require(re.search(r'\b'+gpio+r'\s*=\s*'+str(num)+r'\s*;',code),'CAN pin mapping changed')
    return {'status':'PASS_SOURCE_RECEIVE_ONLY_VARIANT','isolating_link':'R301 DNP','recessive_pullup':'R303 10k +3V3 to TXD','termination':'R306 DNP','transmit_calls':0,'tx_queue_length':0,'six_CAN_TX_reference_gaps':'Real geometry findings, but on an isolated MCU stub, not the populated CAN receiver path. Do not reroute active power solely to erase these flags.','valid_only_for':'Exact receive-only BOM and firmware configuration. A future transmit-enabled variant requires renewed route/reference review.','not_proven':'Powered-off or internally failed transceiver behavior, shorts across the DNP link, real bus loading and vehicle non-interference.'}

def led_review(tree,header):
    fs=fp_map(tree);rows=[]
    # The selected 1k/1% part is screened with an explicit conservative 2% additional thermal resistance allowance.
    rmin=1000*.99*.98;rmax=1000*1.01*1.02;vmax=3.6
    for idx,(signal,gpio,pad) in enumerate([('PWR',15,'8'),('BLE',6,'6'),('CAN',7,'7'),('GPS',8,'12'),('SYS',10,'18'),('OIL',9,'17')],1):
        rr,dd=f'R60{idx}',f'D60{idx}';rn='LED_'+signal;an=rn+'_A'
        require(fitted(fs[rr])and fitted(fs[dd]),rr+' or '+dd+' not populated')
        require(c.prop(fs[rr])['MPN']=='CRCW06031K00FKEA','Unexpected LED resistor')
        require(c.prop(fs[dd])['MPN']=='APT1608SGC','Unexpected LED MPN')
        require(pins(fs[rr])=={'1':rn,'2':an}and pins(fs[dd])=={'1':'GND','2':an},'LED chain/polarity error '+signal)
        require(pins(fs['U201'])[pad]==rn,'Module LED pad net mismatch '+signal)
        require(re.search(r'#define\s+LED_'+signal+r'_GPIO\s+'+str(gpio)+r'\b',header),'Firmware LED GPIO mismatch')
        require(re.search(r'#define\s+LED_'+signal+r'_ACTIVE_LOW\s+0\b',header),'Firmware polarity mismatch')
        rows.append({'resistor':rr,'LED':dd,'signal':signal,'GPIO':gpio,'U201_pad':pad,'R_min_ohm':rmin,'R_max_ohm':rmax,'hard_current_upper_mA':1000*vmax/rmin,'resistor_power_upper_mW':1000*vmax*vmax/rmin,'brightness_lower_bound_mcd':0,'brightness_note':'No guaranteed positive luminance can be deduced at this low-current operating point from the available limits. This is not a claimed optical pass.'})
    return {'status':'PASS_ELECTRICAL_CHAIN_AND_FINITE_CURRENT_BOUND_OPTICAL_ACCEPTANCE_SEPARATE','rows':rows,'all_six_current_upper_mA':sum(r['hard_current_upper_mA']for r in rows),'allocation_notes':['3.6V operating ceiling; LED Vf is conservatively set to zero for the current upper bound.','Resistor minimum includes 1% initial tolerance and an additional 2% thermal decrease, an engineering allowance rather than a measured resistor temperature.','Current upper bounds do not assert a guaranteed loaded GPIO high voltage or light output.'],'respin_disposition':'Existing current-limited standard 0603 resistor/LED footprints permit assembly-value or optical-bin tuning without a new PCB layout. No brightness-dependent safety or measurement function is credited.','original_WCA_07_closed':False}

def current_handling(tree,old):
    """Bind the exact 177-part I32 inventory; retain unknown supplier limits."""
    inventory={r['Reference']:r for r in csv.DictReader((W/'current/i32_manufacturing/assembly/COMPLETE_FITTED_BOM.csv').open())}
    previous_by_ref={ref:r for r in old['rows']for ref in r['references'].split()}
    by_mpn={r['mpn']:r for r in old['rows']};groups={};excluded=[];historical=[]
    actual={ref:f for ref,f in fp_map(tree).items() if fitted(f)}
    require(len(inventory)==177 and set(actual)==set(inventory),'Unexpected fitted reference count or identity')
    for ref,f in fp_map(tree).items():
        p=c.prop(f);mpn=p.get('MPN','')
        if ref not in actual:excluded.append({'reference':ref,'assembly':p.get('Assembly'),'mpn':mpn});continue
        require(mpn==inventory[ref]['MPN'],'New fitted MPN needs explicit handling review: '+mpn)
        groups.setdefault(mpn,[]).append(ref)
        if ref not in previous_by_ref or previous_by_ref[ref]['mpn']!=mpn:
            historical.append({'reference':ref,'before':previous_by_ref.get(ref,{}).get('mpn'),'after':mpn})
    rows=[]
    for mpn,refs in sorted(groups.items()):
        if mpn in by_mpn:r=copy.deepcopy(by_mpn[mpn])
        elif mpn=='LM5164QDDARQ1':
            r={'mpn':mpn,'manufacturer':'Texas Instruments','process':'GLOBAL_REFLOW','msl':2,'manufacturer_peak_C':260,'source':'https://www.ti.com/product/LM5164-Q1/part-details/LM5164QDDARQ1','source_evidence':'TI_CURRENT_QUALITY_INFO_AUTOMOTIVE_DDA8_MSL2_260C_1YEAR_REVIEWED_2026_09_12','handling':'TI lists this active automotive DDA-8 option with NiPdAuAg lead finish, MSL Level 2, 260C peak reflow and one-year floor life. Preserve dry-pack/MSL controls and the incoming lot label as the assembly-process authority.','current_release_condition':'Use the board-wide compatible lead-free reflow process within the package limit. Incoming lot labeling and assembler process controls remain authoritative; no physical solder-joint acceptance is claimed here.'}
        else:
            r={'mpn':mpn,'manufacturer':inventory[refs[0]]['Manufacturer'],
               'process':'FACTORY_PROCESS_REQUIRES_INCOMING_LOT_APPROVAL','msl':None,'manufacturer_peak_C':None,
               'source':'docs/engineering/rvb22/current/i32_manufacturing/assembly/COMPLETE_FITTED_BOM.csv',
               'source_evidence':'EXACT_CURRENT_I32_IDENTITY; PACKAGE_QUALIFICATION.json; supplier limits remain explicit',
               'handling':'Exact native MPN and package are controlled. No numeric MSL or production peak is inferred from package size or a related ordering option.',
               'current_release_condition':'Assembler must apply the exact incoming lot MSL, floor-life, peak-temperature and cleaning restrictions. Unknown limits remain supplier acceptance gates.'}
        if set(refs)&{'F101','U401'}:
            require(set(refs)<= {'F101','U401'},'Local/factory handling grouping changed')
            r.update(process='LOCAL_MANUAL_INSTALLATION',current_release_condition='Retain F101/U401 local installation after factory assembly.')
        if mpn=='BPCI00121280470M00':
            r.update(process='FACTORY_MANUAL_OR_WAVE',msl=None,manufacturer_peak_C=None,
                     source='https://jlcpcb.com/partdetail/C6471075',
                     source_evidence='LIVE_JLC_SOURCEABILITY.json: manualWeld / public Wave Soldering',
                     current_release_condition='Factory supplied; supplier process and orientation approval required. This is not proof of machine SMT handling or a third local-install exception.')
        if mpn=='LTC4367HMS8#PBF':
            r['ordering_pedigree']='Owner accepts loss of #W controlled-manufacturing pedigree; functional H-grade equivalence only.'
        r.update(references=' '.join(sorted(refs)),quantity=len(refs));rows.append(r)
    changes=read(I32/'SOURCE_AUDIT.json')['part_changes']
    changed=[{'reference':ref,'before':changes[ref]['before']['properties']['MPN'],'after':inventory[ref]['MPN']}for ref in sorted(FROZEN_REFS)]
    return {'status':'CURRENT_I32_SOURCE_MPN_INVENTORY_RECONCILED','unique_fitted_MPNs':len(rows),'fitted_references':177,
            'factory_placements':175,'local_install':['F101','U401'],'rows':rows,'excluded':excluded,
            'corrected_references':changed,'historical_changes_since_I22':historical,
            'MSL_primary_known_MPNs':sum(r['msl']is not None for r in rows),
            'numeric_MSL_primary_known_MPNs':sum(isinstance(r['msl'],int)for r in rows),
            'unknown_msl_MPNs':sum(r['msl']is None for r in rows),
            'physical_assembly_acceptance':False,'automatic_turnkey_PCBA_order_ready':False}

def verify_regressions(pcb,firmware):
    n=read(I32/'manufacturing_audit_final/RESULTS.json');f=read(D/'results/FIRMWARE_REGRESSION.json')
    require(digest(pcb)==PCB_HASH,'Candidate PCB changed; invalidate/re-run affected evidence')
    require(n['source_PCB_sha256']==PCB_HASH and n['filled_PCB_sha256']==FILLED_HASH,'Current I32 native reference binding mismatch')
    require(n['independent_manufacturing_status']=='PASS_INTENDED_COPPER_AND_EXPORTS','Independent native/export review failed')
    require(all(n[x]==0 for x in ['native_DRC','native_unconnected','native_parity','native_ERC']),'Native findings present')
    require(f['status']=='PASS' and len(f['results'])==9 and all(x['passed']for x in f['results']),'Firmware regression failure')
    for path,sha in f['source_files_sha256'].items():require(digest(firmware/path)==sha,'Firmware changed since regression: '+path)
    return {'native_postconditions':n['native_postconditions_passed'],'intended_nets':n['continuity']['nets'],'disconnected_pad_nets':n['continuity']['disconnected_pad_nets'],'firmware_suites':len(f['results']),'firmware_exact_source_files_bound':len(f['source_files_sha256']),'CAD_native_run_reused':'I32 procurement_redline/native_final','native_copper_and_exports_independently_recomputed_this_iteration':False,'current_source_hash_binding_verified_this_execution':True,'fresh_KiCad_execution_this_iteration':False,'ASan':True,'UBSan':True,'physical_testing':False}

def main():
    ap=argparse.ArgumentParser();ap.add_argument('--out',type=Path,default=D/'results/review');ap.add_argument('--evidence-root',type=Path,default=W);a=ap.parse_args();a.out.mkdir(parents=True,exist_ok=True)
    pcb=W/'candidate/cad/GR86_CCA_RevB.kicad_pcb';fw=W/'candidate/firmware';tree=sx.loads(pcb.read_text());current=read(W/'FINAL_REVIEW_REGISTER.json');reg=read(W/current['historical_290_row_register'])
    evidence=verify_regressions(pcb,fw)
    rx=receive_only(tree,(fw/'cca_telemetry/cca_telemetry.ino').read_text());led=led_review(tree,(fw/'cca_telemetry/src/led_status.h').read_text())
    old=read(D/'support/HANDLING_I22.json');handling=current_handling(tree,old);handling['pcb_sha256']=digest(pcb)
    for name,data in [('RECEIVE_ONLY_DISPOSITION',rx),('LED_REVIEW',led),('CURRENT_HANDLING_REGISTER',handling),('REGRESSION_BINDING',evidence)]:save(a.out/(name+'.json'),data)
    # I32 supersedes the historical 153-part review recipe below. Preserve its
    # logic for traceability, while current output is bound to the actual redline.
    final=read(I32/'FINAL_REDLINE_VERIFICATION.json')
    require(final['source_PCB_sha256']==PCB_HASH and len(final['gates'])==14 and all(final['gates'].values()),'I32 aggregate gates incomplete')
    require(current['PCB_sha256']==PCB_HASH and len(current['rows'])==11,'Current I32 supplement identity mismatch')
    require(len(reg['rows'])==290 and len({r['id']for r in reg['rows']})==290,'Criterion identity loss')
    coverage=[{'id':r['id'],'original_status':r['closure'],'retained_desktop_status':r['desktop_status'],
               'remaining_original_condition':r.get('remaining',''),'physical_test_claimed':False}for r in reg['rows']]
    save(a.out/'ALL_CRITERIA_COVERAGE.json',{'criterion_count':290,'original_counts':dict(Counter(r['closure']for r in reg['rows'])),
         'rows':coverage,'meaning':'Original 290-row ledger retained; affected I32 gates are in FINAL_REDLINE_VERIFICATION.json. No fresh adjudication of all 290 criteria is claimed.'})
    summary={'status':'PASS_CURRENT_I32_SOURCE_AND_EXECUTED_FIRMWARE_REGRESSIONS','source_PCB_sha256':PCB_HASH,
             'original_criteria':dict(Counter(r['closure']for r in reg['rows'])),'all_290_rows_retained':True,'current_I32_findings':11,
             'regression':evidence,'corrected_handling_refs':handling['corrected_references'],
             'current_redline_desktop_gates':final['gates'],'remaining_supplier_gates':final['remaining_supplier_gates'],
             'remaining_physical_gates':final['remaining_physical_gates'],'physical_tests':0,'fabrication_release':False}
    save(a.out/'SUMMARY.json',summary);print(json.dumps(summary,indent=2))
    return
    original_counts=Counter(r['closure']for r in reg['rows']);coverage=[];filechecks={}
    for r in reg['rows']:
        files=[]
        for p,expected in r.get('evidence_sha256',{}).items():
            if p not in filechecks:
                q=a.evidence_root/p
                filechecks[p]={'path':p,'exists':q.is_file(),'expected_historical_sha256':expected,'actual_sha256':digest(q)if q.is_file()else None}
            files.append(filechecks[p])
        status=r['desktop_status']; category=''; action='';domain=r['id'].split('-')[0]
        if r['closure']=='na':category='NOT_APPLICABLE_RETAINED';action='Original not-applicable rationale retained; no fabricated result.'
        elif r['id']in ('REG-02','THERM-02'):
            category='I25_CONDITIONAL_DESKTOP_COMPLETE_PHYSICAL_GATE';action='I25/C04 controls the2.940859375W release allocation,<=0.45A current and>=80percent efficiency. Execute I26-PWR-01/I26-THERM-01; do not revive the superseded4.815W release model or claim measured hot spots.'
        elif r['id']=='GND-02':
            category='RETURN_TRANSFER_DESKTOP_WORK_REMAINING';action='All54 historical UUIDs reconciled:48 removed,6 isolated TX stub. Expanded scope includes2CAN_RXD pre-resistor gaps and60signal-via transfers; validate actual plane-transfer corridors, edge/receiver margins and etched necks before closing GND-02.'
        elif r['id']=='WCA-07':
            category='LED_DESKTOP_COMPLETE_INSTALLED_VISIBILITY_GATE';action='I26 bounds7fittedLEDs including D401/U404; retains1kohm and a zero guaranteed hot low-current optical minimum. Execute I26-LED-01 current/thermal/photometry/dashboard recognition gates. Legacy LED_REVIEW covers the six GPIO channels only; the controlling seven-channel report is analyses/i26/LED_BOUND.json.'
        elif domain=='THERM':
            category='I25_THERMAL_SCOPE_RETAINED';action='I25 governs adopted release cooling and model assumptions. Preserve original row-specific limits and physical correlation; unadopted C02 mechanics are contingency-only.'
        elif status=='COMPLETED_CONDITIONAL_MODEL':
            category='BOUNDED_ANALYSIS_RETAINED';action='Existing finite assumptions and failure cases remain explicit. Do not turn missing universal supplier guarantees into endless new calculations; do not imply an unknown is proven.'
        elif r['closure']=='closed':
            category='PRIOR_DESIGN_SCOPE_RETAINED';action='Retain original design-scope disposition, subject to source-dependency invalidation after the coordinated redesign. This is not a new physical or independent-human pass.'
        else:
            category='EXTERNAL_ACCEPTANCE_PARKED';action='Original test/supplier/installation requirement remains open outside this desktop completion denominator. Any design implication remains in its applicable engineering workstream.'
        coverage.append({'id':r['id'],'domain':r['B'],'original_status':r['closure'],'original_question':r['E'],'original_required_evidence':r['F'],'desktop_workstream':category,'disposition':action,'remaining_original_condition':r.get('remaining',''),'evidence_count':len(files),'missing_evidence_paths':[f['path']for f in files if not f['exists']],'changed_historical_evidence_paths':[f['path']for f in files if f['exists']and f['actual_sha256']!=f['expected_historical_sha256']],'post_redesign_review_required':r['closure']!='na','physical_test_claimed':False})
    require(len(coverage)==290 and len({r['id']for r in coverage})==290,'Criterion identity loss')
    save(a.out/'ALL_CRITERIA_COVERAGE.json',{'criterion_count':290,'original_counts':dict(original_counts),'workstream_counts':dict(Counter(r['desktop_workstream']for r in coverage)),'meaning':'Coverage/triage and dependency register, NOT 290 fresh engineering passes. Historical statuses are not rewritten by taxonomy.','rows':coverage})
    save(a.out/'EVIDENCE_AVAILABILITY.json',{'file_count':len(filechecks),'files':list(filechecks.values()),'hash_match_is_not_engineering_acceptance':True})
    summary={'status':'PASS_EXECUTED_SOURCE_AND_REGRESSION_CHECKS_CONVERGENCE_REMAINS_OPEN','source_PCB_sha256':digest(pcb),'original_criteria':dict(original_counts),'all_290_rows_retained':True,'actionable_DESKTOP_WORK_REMAINING':[r['id']for r in reg['rows']if r['desktop_status']=='DESKTOP_WORK_REMAINING'],'regression':evidence,'corrected_handling_refs':handling['corrected_references'],'actual_PCB_routing_changes_this_iteration':False,'finished_all_desktop_work':False,'fabrication_release':False,'notes':['The user means avoiding another PCB order AFTER first fabrication, not preserving the current draft.','Free pre-fabrication redesign is authorized within the product scope.','Changing taxonomy does not count as closing original criteria.','GND-02 is the remaining actionable desktop criterion. Thermal is I25 conditional-model complete; physical correlation remains mandatory.','The user-selected851/960 chain is retained;851 must remain in an installed accessory zone<=60C.']}
    save(a.out/'SUMMARY.json',summary);print(json.dumps(summary,indent=2))
if __name__=='__main__':main()
