tranquilWorks/gr86-cca-telemetry/docs/engineering/rvb22/analyses/convergence_01/native_binding.py

"""Pin source-authored electrical/manufacturing content across native KiCad refill."""
from pathlib import Path
import hashlib
import json
import sys
sys.path.insert(0, str(Path(__file__).resolve().parent / "support"))
import sexpdata as sx

SOURCE_HASH = "a04f42b358fa65a332128115a7b648e1a2297531ecb47466ac24697de536a936"
SOURCE_PCB = Path(__file__).resolve().parents[2] / "candidate" / "cad" / "GR86_CCA_RevB.kicad_pcb"
DERIVED_OR_SERIALIZER_TAGS = {"filled_polygon", "generator", "generator_version"}
FOOTPRINT_SEMANTIC_TAGS = {
    "layer", "at", "property", "pad", "attr", "zone_connect", "clearance",
    "solder_mask_margin", "solder_paste_margin", "solder_paste_ratio",
    "thermal_width", "thermal_gap",
}

def _stable_key(value):
    return json.dumps(value,separators=(",",":"),ensure_ascii=False,sort_keys=True)

def _tag(node):
    return str(node[0]) if isinstance(node,list) and node else ""

def _layer(node):
    return next((str(x[1]) for x in node[1:] if isinstance(x,list) and len(x)>1 and _tag(x)=="layer"),None)

def _is_copper_layer(layer):
    return bool(layer) and (layer.endswith('.Cu') or layer=='*.Cu')

def canonicalize(node):
    """Return the source-vs-native semantic electrical/manufacturing signature."""
    if not isinstance(node,list):
        if isinstance(node,sx.Symbol):
            return str(node)
        # KiCad serializers may spell the same numeric coordinate as 82 or 82.0.
        # Canonicalize only exact integral floats; all non-integral values remain exact.
        if isinstance(node,float) and node.is_integer():
            return int(node)
        return node
    tag=_tag(node)
    if tag in DERIVED_OR_SERIALIZER_TAGS:
        return None

    # KiCad may omit an explicit zero rotation from an otherwise identical placement.
    if tag=="at" and len(node)==4 and isinstance(node[-1],(int,float)) and float(node[-1])==0.0:
        node=node[:-1]

    # Layer membership is set-like; preserve exact membership while ignoring order.
    if tag=="layers":
        values=[canonicalize(x) for x in node[1:]]
        return [canonicalize(node[0])]+sorted(values,key=_stable_key)

    if tag=="footprint":
        # Bind electrical/population-bearing footprint semantics while ignoring KiCad's
        # serializer-specific Fab/Silk/Courtyard drawing transformations.
        head=[canonicalize(node[0])]
        if len(node)>1 and not isinstance(node[1],list):head.append(canonicalize(node[1]))
        children=[]
        for x in node[1:]:
            if not isinstance(x,list) or not x:continue
            xt=_tag(x); layer=_layer(x)
            if xt in FOOTPRINT_SEMANTIC_TAGS or (xt.startswith('fp_') and _is_copper_layer(layer)):
                value=canonicalize(x)
                if value is not None:children.append(value)
        return head+sorted(children,key=_stable_key)

    omit_id = tag=="property"
    out=[]
    for x in node:
        if omit_id and isinstance(x,list) and x and _tag(x)=="uuid":
            continue
        value=canonicalize(x)
        if value is not None:out.append(value)
    if tag=="kicad_pcb" and out:
        return [out[0]]+sorted(out[1:],key=_stable_key)
    return out

def content_hash(node):
    data=json.dumps(canonicalize(node),separators=(",",":"),ensure_ascii=False).encode()
    return hashlib.sha256(data).hexdigest()

def first_difference(a,b,path=()):
    if type(a) is not type(b):return path,a,b
    if isinstance(a,list):
        if len(a)!=len(b):
            for i,(x,y) in enumerate(zip(a,b)):
                d=first_difference(x,y,path+(i,))
                if d is not None:return d
            return path+("len",),len(a),len(b)
        for i,(x,y) in enumerate(zip(a,b)):
            d=first_difference(x,y,path+(i,))
            if d is not None:return d
        return None
    if a!=b:return path,a,b
    return None

def describe_path(root,path):
    node=root;parts=[]
    for p in path:
        if p=="len":parts.append("len");break
        if not isinstance(node,list) or not isinstance(p,int) or p>=len(node):parts.append(str(p));break
        tag=_tag(node) or "[]";parts.append(f"{tag}[{p}]");node=node[p]
    return "/".join(parts)

def verify_filled(path, *, source_pcb=None, expected_source_hash=None):
    # Explicit source and digest must travel together. Historical callers keep
    # their immutable default; a new run cannot silently adopt the current file.
    if (source_pcb is None) != (expected_source_hash is None):
        raise ValueError("Explicit source PCB requires its expected SHA256")
    controlled = SOURCE_PCB if source_pcb is None else Path(source_pcb)
    expected = SOURCE_HASH if expected_source_hash is None else expected_source_hash
    source_data=controlled.read_bytes();source_raw=hashlib.sha256(source_data).hexdigest()
    if source_raw!=expected:raise ValueError("Controlled PCB source advanced: explicit engineering rebind required")
    source_tree=sx.loads(source_data.decode());source_canon=canonicalize(source_tree);reference_content=content_hash(source_tree)
    data=Path(path).read_bytes();raw=hashlib.sha256(data).hexdigest();native_tree=sx.loads(data.decode());native_canon=canonicalize(native_tree);stable=content_hash(native_tree)
    if stable!=reference_content:
        d=first_difference(source_canon,native_canon)
        detail="hash differs without structural diff" if d is None else f"first_difference={d[0]} semantic_path={describe_path(source_canon,d[0])} controlled={repr(d[1])[:240]} native={repr(d[2])[:240]}"
        raise ValueError("Native board electrical/manufacturing semantics differs from controlled source: explicit engineering rebind required; "+detail)
    return {"raw_sha256":raw,"content_sha256":stable,"controlled_source_raw_sha256":source_raw,"controlled_source_content_sha256":reference_content,"content_equal_to_controlled_source":True,"top_level_record_order_ignored":True,"zero_rotation_at_normalized":True,"integral_float_format_normalized":True,"pad_layer_order_ignored":True,"excluded_native_generated_tags":sorted(DERIVED_OR_SERIALIZER_TAGS),"footprint_semantic_tags":sorted(FOOTPRINT_SEMANTIC_TAGS),"native_refill_electrical_validation":"fresh DRC/export/copper checks remain required"}

if __name__=="__main__":
    import argparse
    parser=argparse.ArgumentParser(description=__doc__);parser.add_argument("pcb",type=Path);parser.add_argument("--out",type=Path);parser.add_argument("--source-pcb",type=Path);parser.add_argument("--expected-source-hash");args=parser.parse_args();result=verify_filled(args.pcb,source_pcb=args.source_pcb,expected_source_hash=args.expected_source_hash);text=json.dumps(result,indent=2)+"\n"
    if args.out:args.out.parent.mkdir(parents=True,exist_ok=True);args.out.write_text(text)
    print(text)
